Guiimartinho/esp32-s3-power-profiler/simulation/results/output_stage/README.md

# Simulation Results: Output Stage

Everything on this page is a simulation result. Nothing here is measured on
hardware. The page is written by `circuit-sim report` from the result files
beside it; do not edit it by hand.

## `output_stage/guard`

**The guard buffer: stability with the guard ring, static error, range change,
output off.**

The buffer copies the node after the shunts onto the guard ring through R119.
The loop gain of the buffer is taken by double injection at the output of the
amplifier, with the measured node behind the 1 kohm of range 0 and C71, which is
its highest impedance: without a ring, with the ring assumed for the board, with
ten times that ring, with C73 at half its value and with C73 left out. One
injection at the inverting input checks the method. A small-signal run gives the
frequency up to which the guard follows the node. Then the node is driven: a
step of 100 mV as a range change gives it, a dip to 1.1 V for 15 us as a short
circuit gives it, and a fall to 0 V at 0.8 V/ms as a released output gives it;
and it rests at 5 V and at 0.8 V, where the difference that is left between
guard and node is read.

Answers: sections 4.3, 4.8 and 10.3 (node after the shunts, buffer, guard ring),
D-32 and D-72.

| Figure | Simulated | Vendor models | Specification | Limits | Verdict | Source |
| --- | --- | --- | --- | --- | --- | --- |
| Phase margin, no ring capacitance | 92.06 ° | 117.8 ° | | at least 45 ° | pass | limit set here: 45 degrees; the specification states none |
| Crossover, no ring capacitance | 1.157 MHz | 1.507 MHz | | | | |
| Phase margin, assumed ring: 100 pF, 10 pF, 2 pF | 92.72 ° | 118.6 ° | | at least 45 ° | pass | limit set here: 45 degrees; the specification states none |
| Crossover, assumed ring: 100 pF, 10 pF, 2 pF | 1.147 MHz | 1.489 MHz | | | | |
| Phase margin, ten times the assumed ring | 96.84 ° | 123.9 ° | | at least 45 ° | pass | limit set here: 45 degrees; the specification states none |
| Crossover, ten times the assumed ring | 1.147 MHz | 1.549 MHz | | | | |
| Phase margin, assumed ring, C73 at half its value | 91.36 ° | 117.5 ° | | at least 45 ° | pass | limit set here: 45 degrees; the specification states none |
| Crossover, assumed ring, C73 at half its value | 1.144 MHz | 1.479 MHz | | | | |
| Phase margin, assumed ring, C73 not fitted | 55.61 ° | 72.97 ° | | | | |
| Crossover, assumed ring, C73 not fitted | 3.96 MHz | 4.986 MHz | | | | |
| Assumed ring: phase margin by one injection at the inverting input, less the one by double injection | -0.1481 ° | -0.02715 ° | | -3 ° to 3 ° | pass | check of the method; limit set here |
| Frequency up to which the guard follows the node within 3 dB | 34.73 kHz | 34.73 kHz | 33.83 kHz (+2.67 %) | 30.45 kHz to 37.21 kHz | pass | R119 with C73 and the ring, calculated here; limit 10 % around it |
| Peaking of the guard over the node | 0 dB | 0 dB | | at most 1 dB | pass | limit set here |
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
