Guiimartinho/esp32-s3-power-profiler/simulation/results/output_stage/guard.events.png

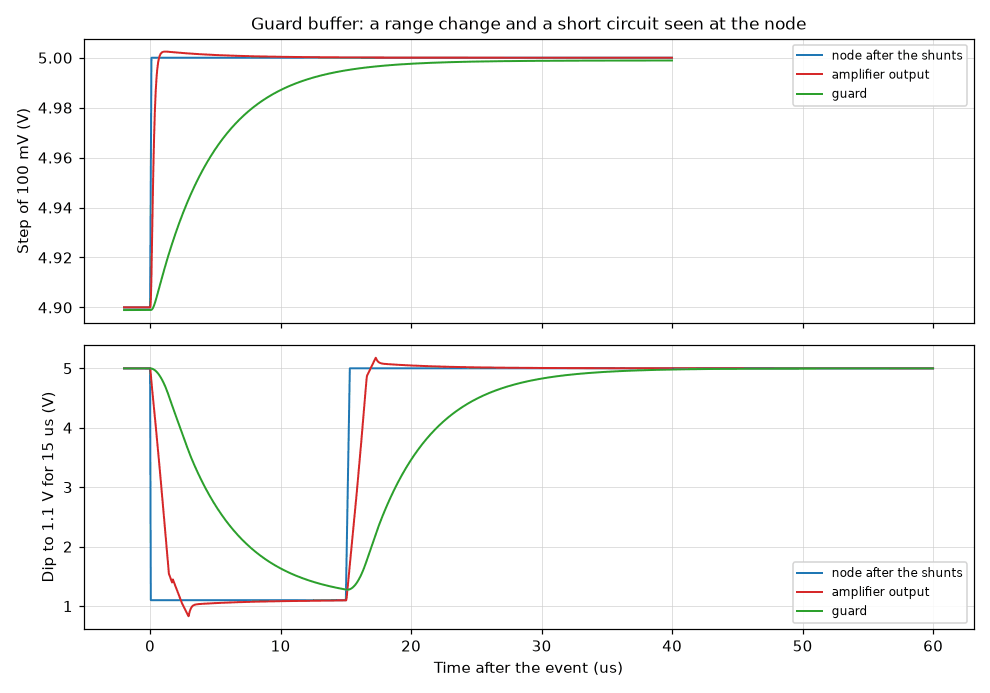
simulation/results/output_stage/guard.events.png
