Guiimartinho/esp32-s3-power-profiler/simulation/results/output_stage/guard.loop.png

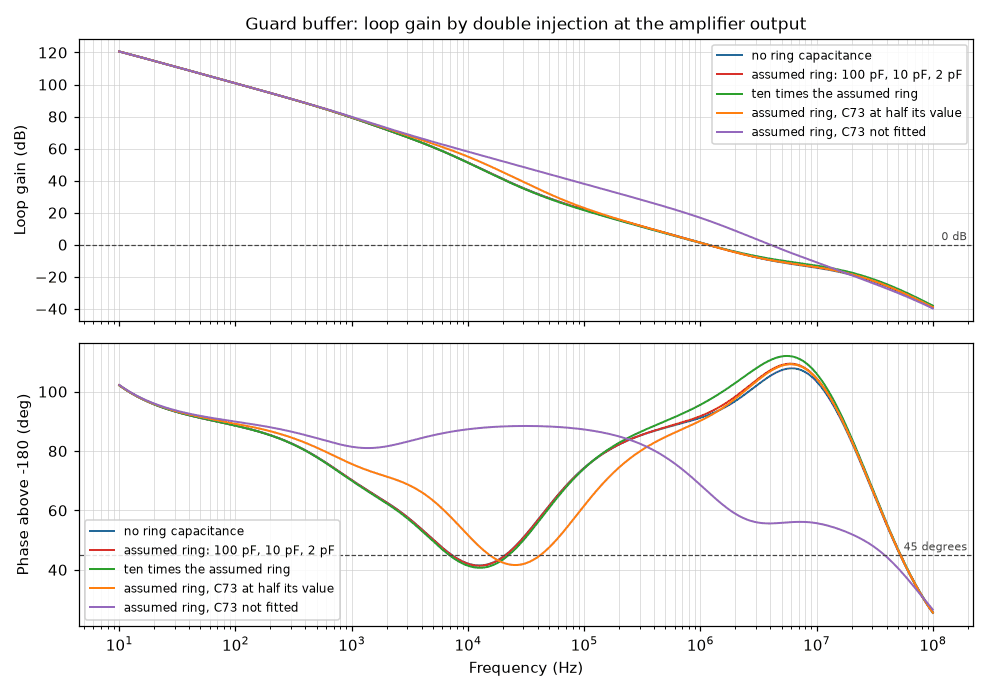
simulation/results/output_stage/guard.loop.png
