Guiimartinho/esp32-s3-power-profiler/simulation/results/output_stage/on-resistance.resistance.png

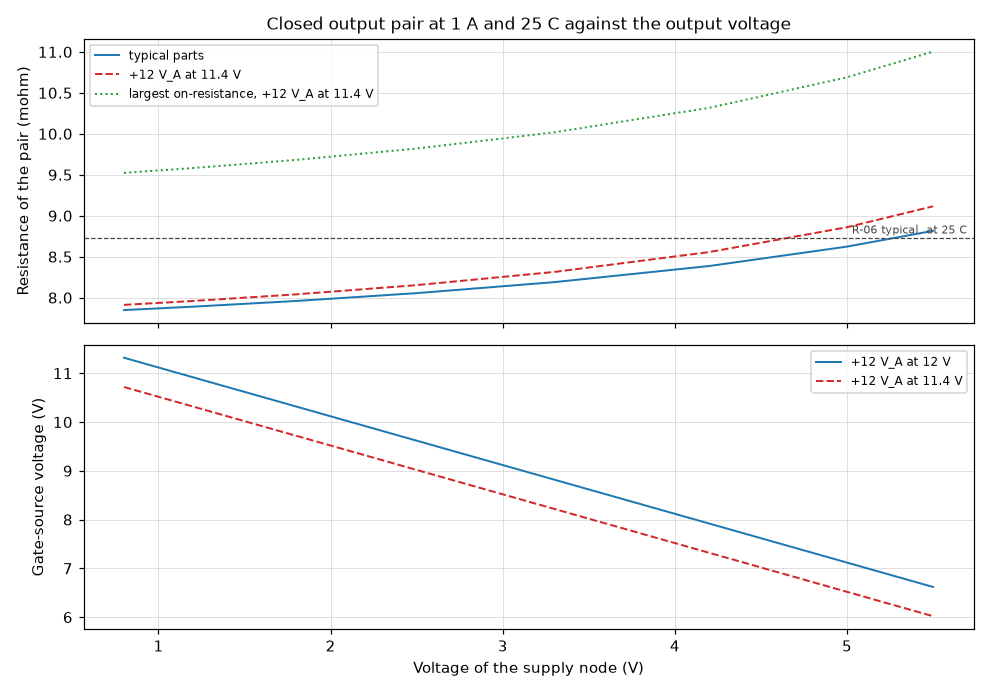
simulation/results/output_stage/on-resistance.resistance.png
