Guiimartinho/esp32-s3-power-profiler/simulation/results/output_stage/short-circuit.waveforms.png

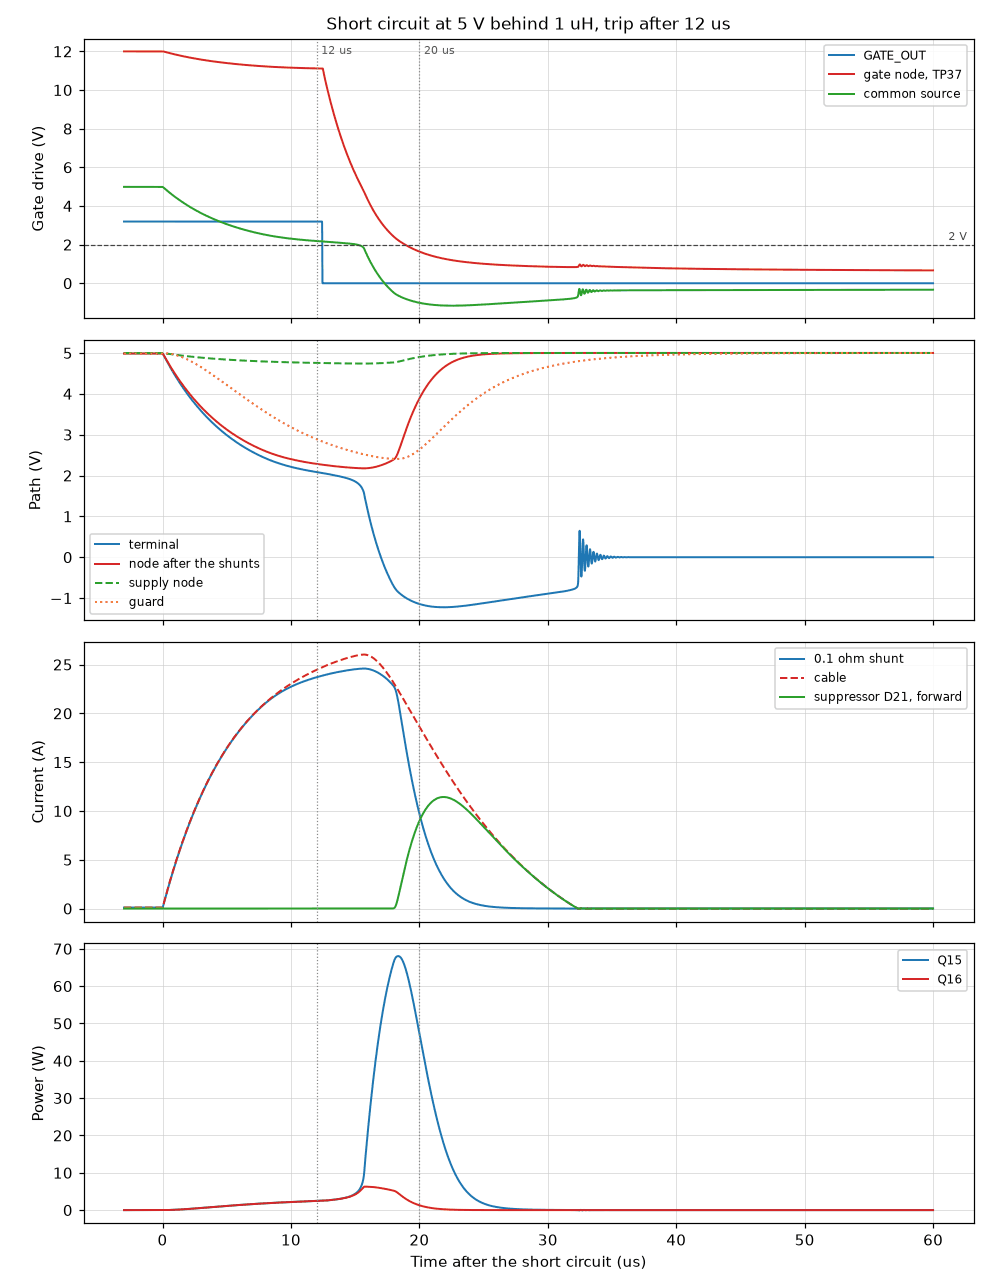
simulation/results/output_stage/short-circuit.waveforms.png
