Guiimartinho/esp32-s3-power-profiler/simulation/results/output_stage/terminal.charged.png

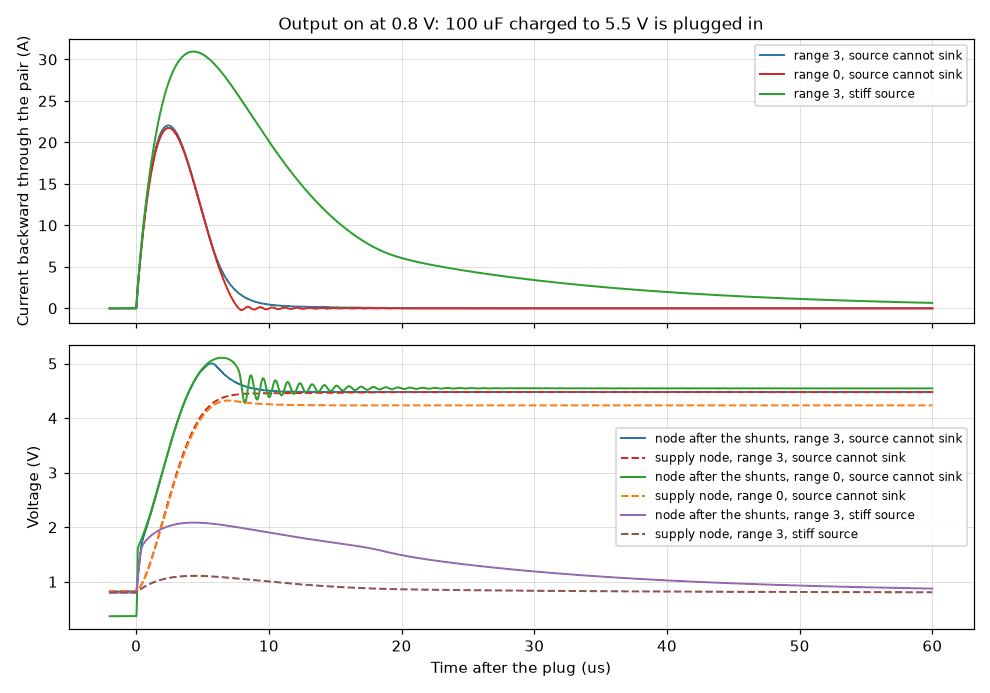
simulation/results/output_stage/terminal.charged.png
