Guiimartinho/esp32-s3-power-profiler/simulation/results/output_stage/terminal.reversed.png

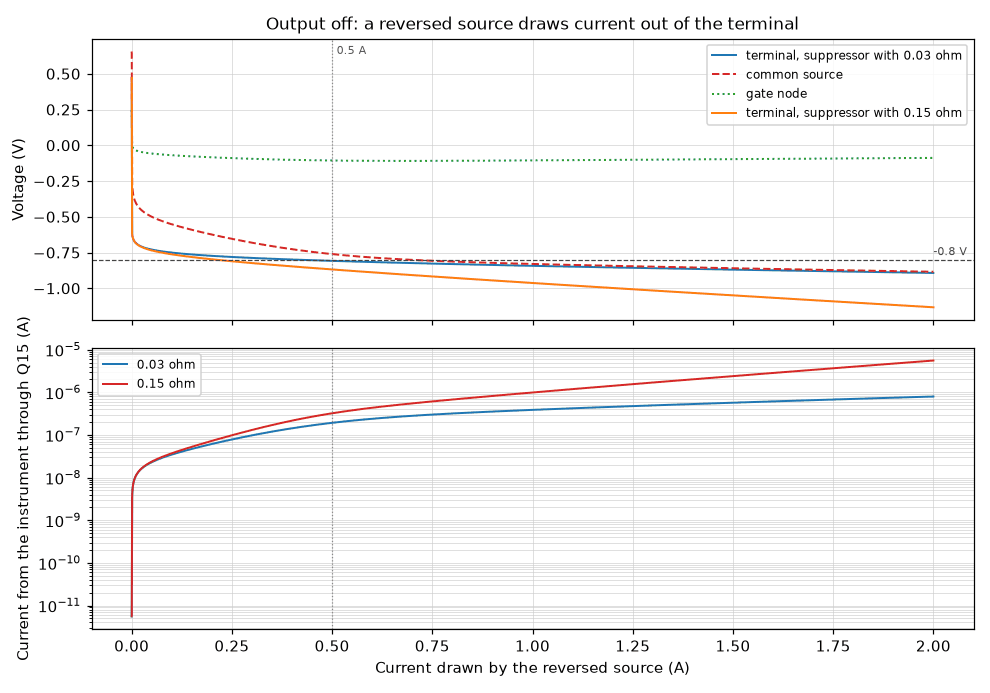
simulation/results/output_stage/terminal.reversed.png
