Guiimartinho/esp32-s3-power-profiler/simulation/results/output_stage/turn-off.plain.png

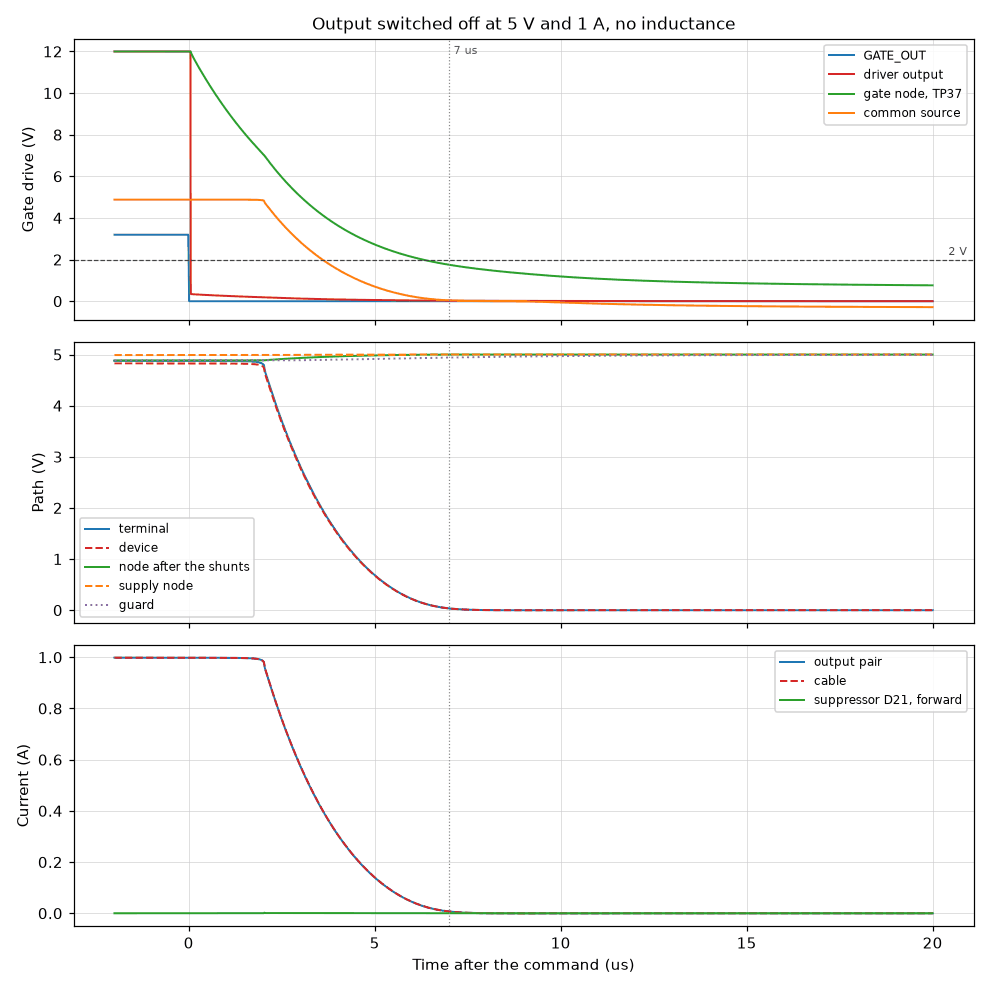
simulation/results/output_stage/turn-off.plain.png
