Guiimartinho/esp32-s3-power-profiler/simulation/results/output_stage/turn-on.faults.png

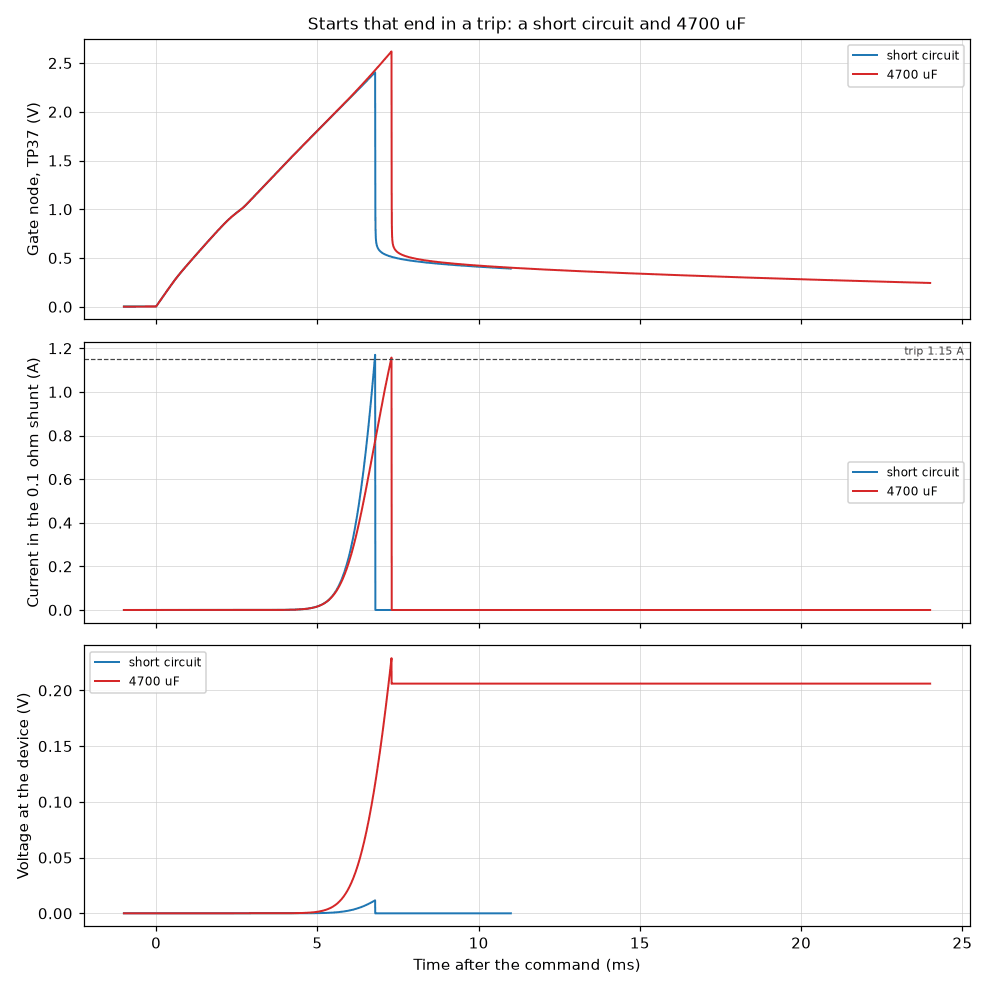
simulation/results/output_stage/turn-on.faults.png
