Guiimartinho/esp32-s3-power-profiler/simulation/results/output_stage/turn-on.gate-current.png

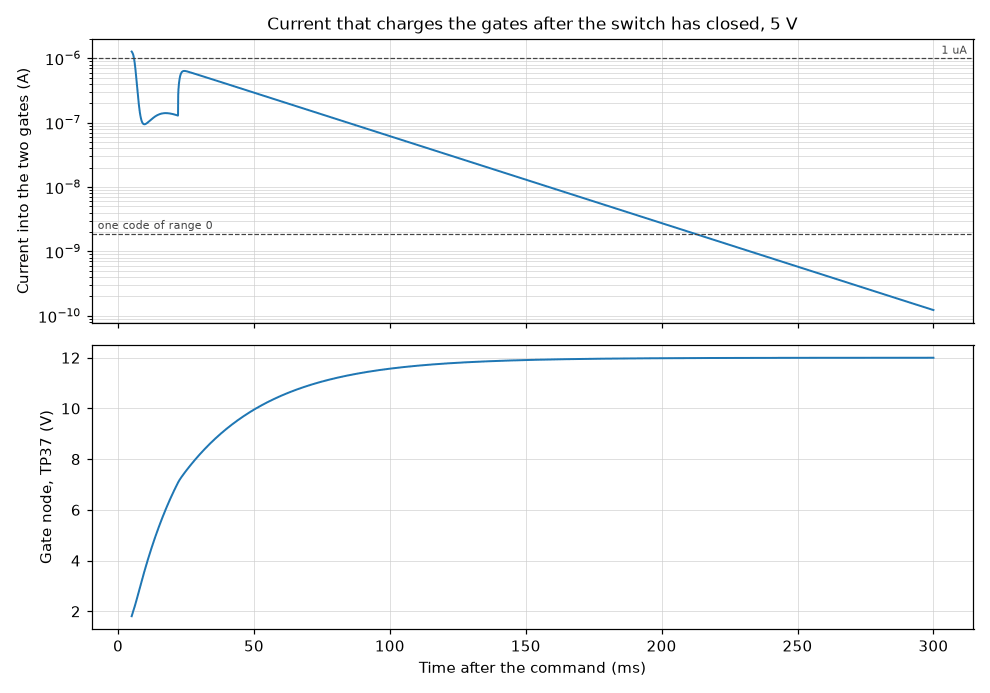
simulation/results/output_stage/turn-on.gate-current.png
