Guiimartinho/esp32-s3-power-profiler/simulation/results/output_stage/turn-on.inrush.png

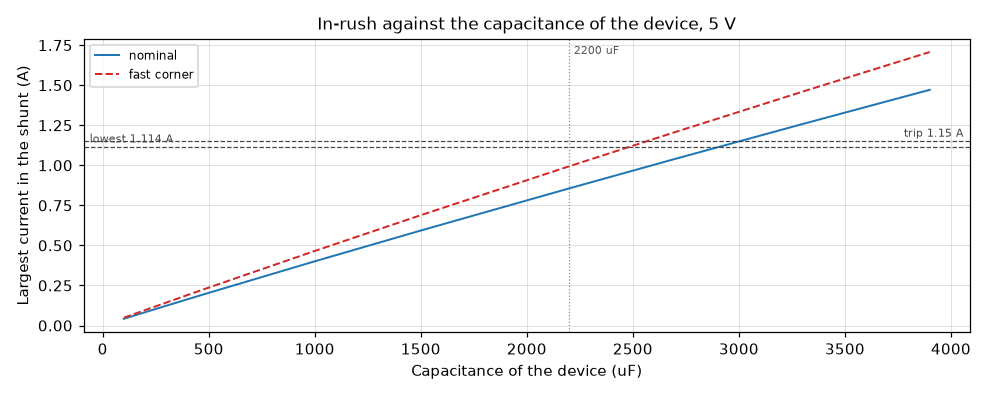
simulation/results/output_stage/turn-on.inrush.png
