Guiimartinho/esp32-s3-power-profiler/simulation/results/output_stage/turn-on.waveforms.png

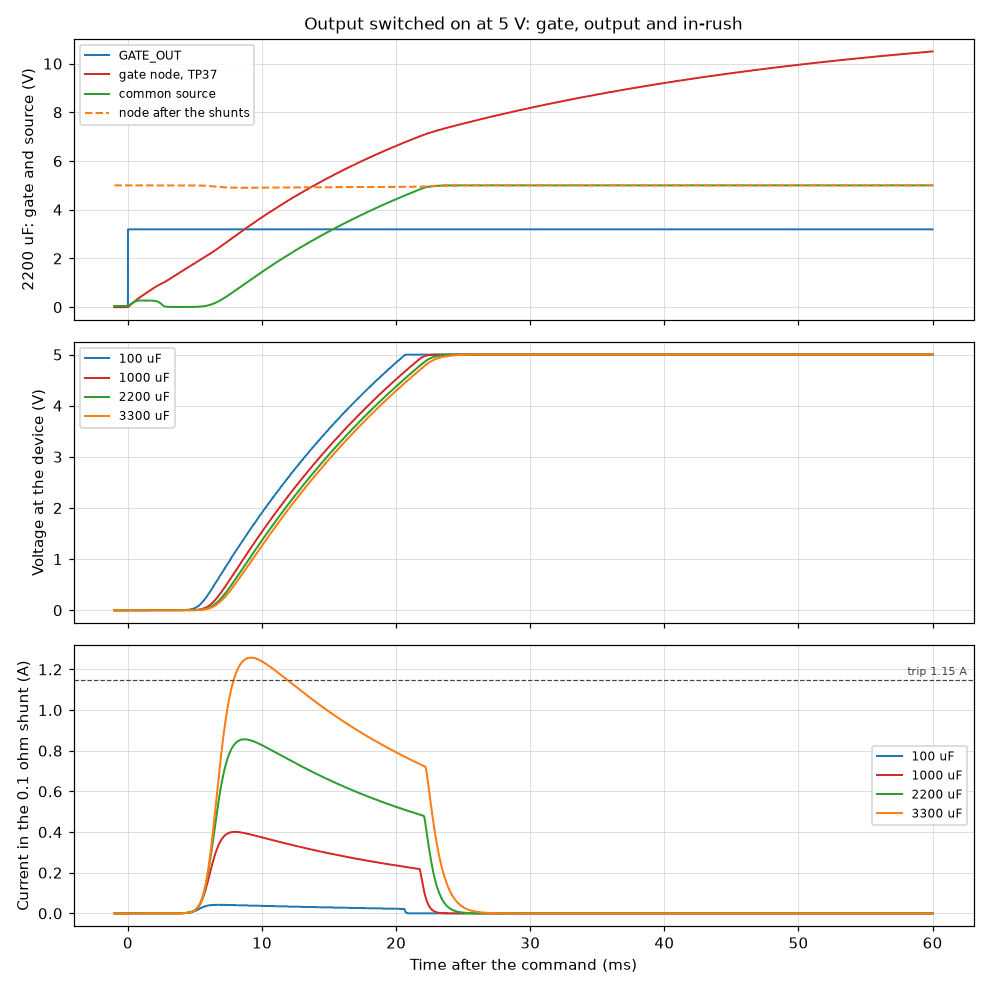
simulation/results/output_stage/turn-on.waveforms.png
