Guiimartinho/esp32-s3-power-profiler/simulation/results/path_switching/close.all.png

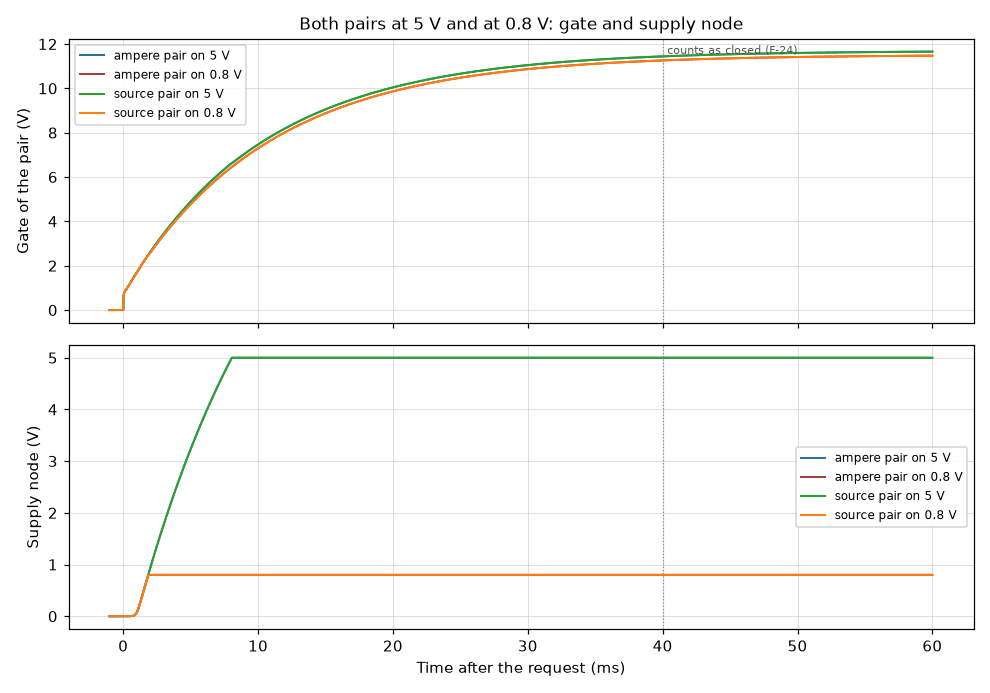
simulation/results/path_switching/close.all.png
