Guiimartinho/esp32-s3-power-profiler/simulation/results/path_switching/close.ampere-5v.png

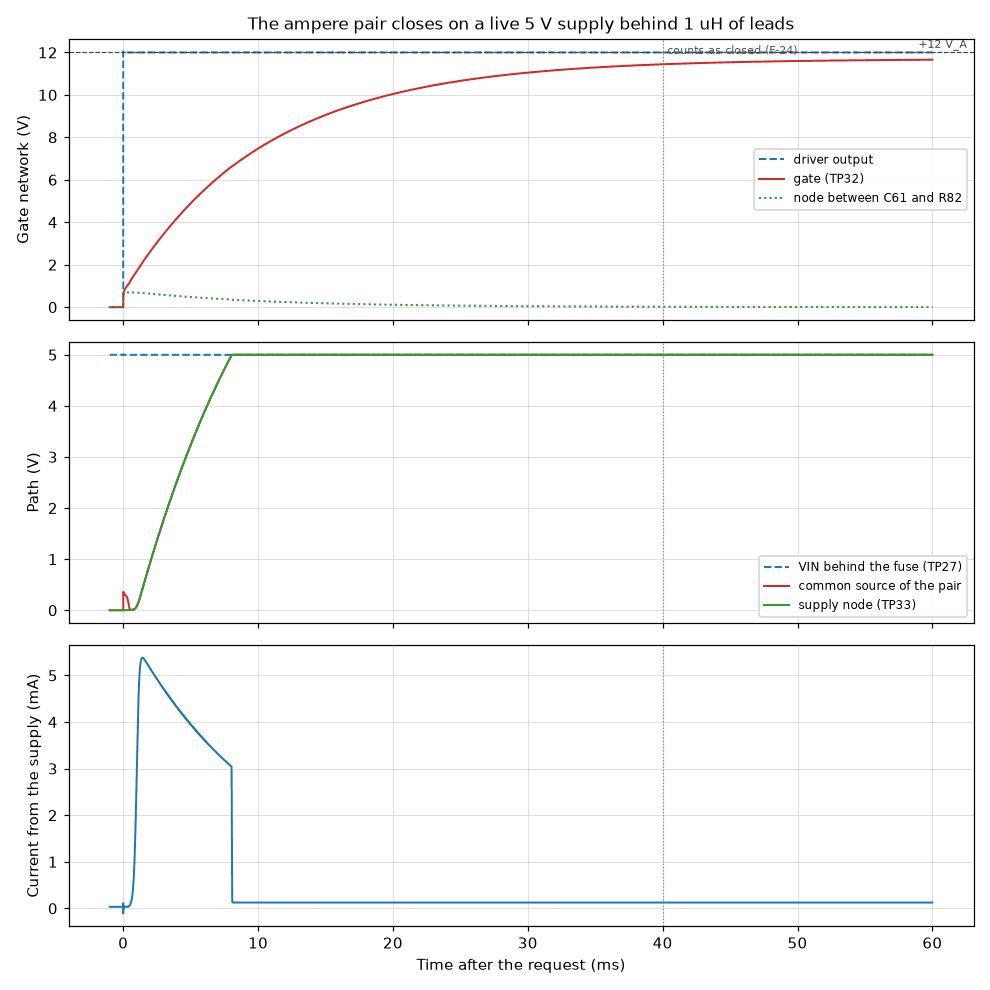
simulation/results/path_switching/close.ampere-5v.png
