Guiimartinho/esp32-s3-power-profiler/simulation/results/path_switching/detector.levels.png

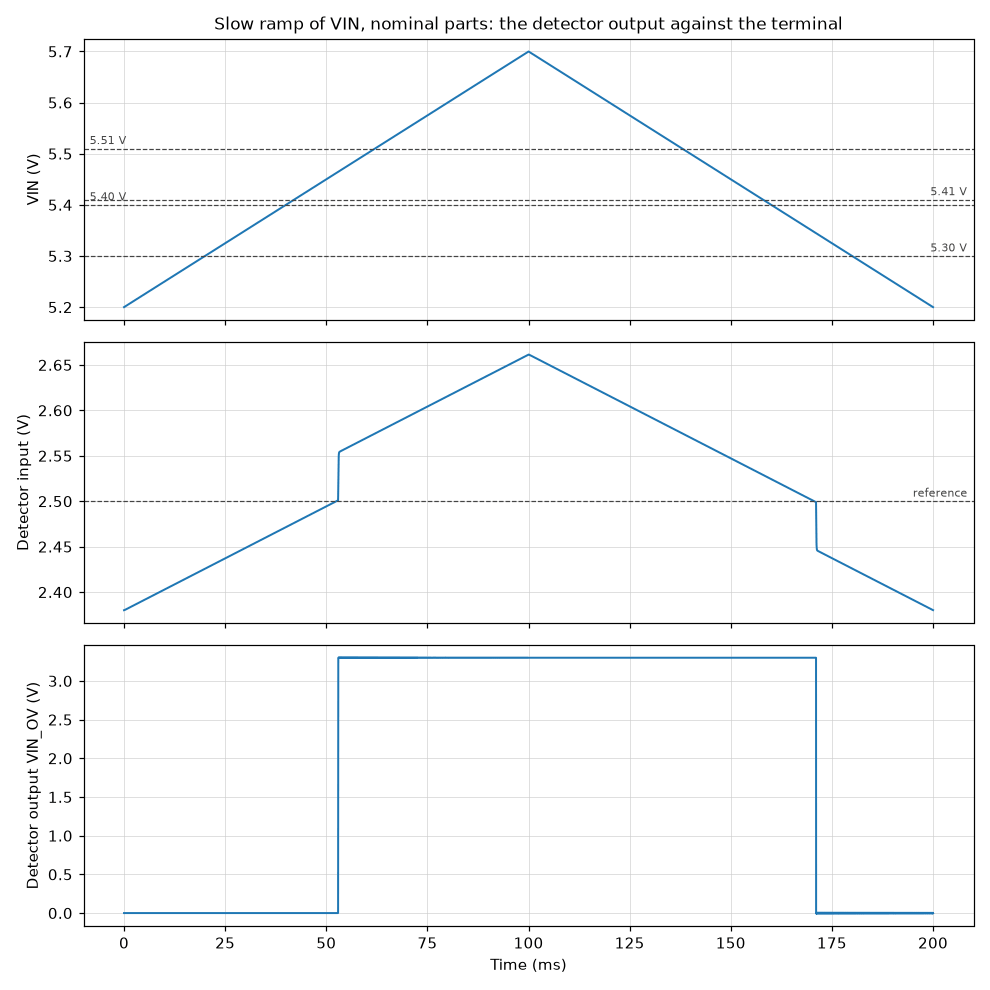
simulation/results/path_switching/detector.levels.png
