Guiimartinho/esp32-s3-power-profiler/simulation/results/path_switching/detector.reaction.png

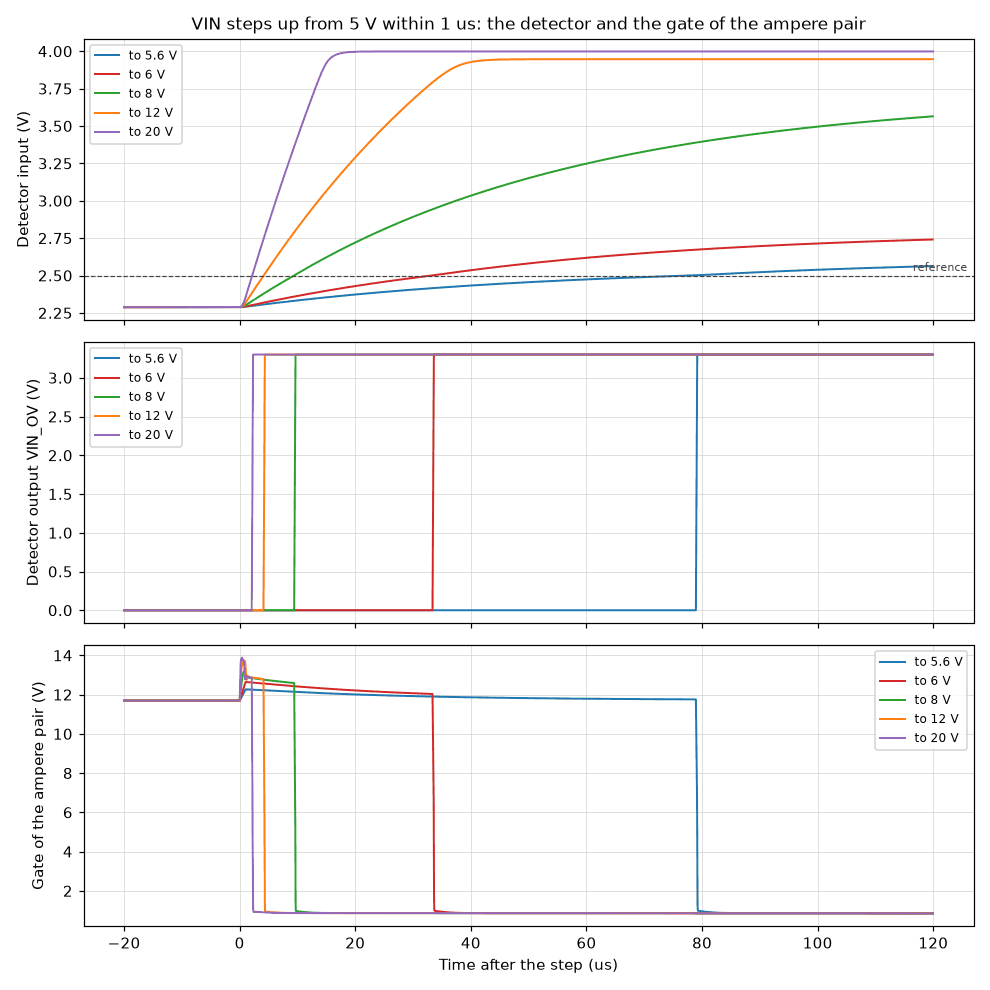
simulation/results/path_switching/detector.reaction.png
