Guiimartinho/esp32-s3-power-profiler/simulation/results/path_switching/drop.drop.png

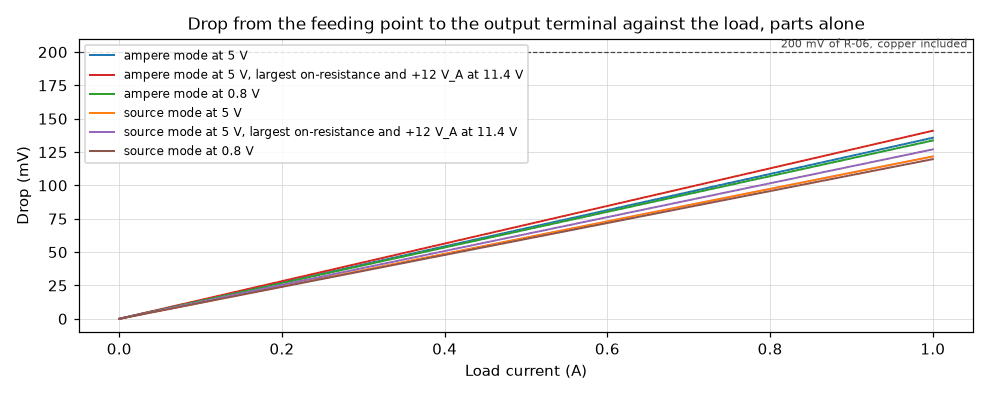
simulation/results/path_switching/drop.drop.png
