Guiimartinho/esp32-s3-power-profiler/simulation/results/path_switching/hand-over.to-ampere.png

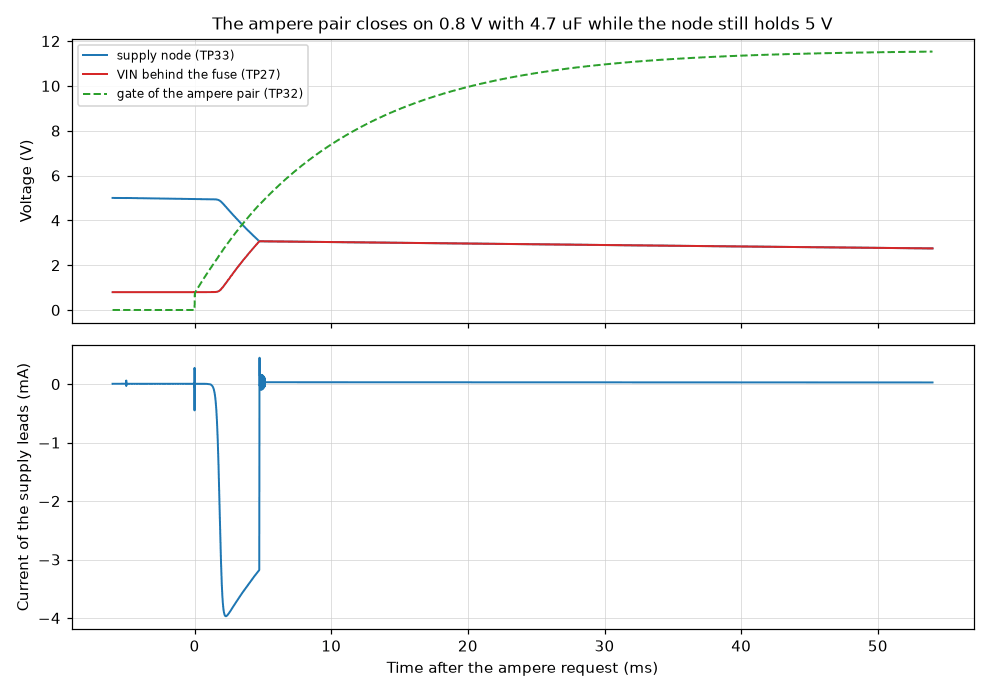
simulation/results/path_switching/hand-over.to-ampere.png
