Guiimartinho/esp32-s3-power-profiler/simulation/results/path_switching/idle.decay.png

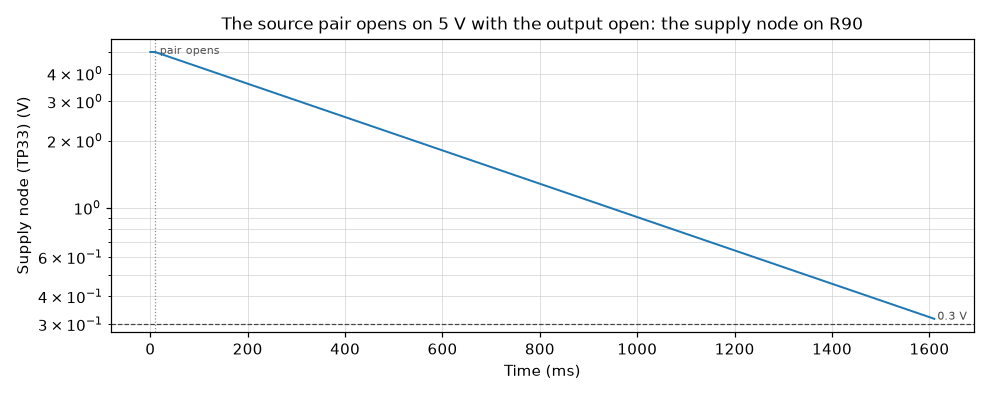
simulation/results/path_switching/idle.decay.png
