Guiimartinho/esp32-s3-power-profiler/simulation/results/path_switching/interlock.added.png

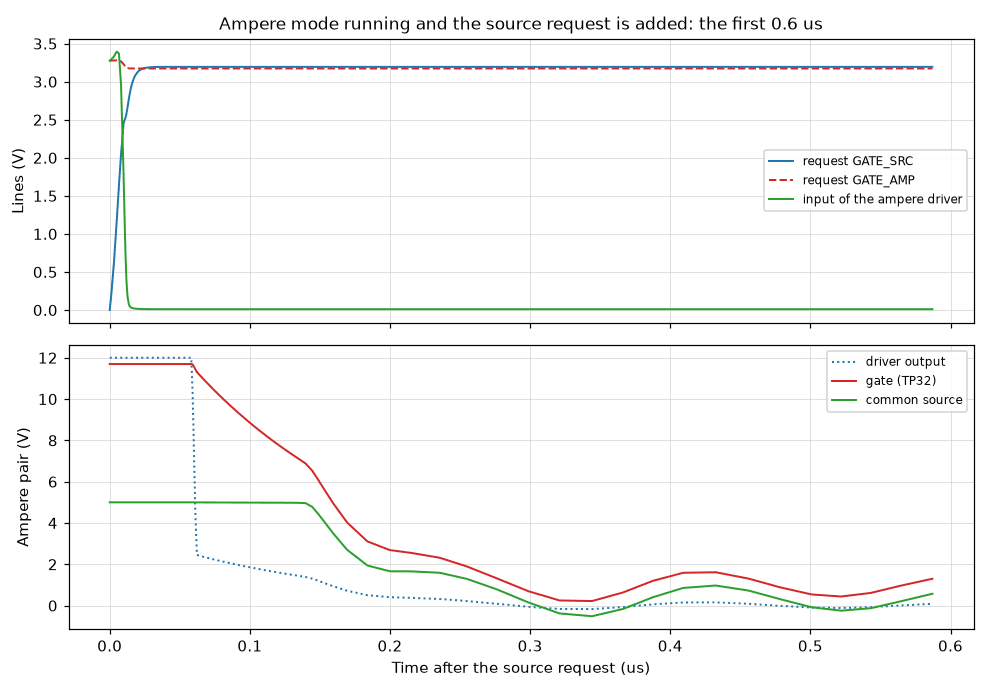
simulation/results/path_switching/interlock.added.png
