Guiimartinho/esp32-s3-power-profiler/simulation/results/path_switching/interlock.both.png

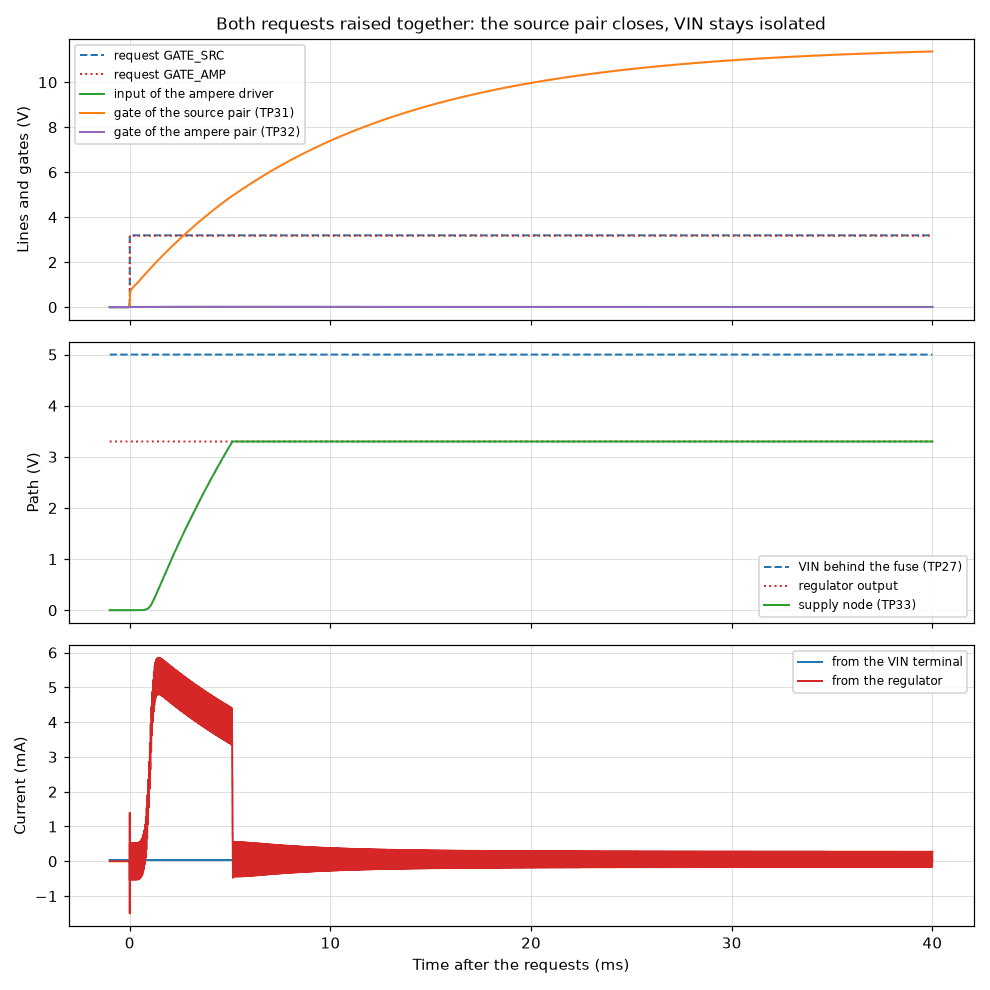
simulation/results/path_switching/interlock.both.png
