Guiimartinho/esp32-s3-power-profiler/simulation/results/path_switching/interlock.to-source.png

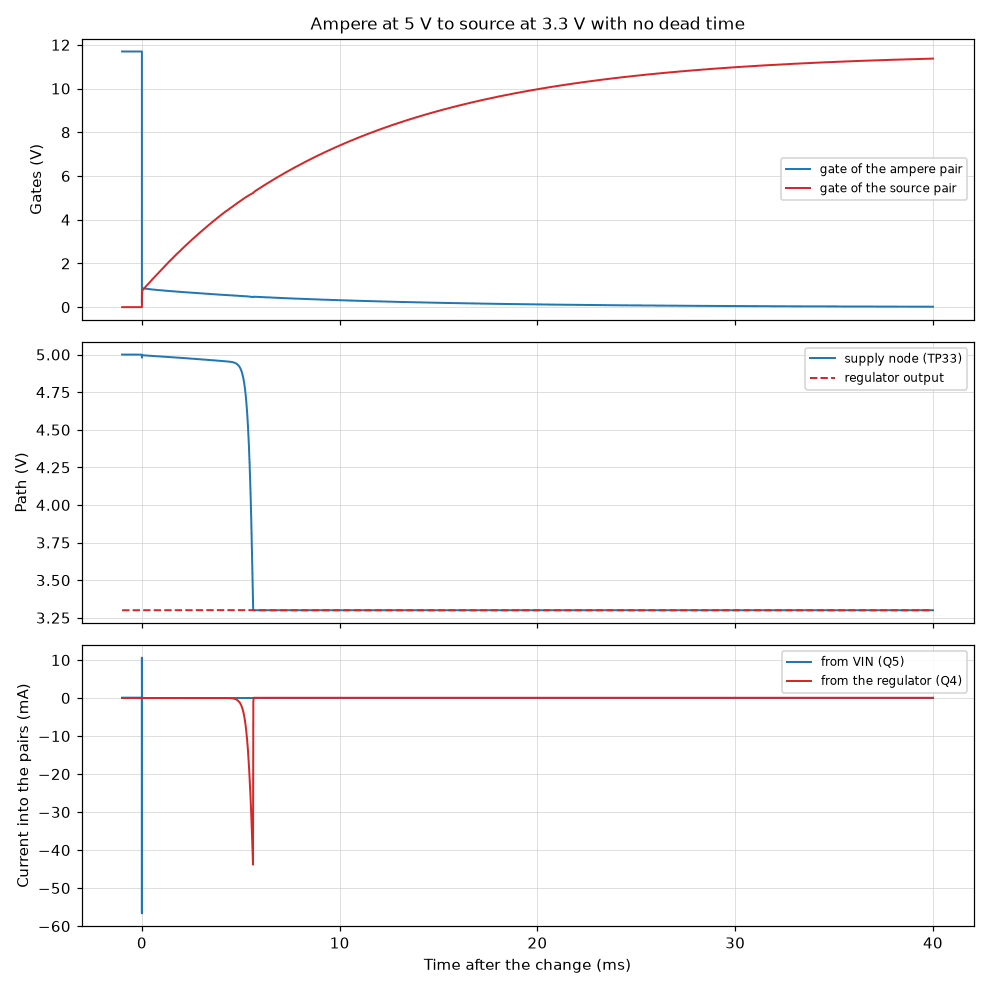
simulation/results/path_switching/interlock.to-source.png
