Guiimartinho/esp32-s3-power-profiler/simulation/results/path_switching/open.ampere-1a.png

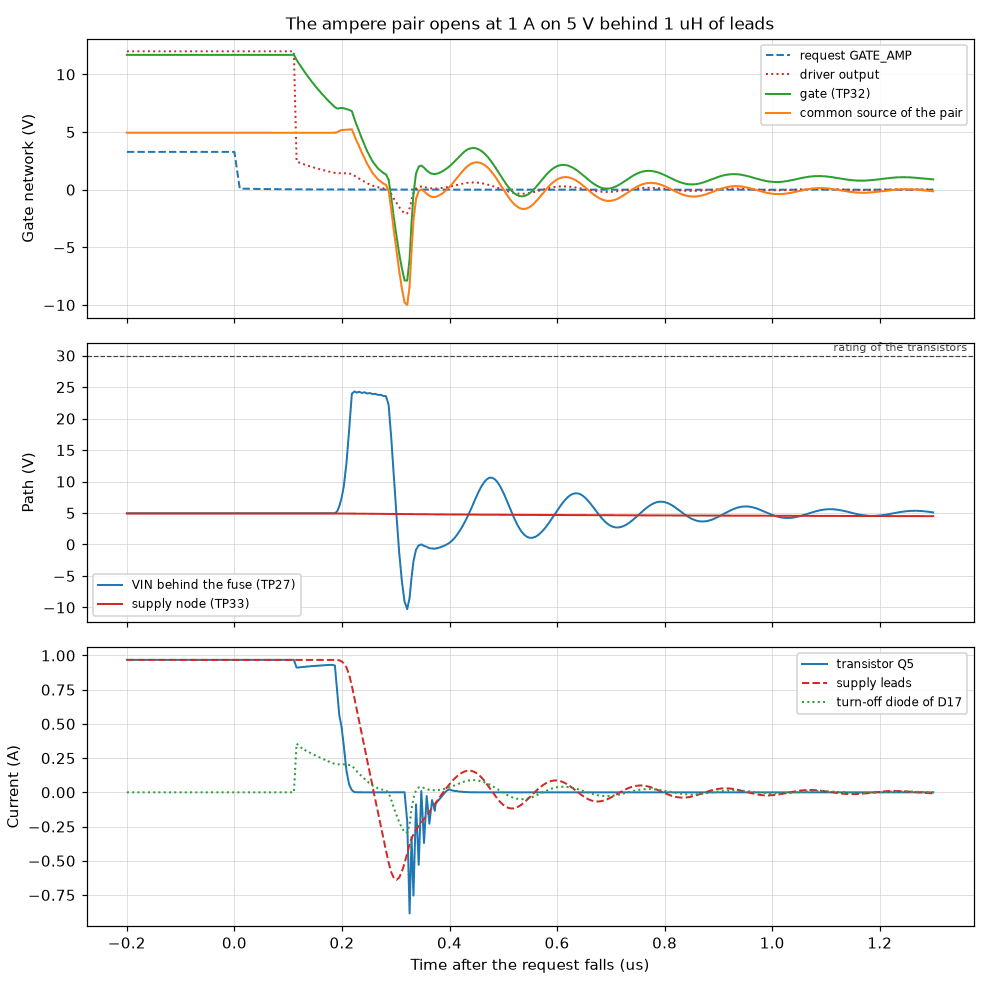
simulation/results/path_switching/open.ampere-1a.png
