Guiimartinho/esp32-s3-power-profiler/simulation/results/path_switching/open.rest.png

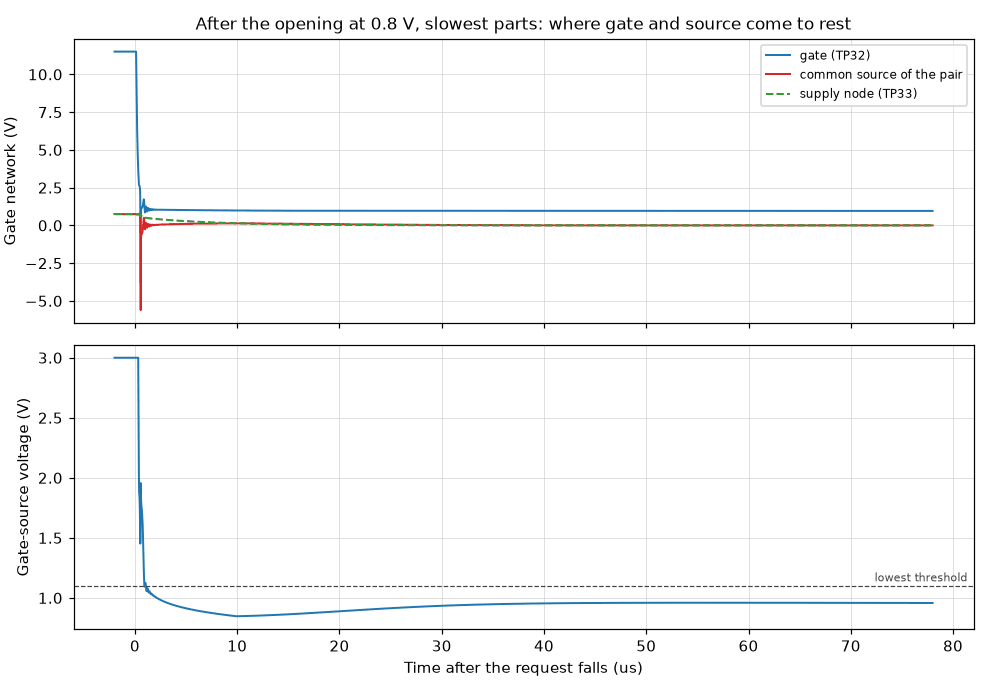
simulation/results/path_switching/open.rest.png
