Guiimartinho/esp32-s3-power-profiler/simulation/results/path_switching/overvoltage.release.png

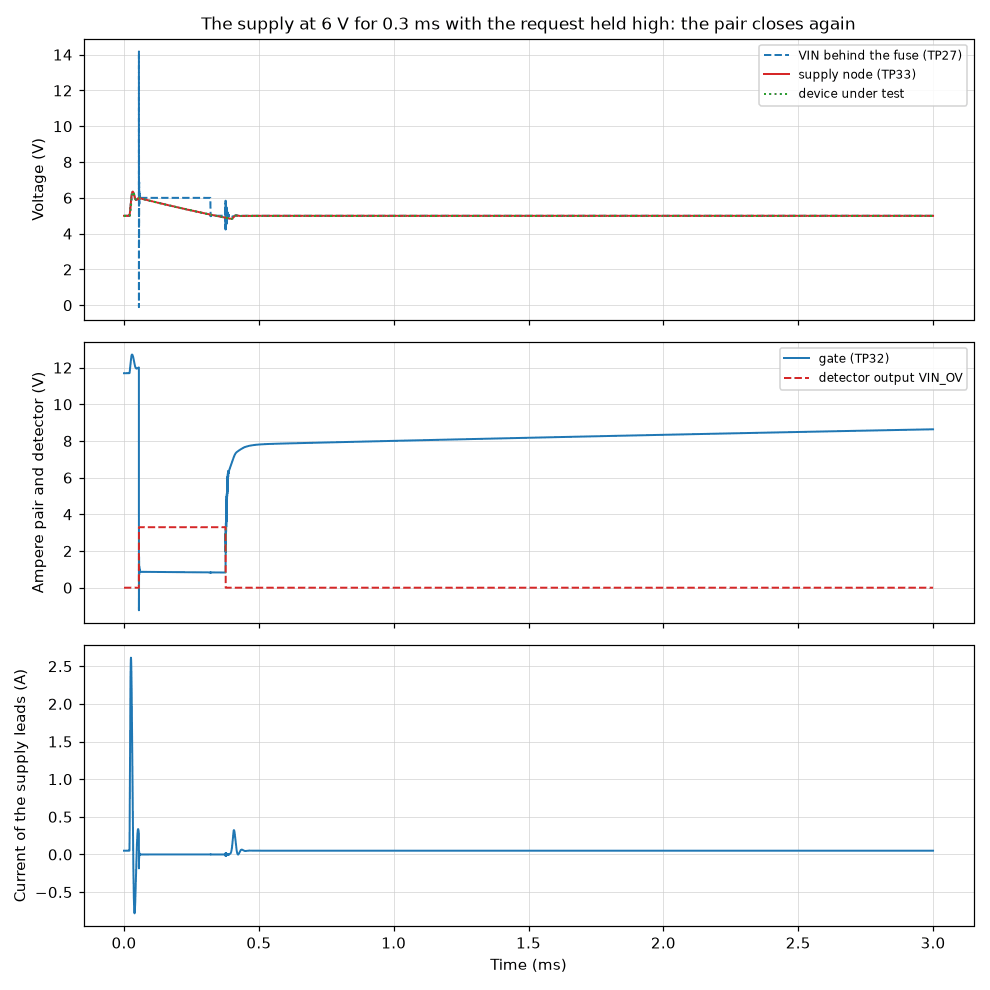
simulation/results/path_switching/overvoltage.release.png
