Guiimartinho/esp32-s3-power-profiler/simulation/results/path_switching/overvoltage.to-20v.png

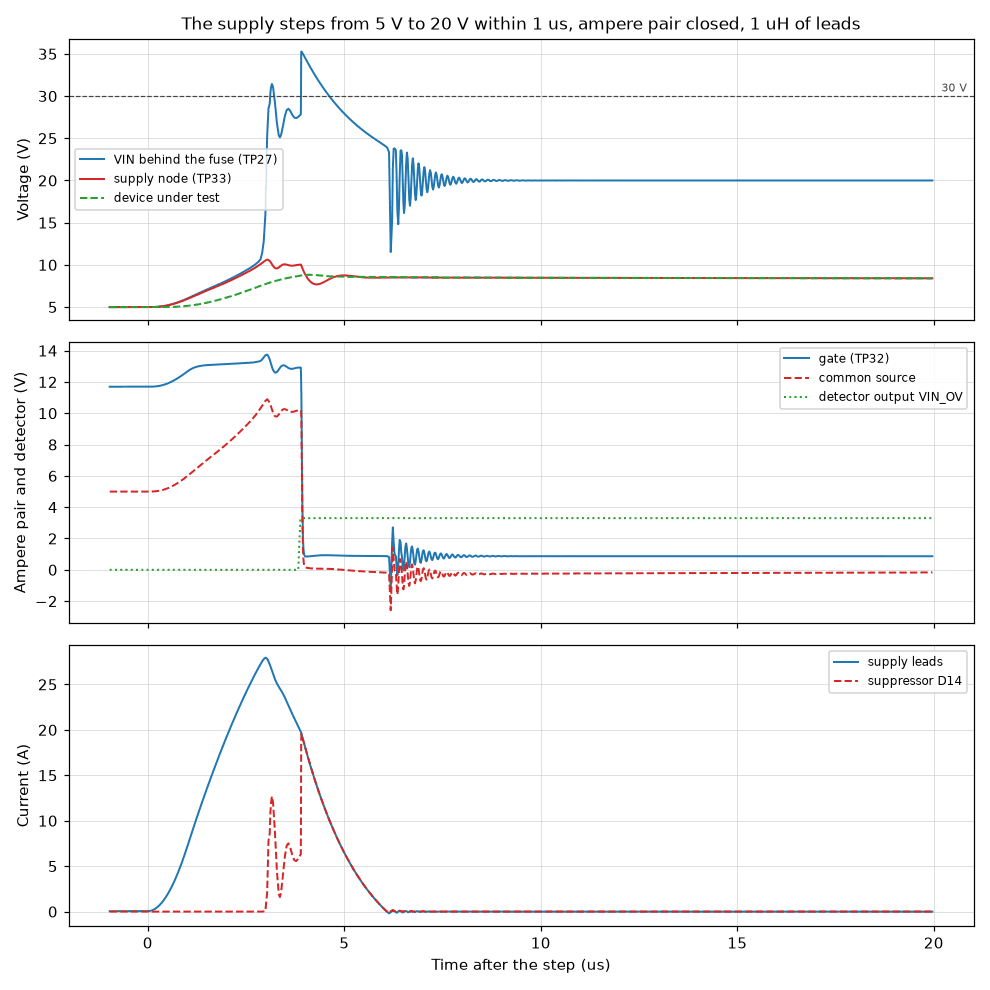
simulation/results/path_switching/overvoltage.to-20v.png
