Guiimartinho/esp32-s3-power-profiler/simulation/results/path_switching/plug.reverse.png

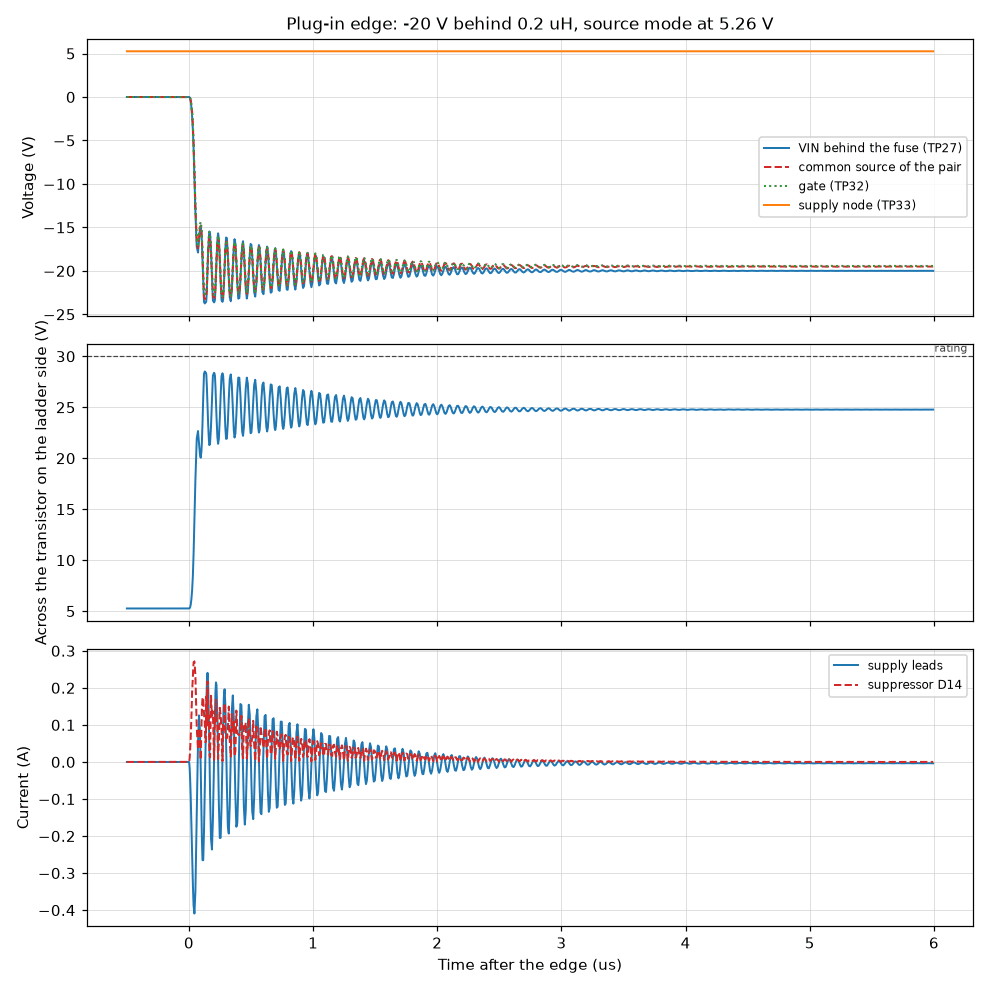
simulation/results/path_switching/plug.reverse.png
