Guiimartinho/esp32-s3-power-profiler/simulation/results/path_switching/reversal.limited.png

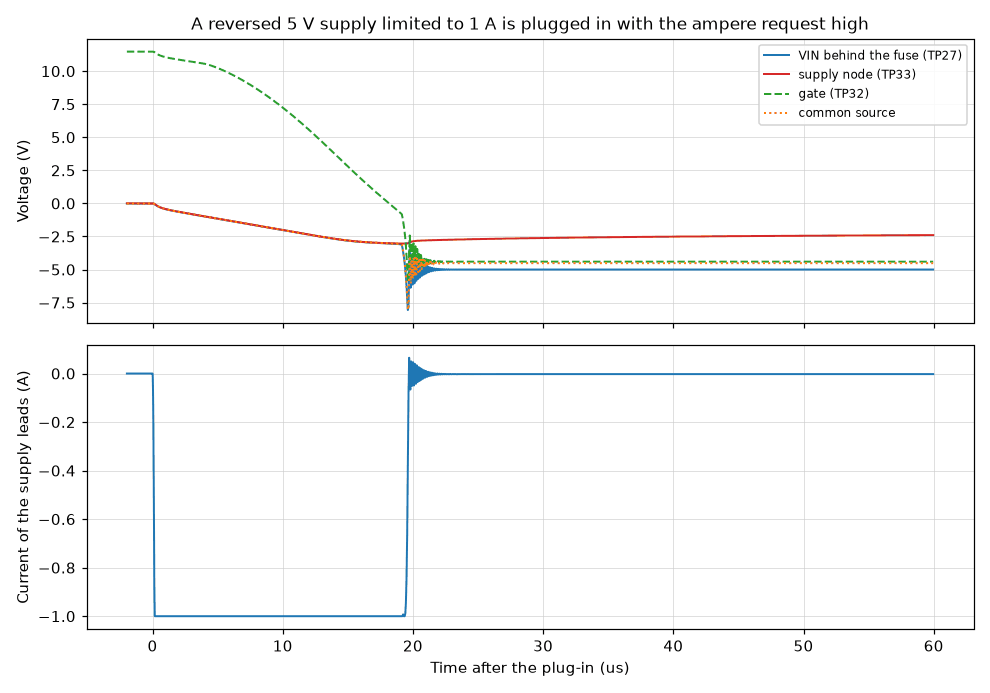
simulation/results/path_switching/reversal.limited.png
