Guiimartinho/esp32-s3-power-profiler/simulation/results/path_switching/reversal.to-minus-20v.png

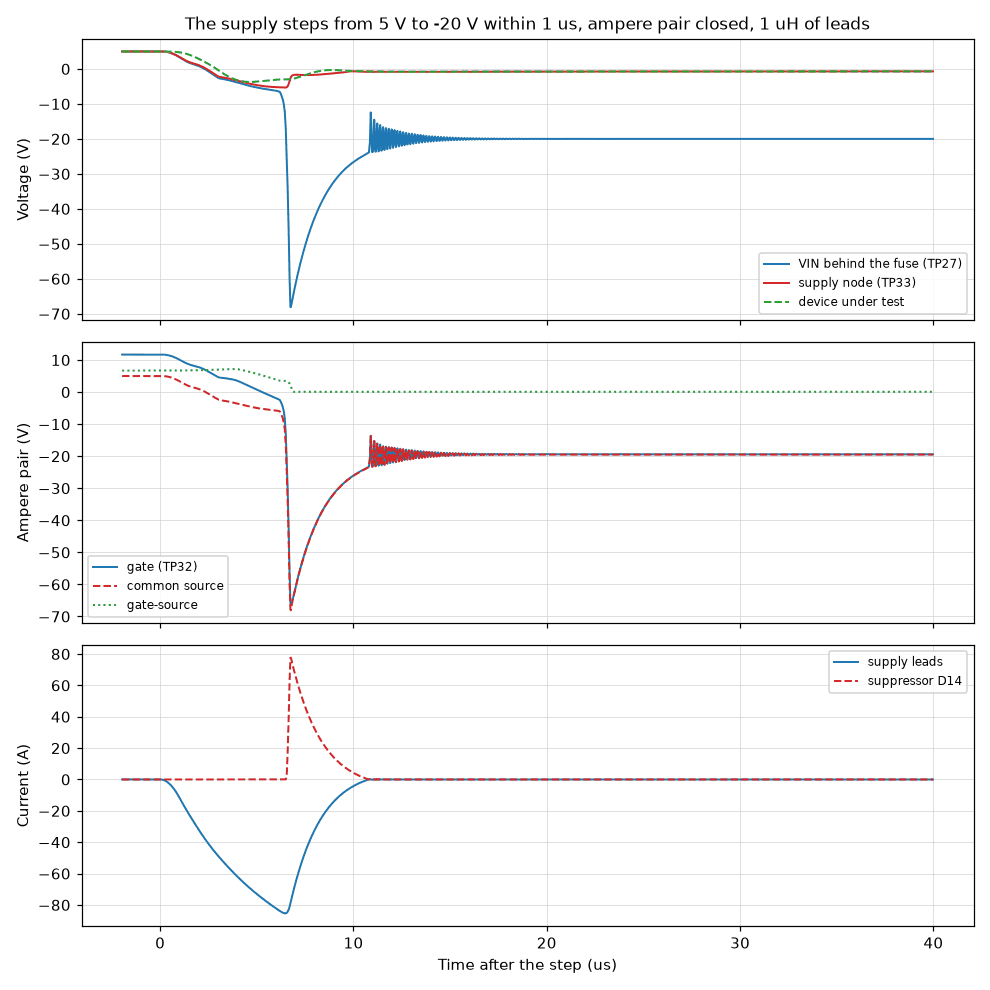
simulation/results/path_switching/reversal.to-minus-20v.png
