Guiimartinho/esp32-s3-power-profiler/simulation/results/path_switching/ring.shunt.png

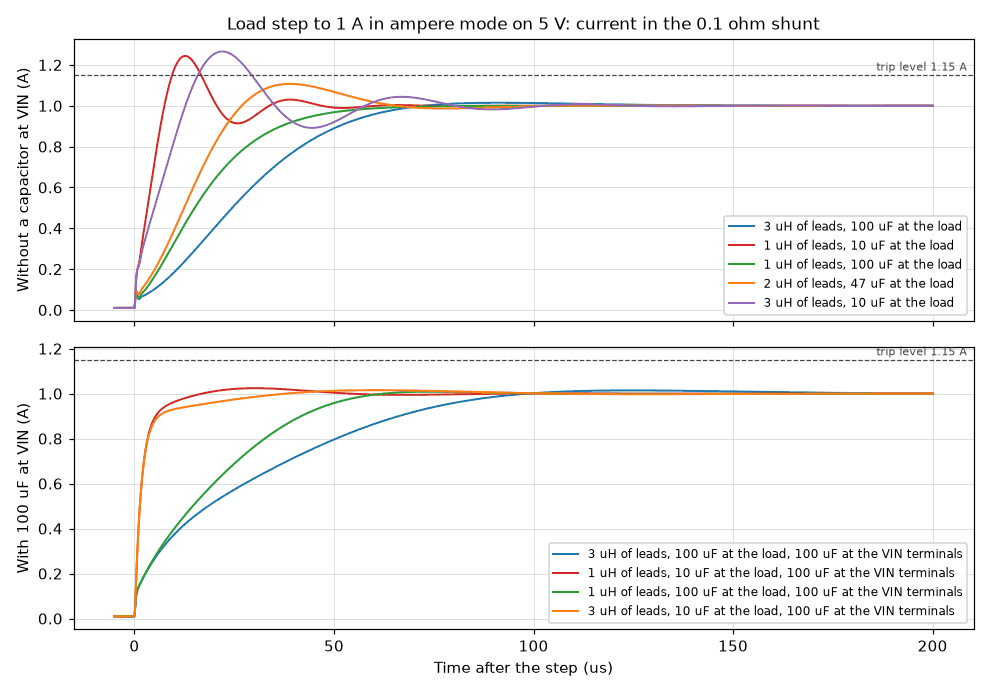
simulation/results/path_switching/ring.shunt.png
