Guiimartinho/esp32-s3-power-profiler/simulation/results/path_switching/short.all.png

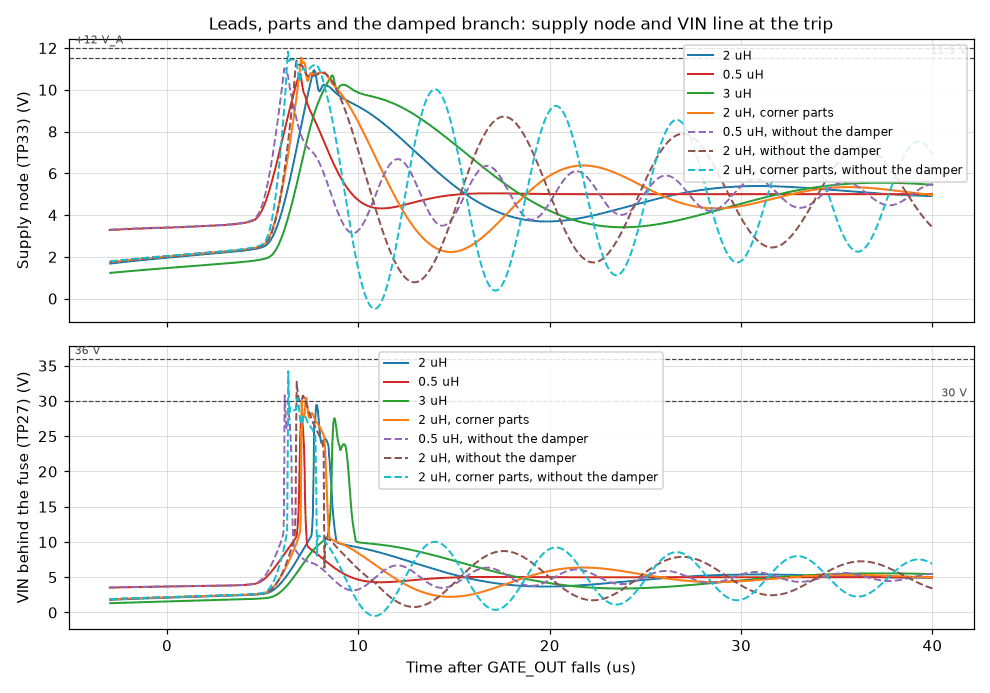
simulation/results/path_switching/short.all.png
