Guiimartinho/esp32-s3-power-profiler/simulation/results/path_switching/short.kick.png

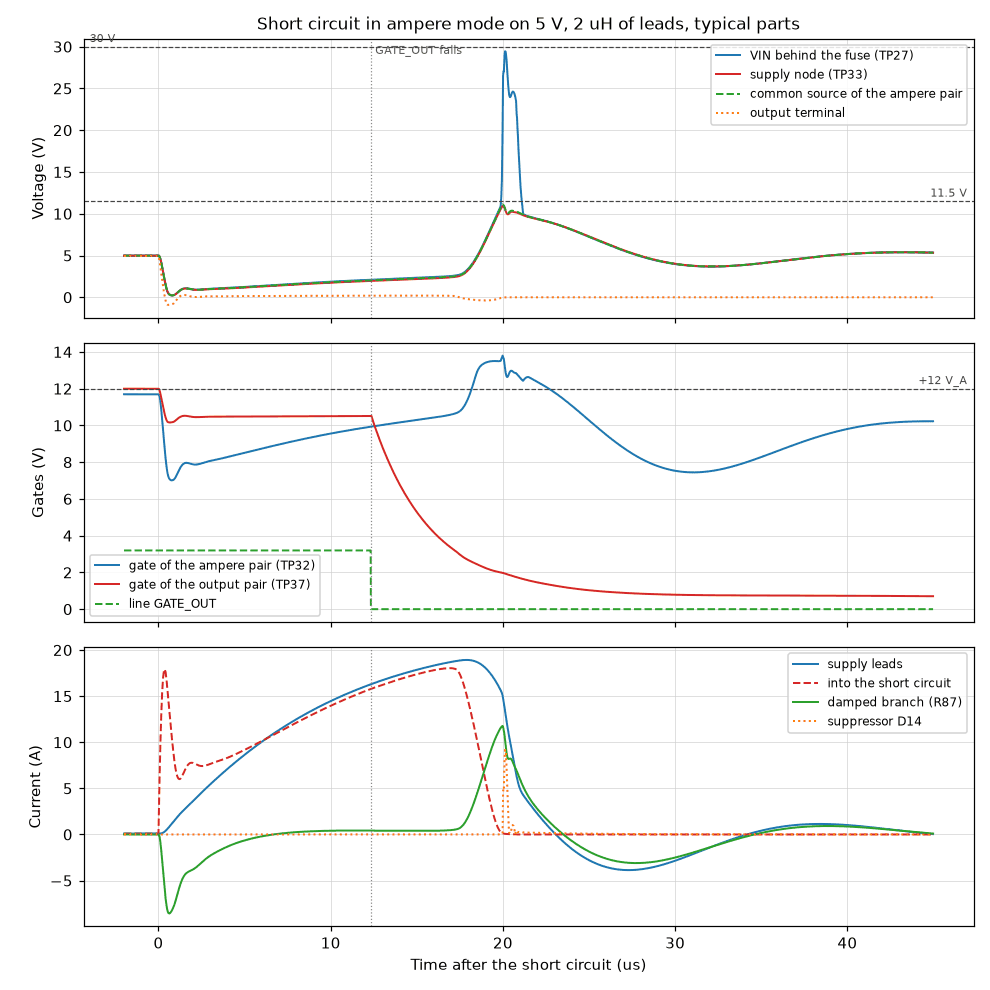
simulation/results/path_switching/short.kick.png
