Guiimartinho/esp32-s3-power-profiler/simulation/results/path_switching/trip.release.png

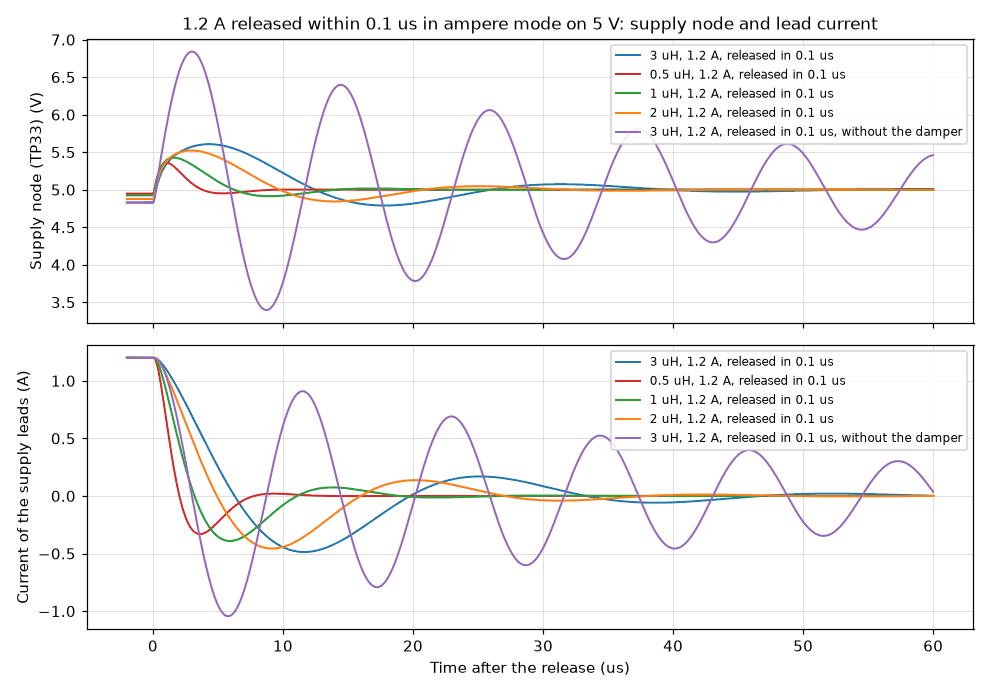
simulation/results/path_switching/trip.release.png
