Guiimartinho/esp32-s3-power-profiler/simulation/results/path_switching/withstand.terminal.png

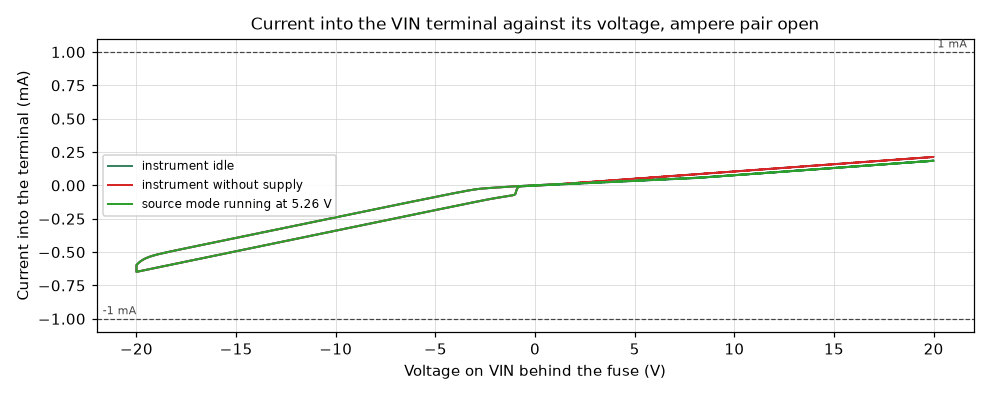
simulation/results/path_switching/withstand.terminal.png
