Guiimartinho/esp32-s3-power-profiler/simulation/results/power_input/contact-bounce.start.png

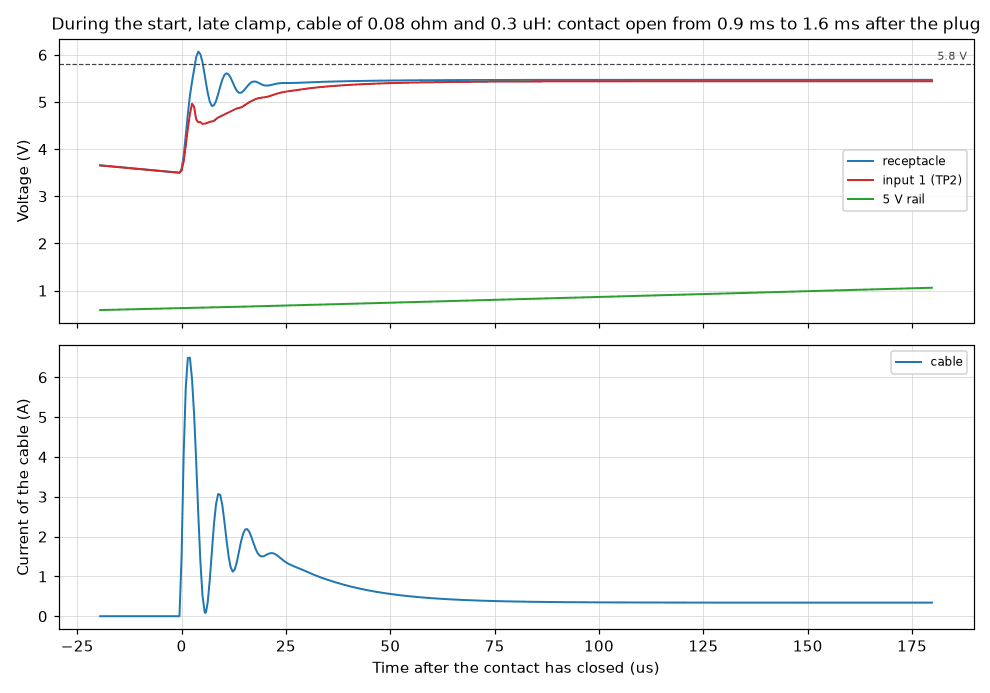
simulation/results/power_input/contact-bounce.start.png
