Guiimartinho/esp32-s3-power-profiler/simulation/results/power_input/current-limit.short.png

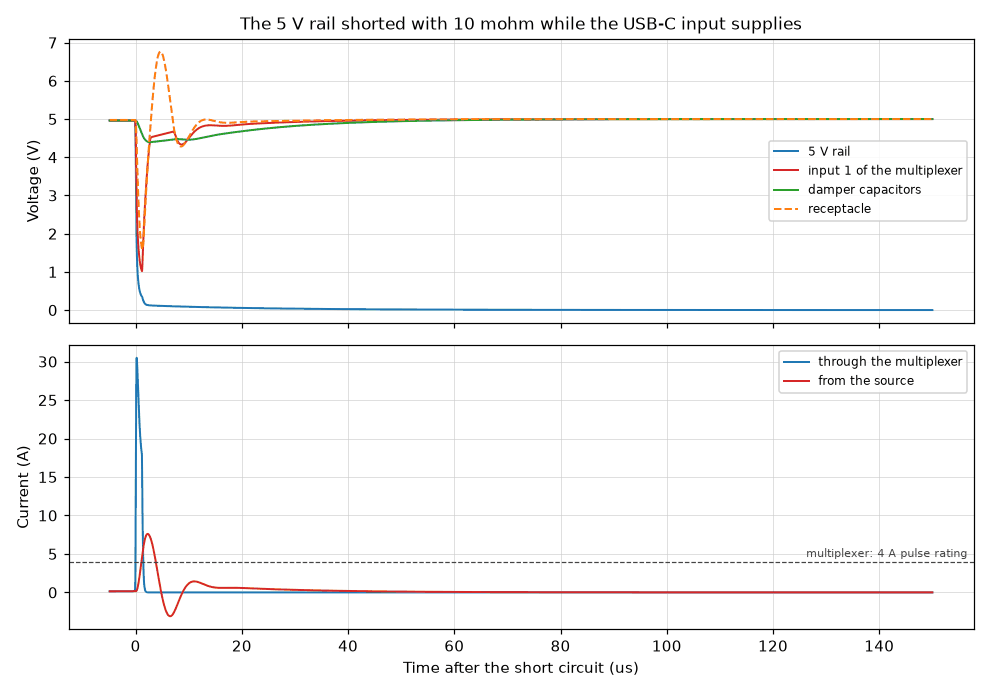
simulation/results/power_input/current-limit.short.png
