Guiimartinho/esp32-s3-power-profiler/simulation/results/power_input/logic-rails.start.png

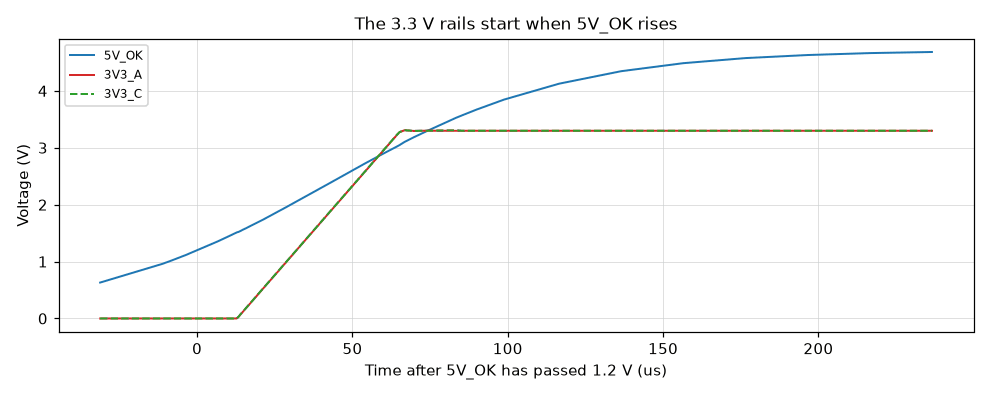
simulation/results/power_input/logic-rails.start.png
