Guiimartinho/esp32-s3-power-profiler/simulation/results/power_input/overload.shed.png

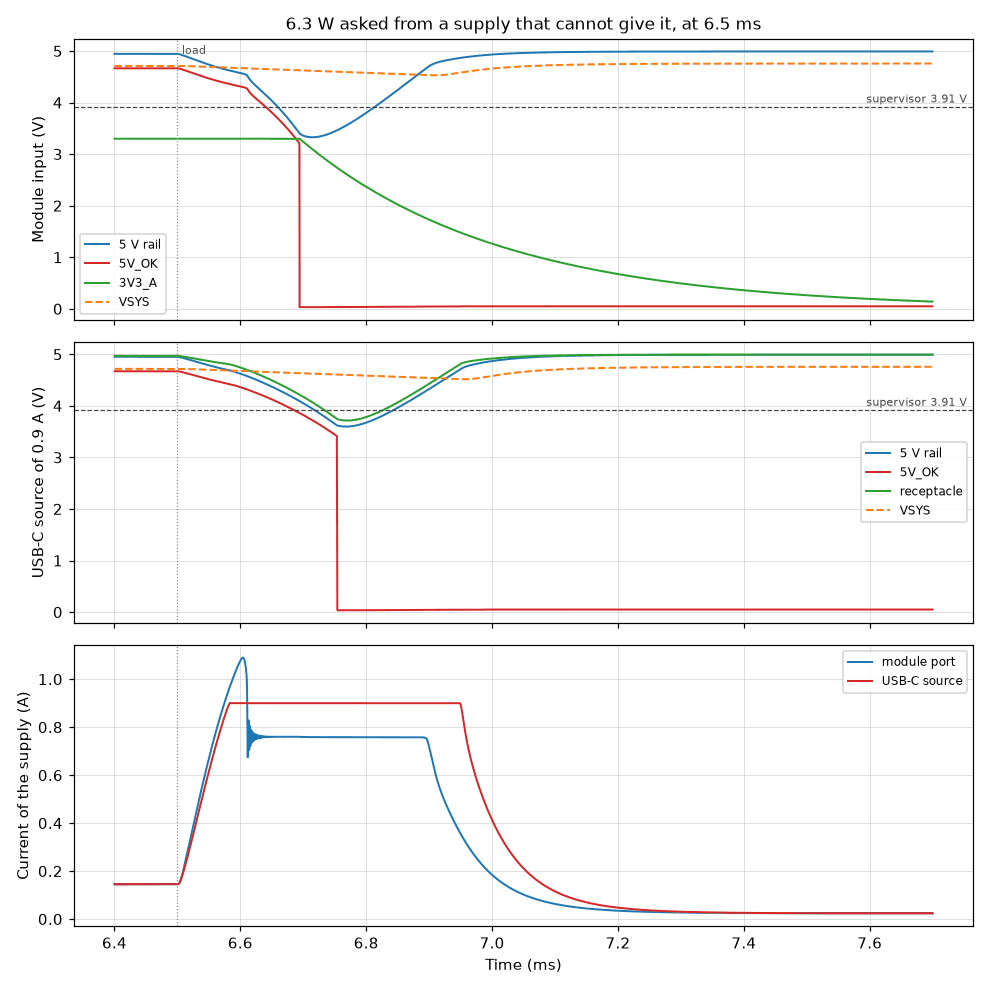
simulation/results/power_input/overload.shed.png
