Guiimartinho/esp32-s3-power-profiler/simulation/results/power_input/overvoltage.reverse.png

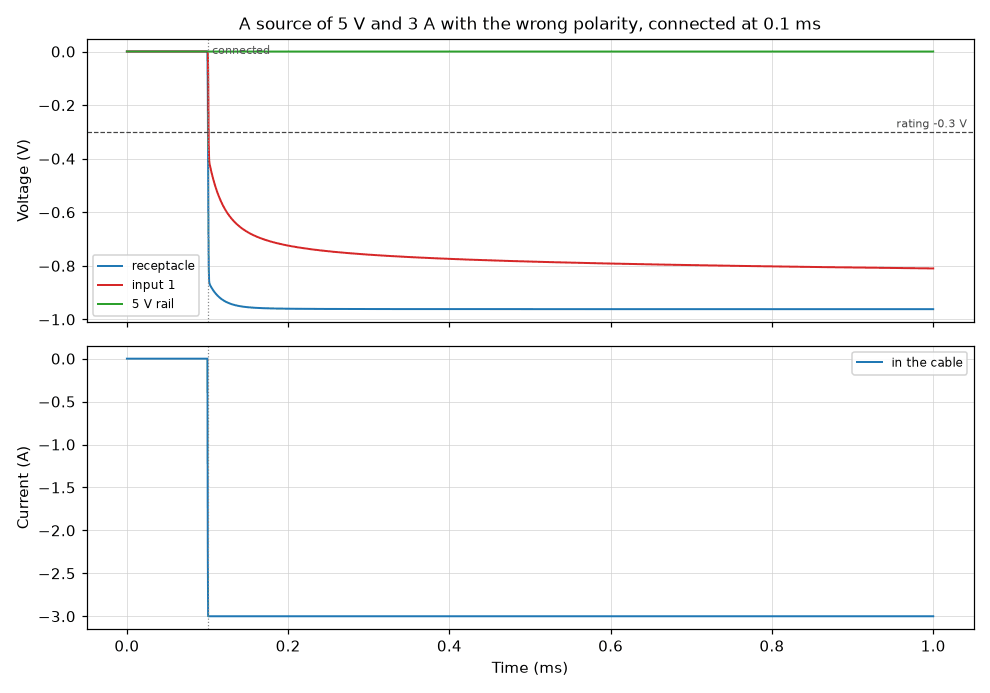
simulation/results/power_input/overvoltage.reverse.png
