Guiimartinho/esp32-s3-power-profiler/simulation/results/power_input/overvoltage.rise.png

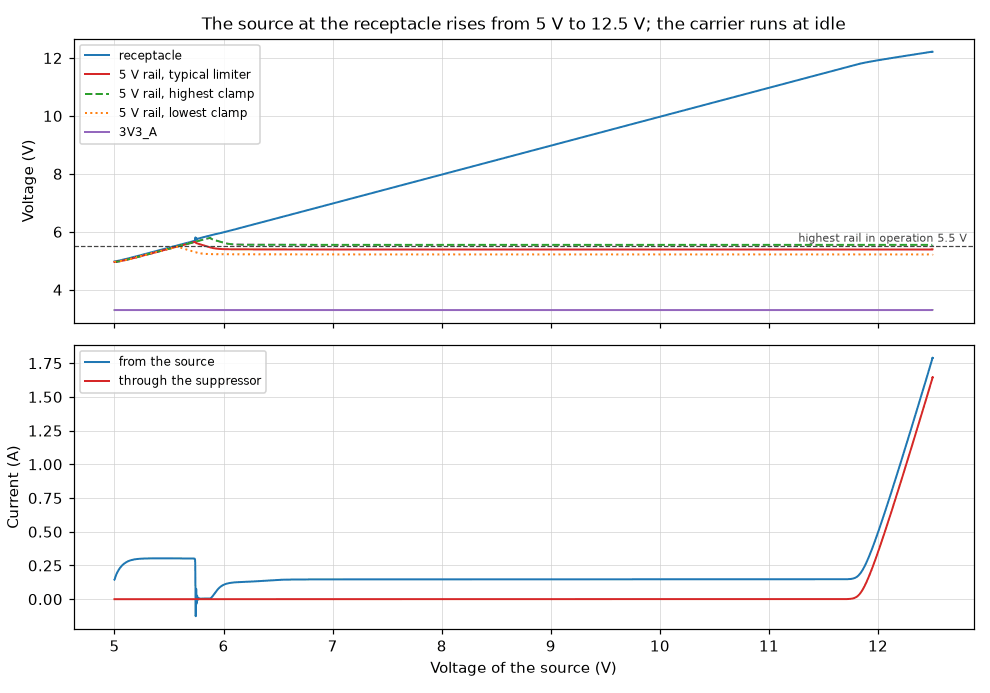
simulation/results/power_input/overvoltage.rise.png
