Guiimartinho/esp32-s3-power-profiler/simulation/results/power_input/path-drop.levels.png

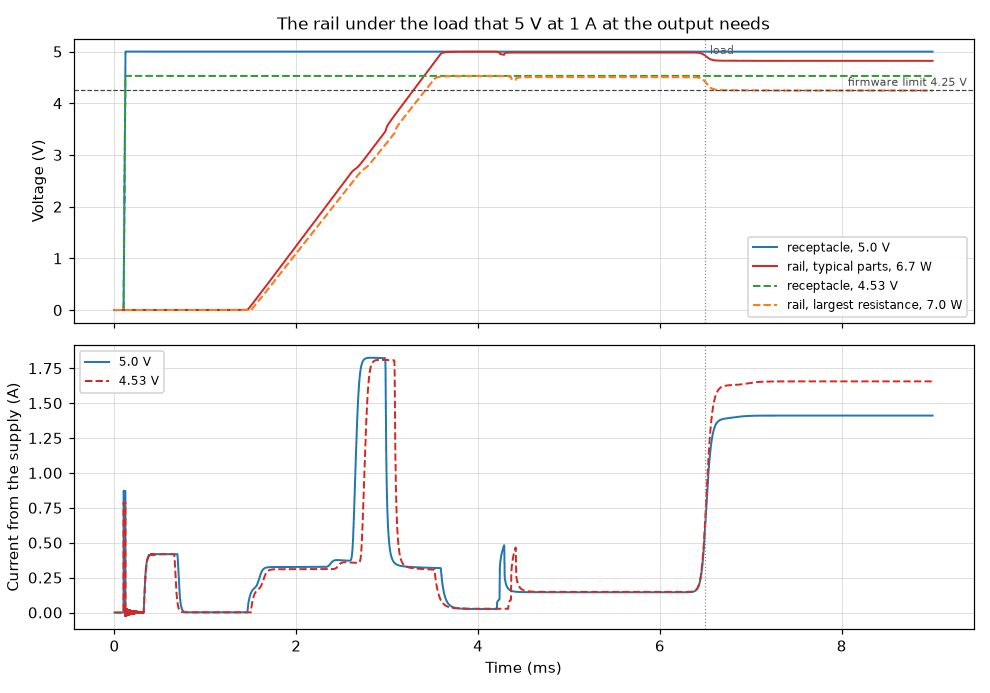
simulation/results/power_input/path-drop.levels.png
