Guiimartinho/esp32-s3-power-profiler/simulation/results/power_input/plug-module.start.png

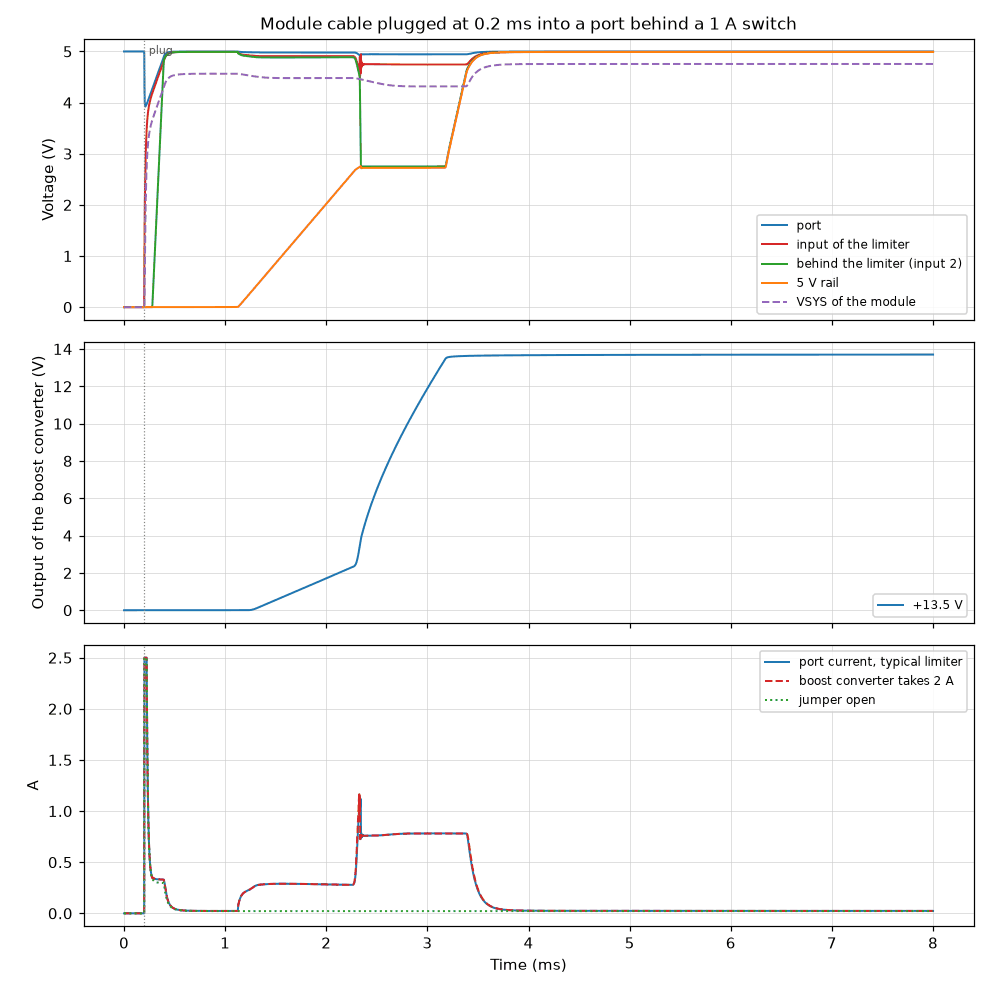
simulation/results/power_input/plug-module.start.png
