Guiimartinho/esp32-s3-power-profiler/simulation/results/power_input/plug-usbc.weak.png

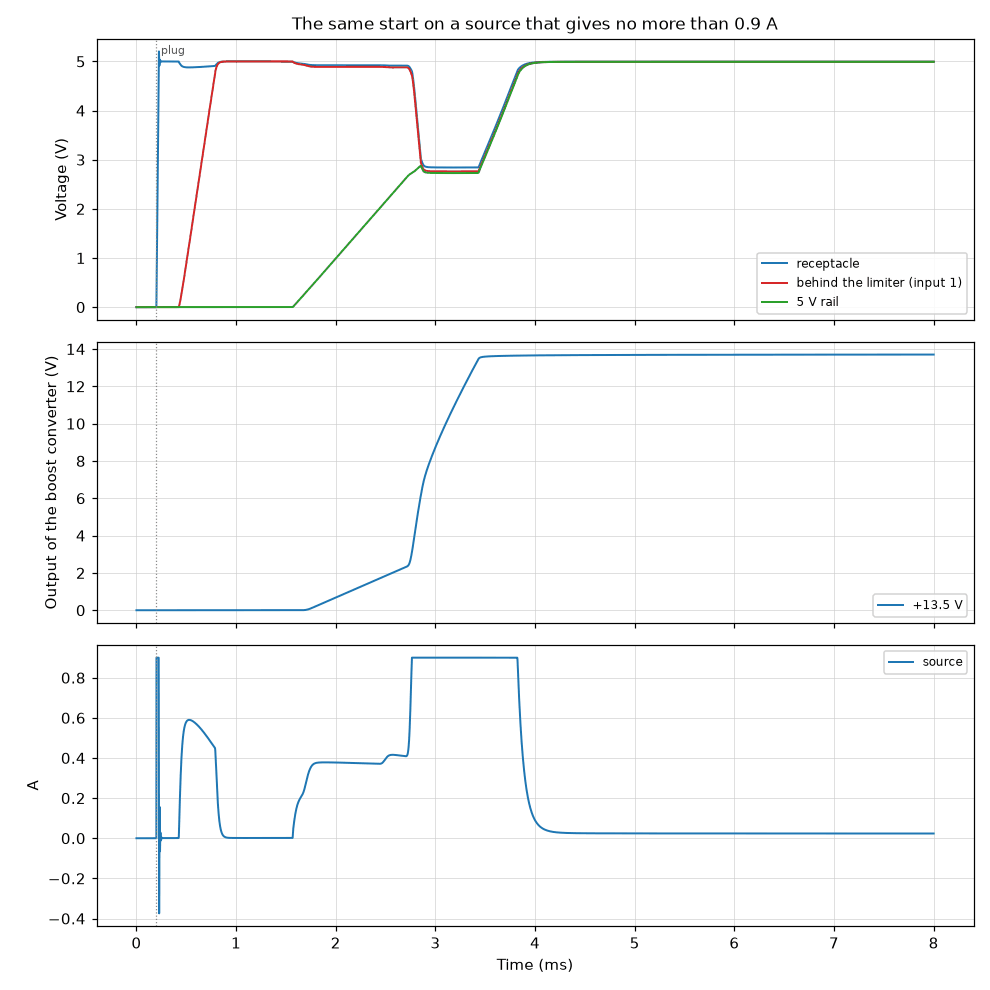
simulation/results/power_input/plug-usbc.weak.png
