Guiimartinho/esp32-s3-power-profiler/simulation/results/power_input/replug-module.close.png

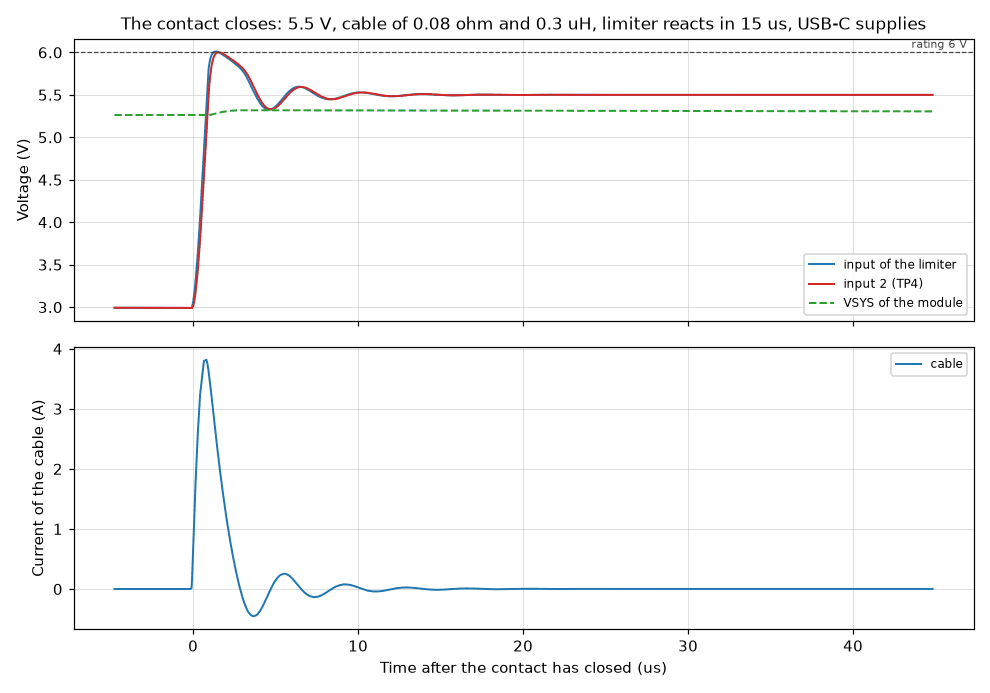
simulation/results/power_input/replug-module.close.png
