Guiimartinho/esp32-s3-power-profiler/simulation/results/power_input/switch-over.change.png

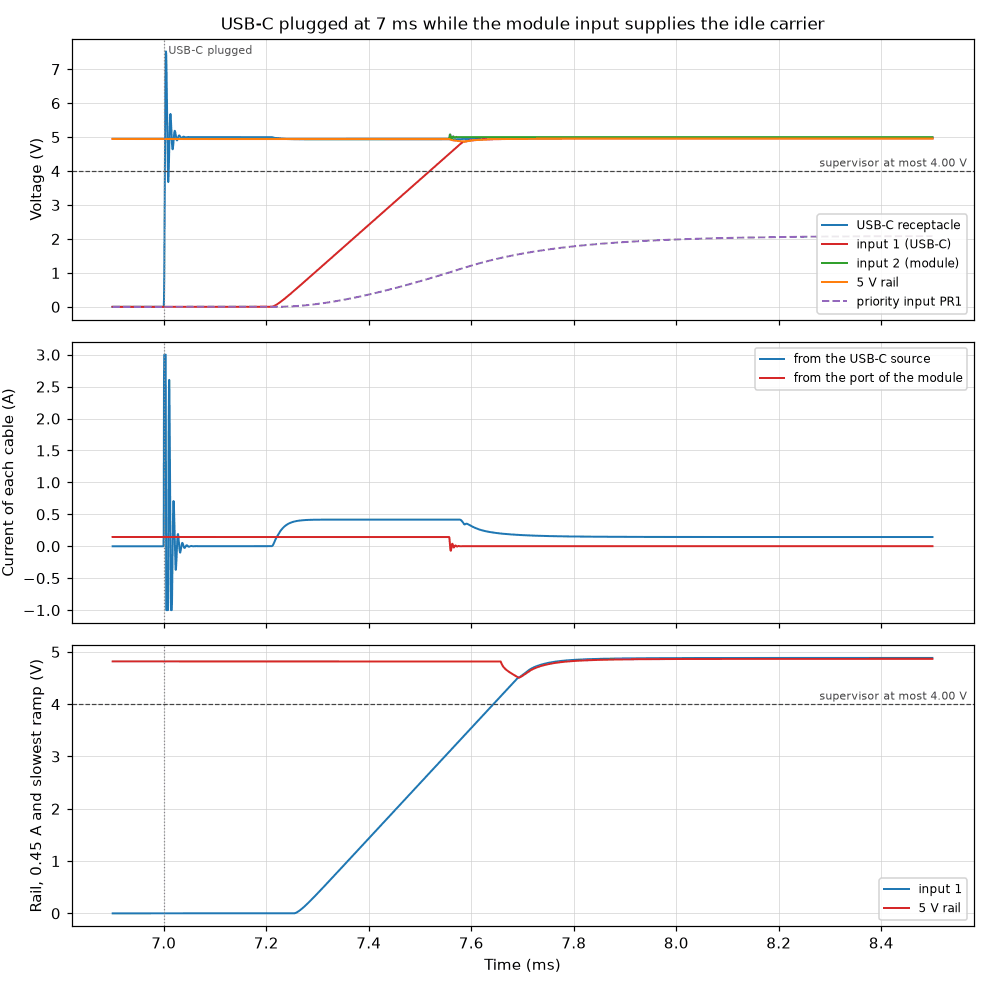
simulation/results/power_input/switch-over.change.png
