Guiimartinho/esp32-s3-power-profiler/simulation/results/power_input/thresholds.cc.png

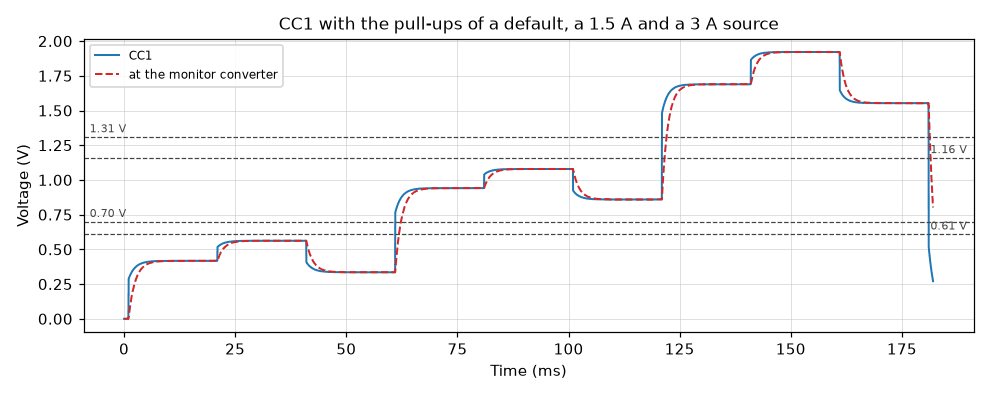
simulation/results/power_input/thresholds.cc.png
