Guiimartinho/esp32-s3-power-profiler/simulation/results/power_input/unplug.decay.png

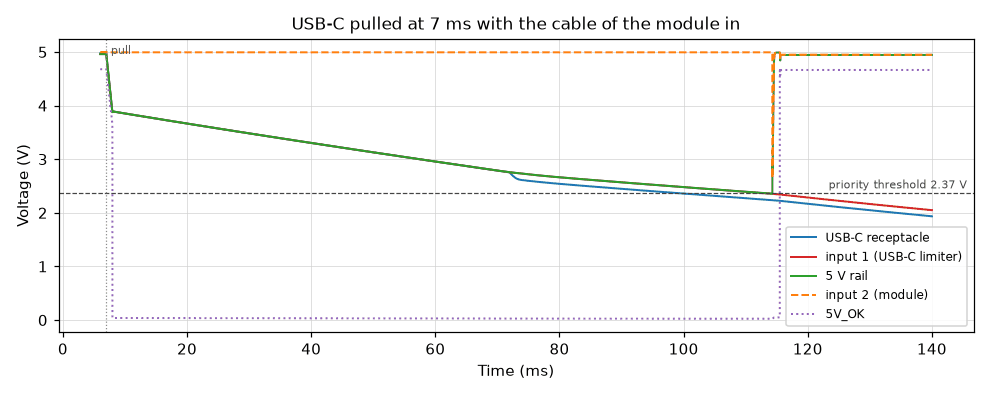
simulation/results/power_input/unplug.decay.png
