Guiimartinho/esp32-s3-power-profiler/simulation/results/range_logic/hot-plug.plug.png

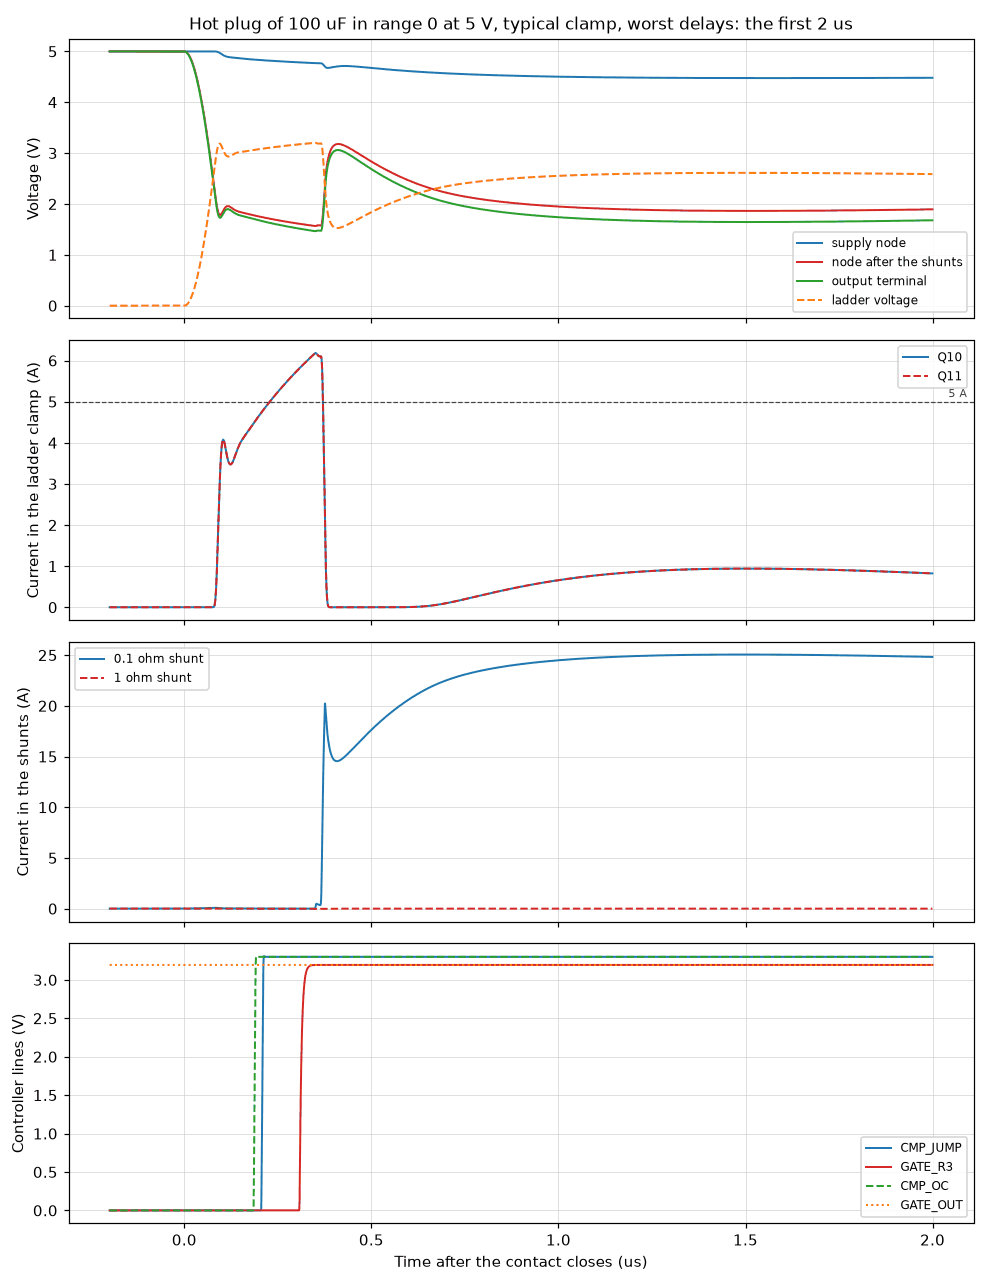
simulation/results/range_logic/hot-plug.plug.png
