Guiimartinho/esp32-s3-power-profiler/simulation/results/range_logic/hot-plug.short.png

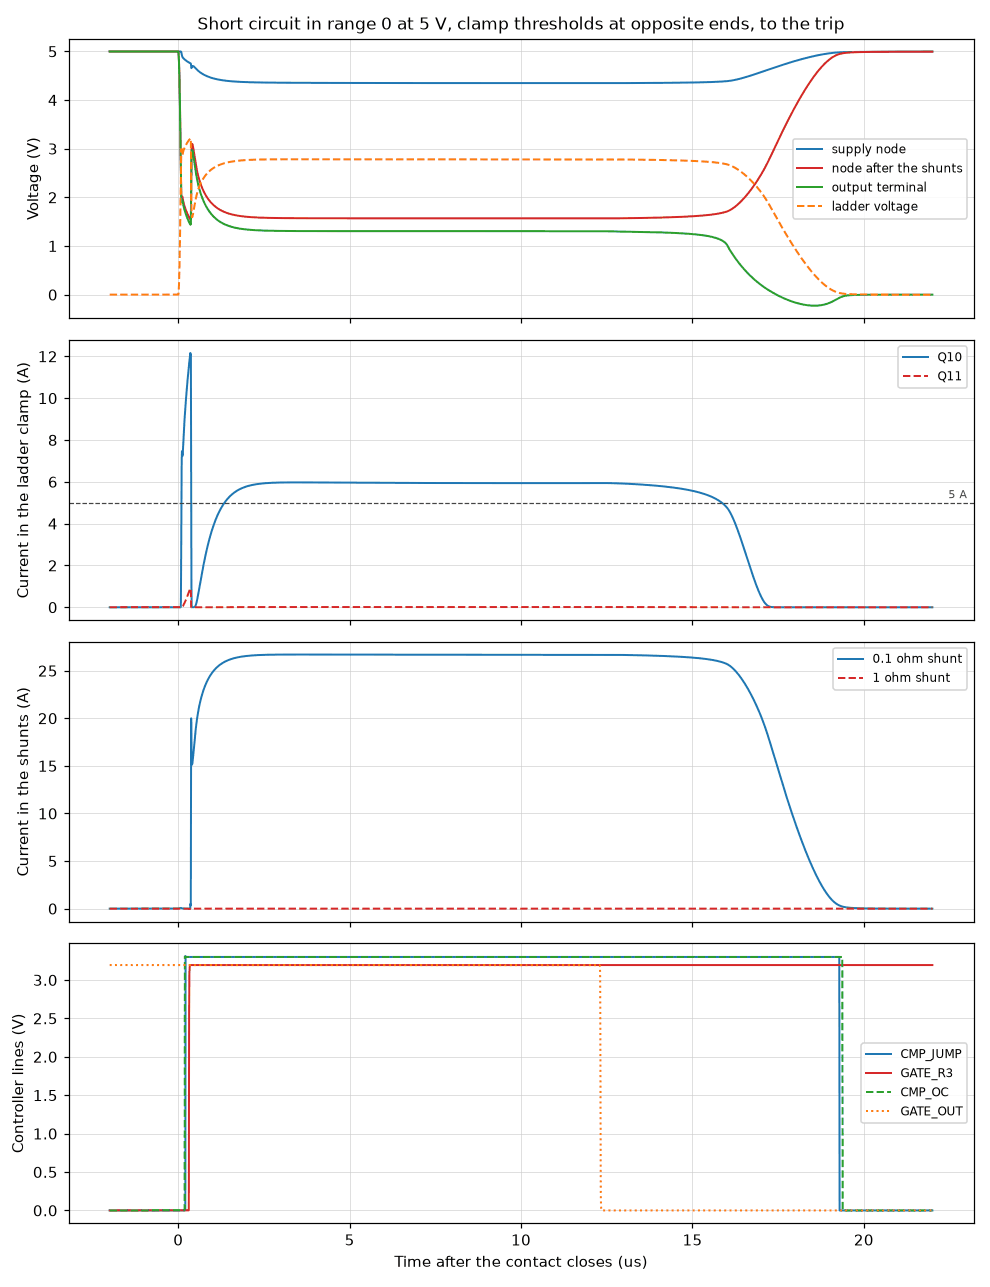
simulation/results/range_logic/hot-plug.short.png
