Guiimartinho/esp32-s3-power-profiler/simulation/results/range_logic/input-clamp.transfer.png

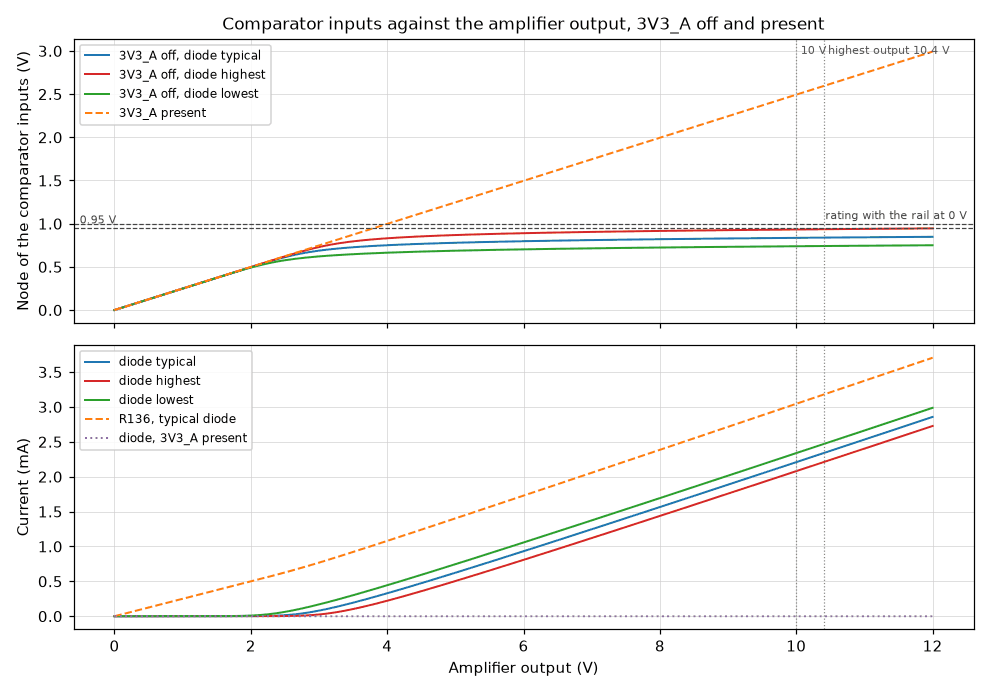
simulation/results/range_logic/input-clamp.transfer.png
