Guiimartinho/esp32-s3-power-profiler/simulation/results/range_logic/jump.delays.png

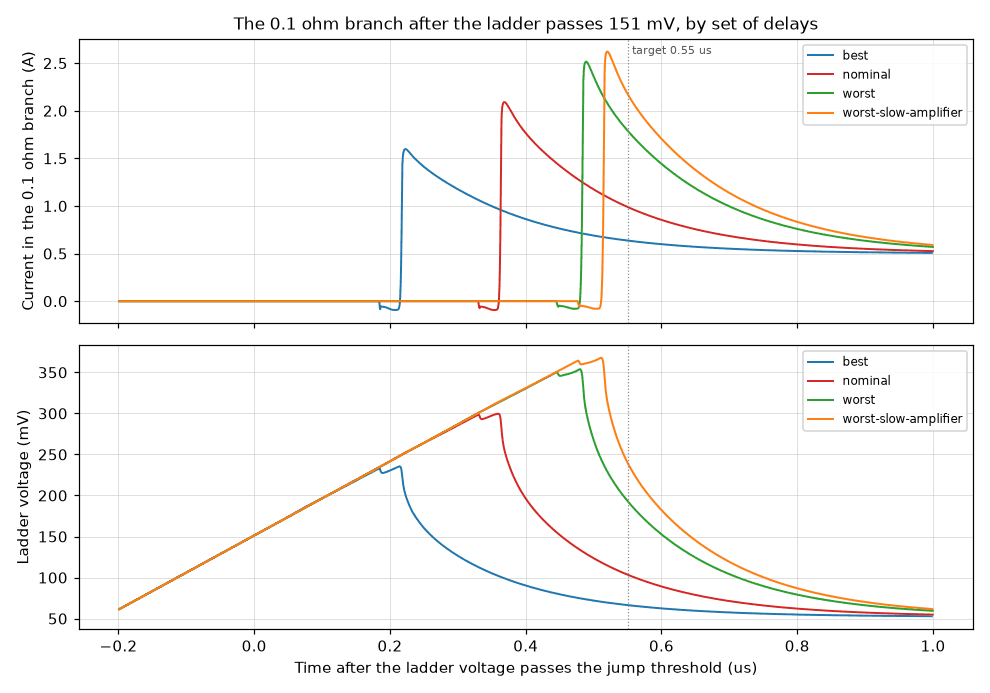
simulation/results/range_logic/jump.delays.png
