Guiimartinho/esp32-s3-power-profiler/simulation/results/range_logic/jump.waveforms.png

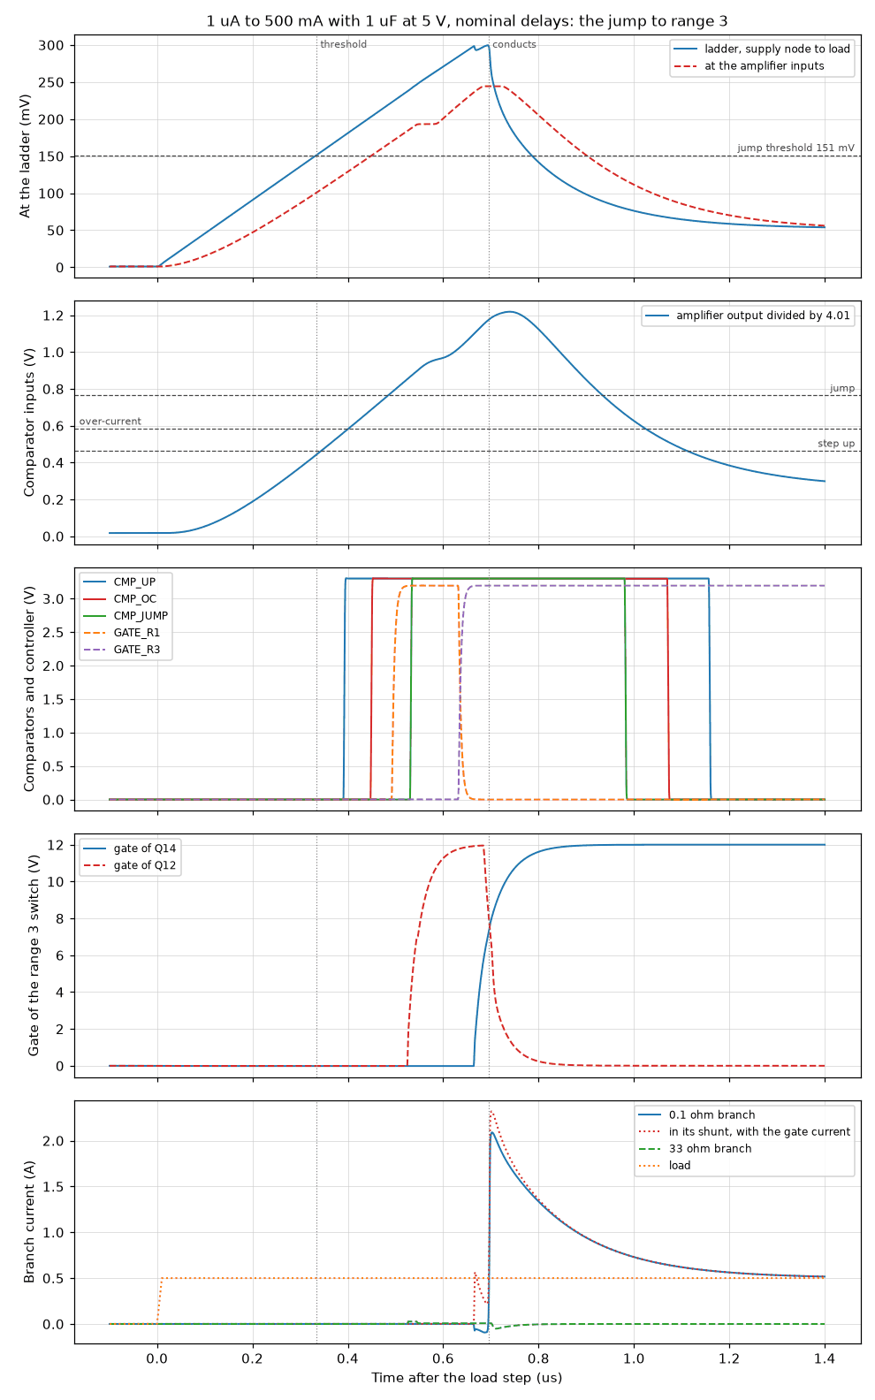
simulation/results/range_logic/jump.waveforms.png
