Guiimartinho/esp32-s3-power-profiler/simulation/results/range_logic/landing.climb.png

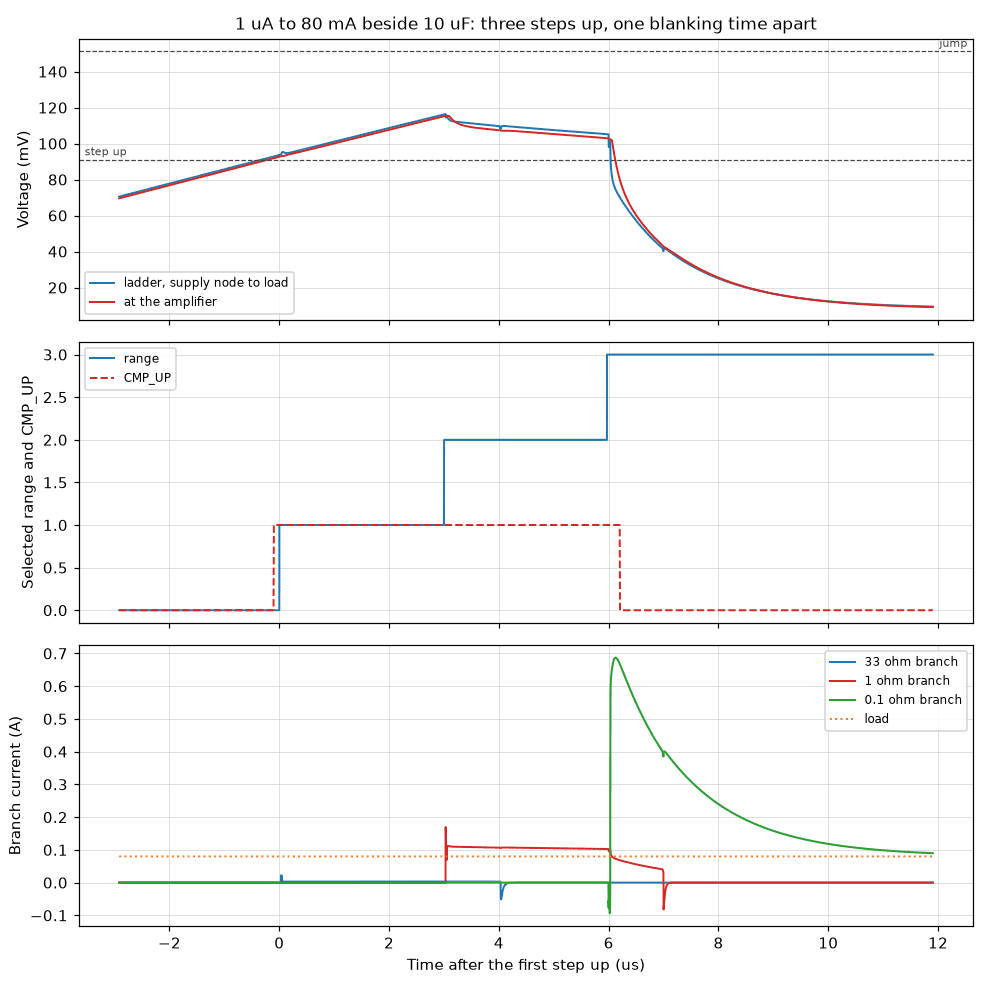
simulation/results/range_logic/landing.climb.png
