Guiimartinho/esp32-s3-power-profiler/simulation/results/range_logic/landing.ranges.png

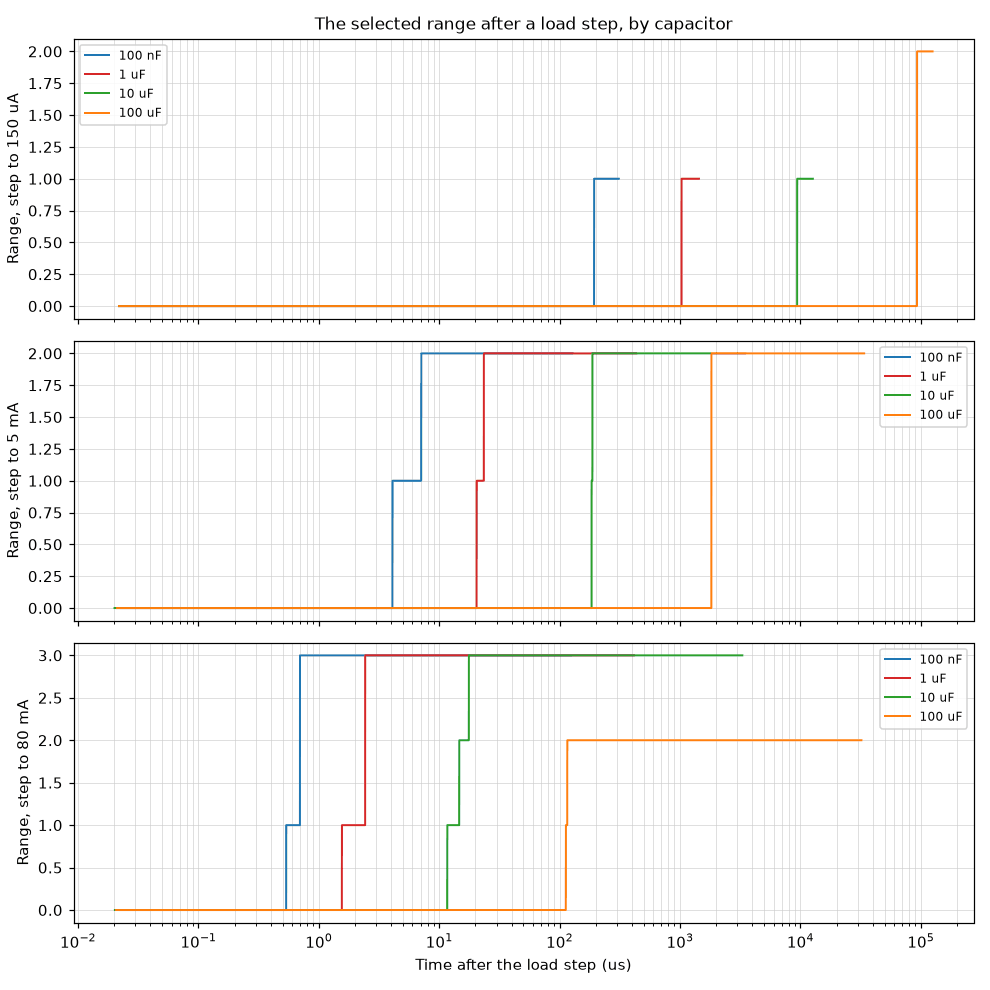
simulation/results/range_logic/landing.ranges.png
