Guiimartinho/esp32-s3-power-profiler/simulation/results/range_logic/power-on.start.png

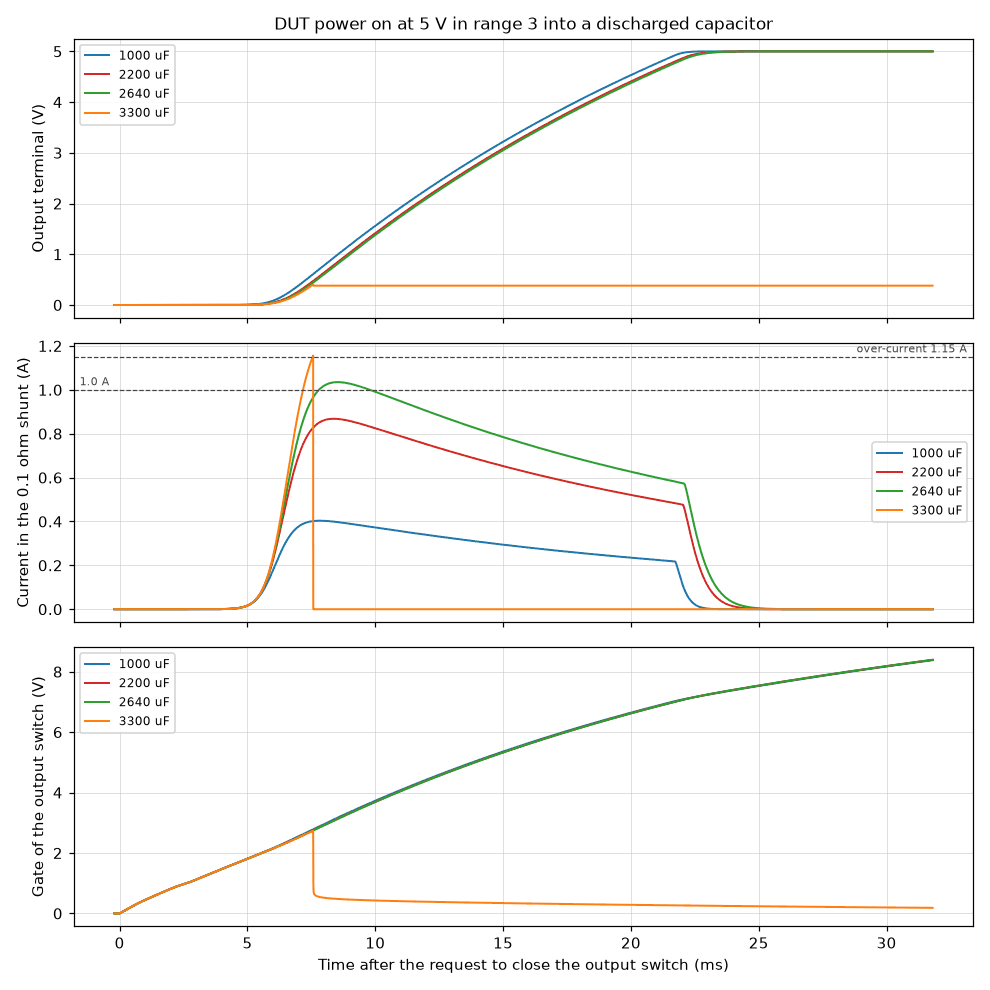
simulation/results/range_logic/power-on.start.png
