Guiimartinho/esp32-s3-power-profiler/simulation/results/range_logic/ramp.staircase-1uf.png

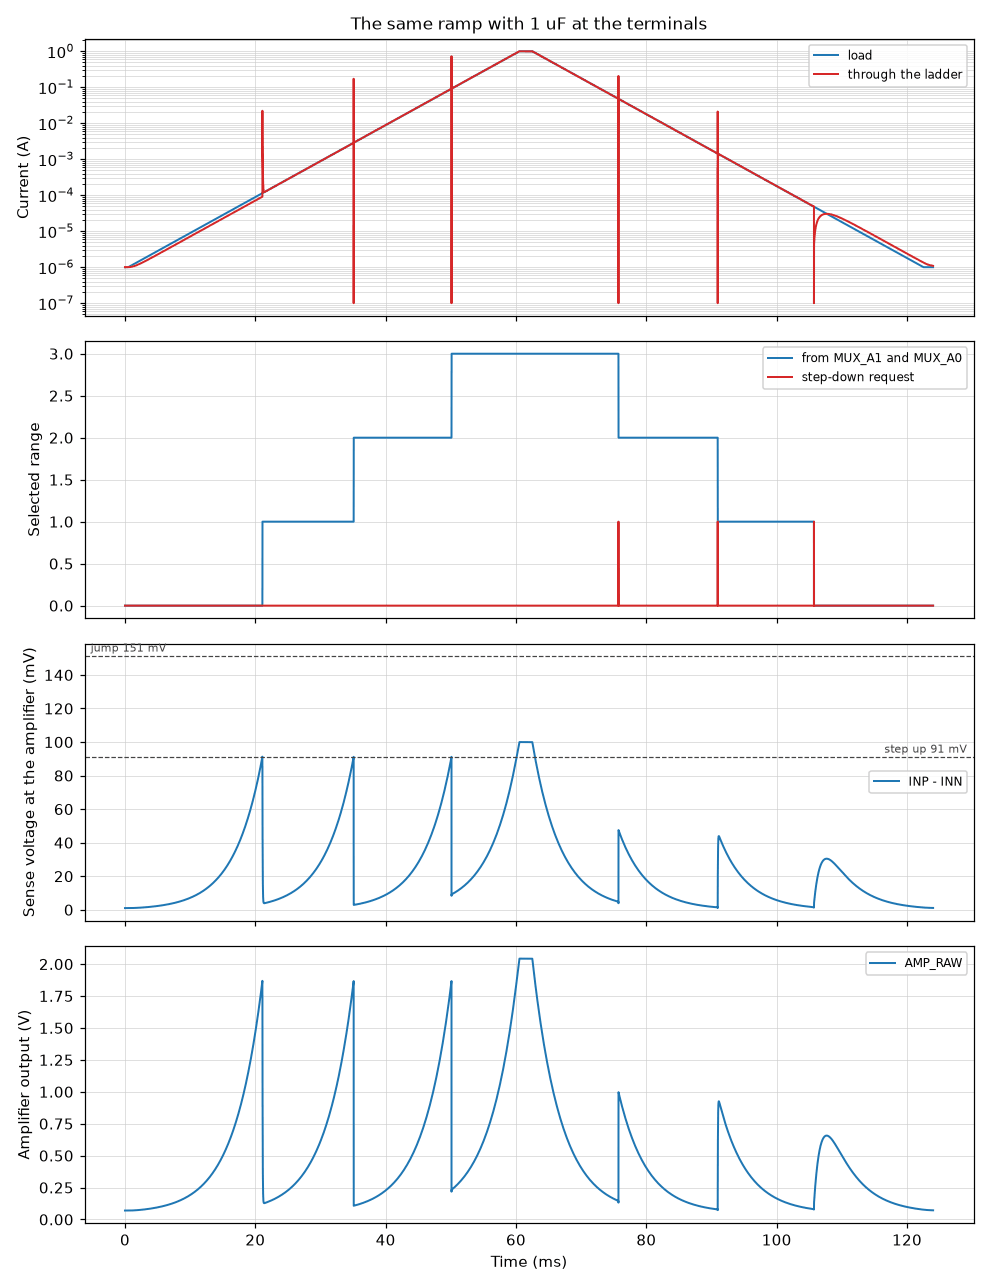
simulation/results/range_logic/ramp.staircase-1uf.png
