Guiimartinho/esp32-s3-power-profiler/simulation/results/range_logic/ramp.staircase.png

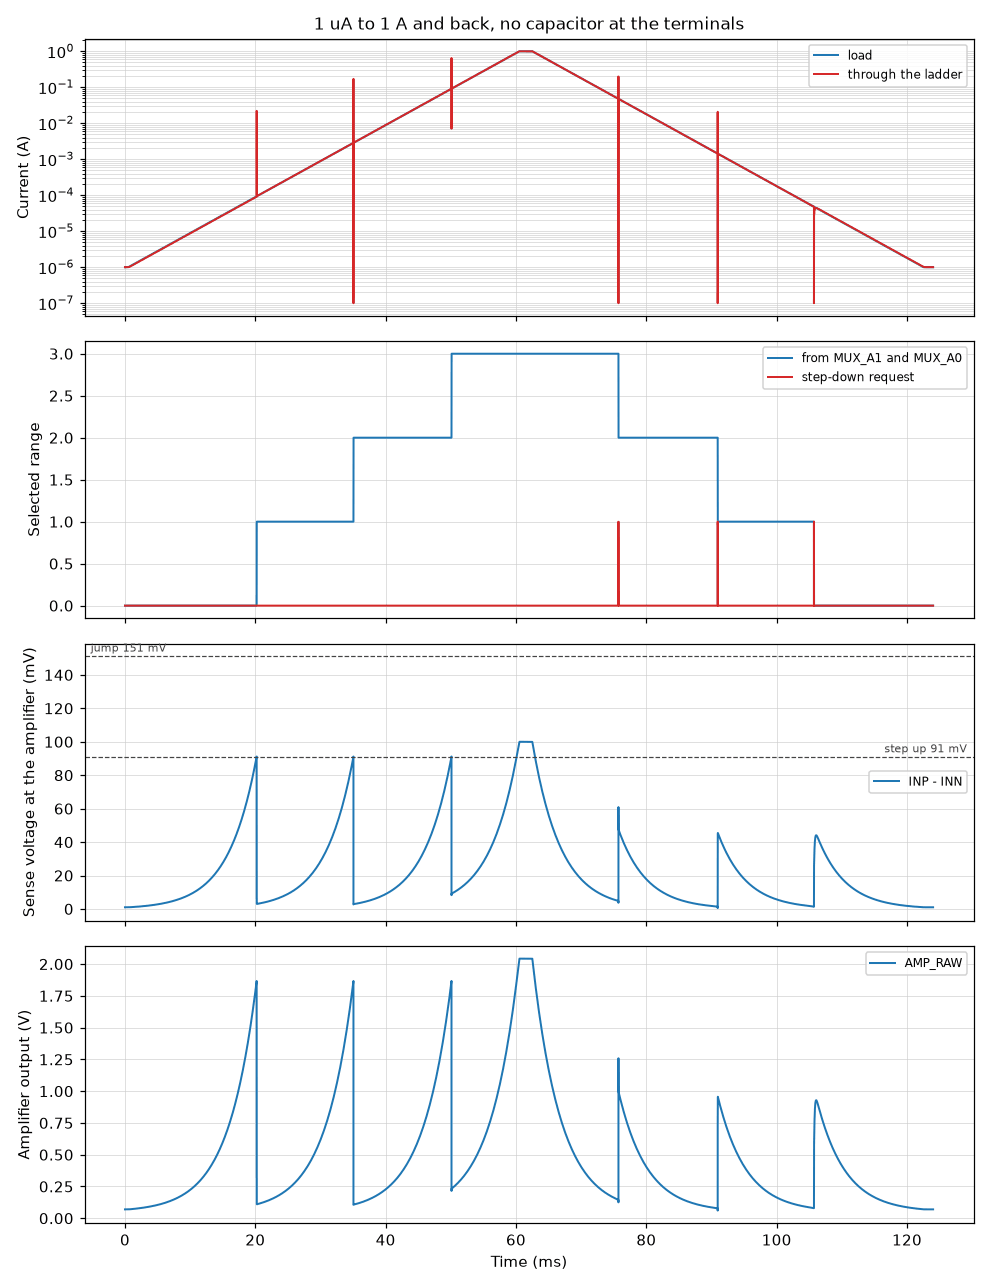
simulation/results/range_logic/ramp.staircase.png
