Guiimartinho/esp32-s3-power-profiler/simulation/results/range_logic/reverse.reverse.png

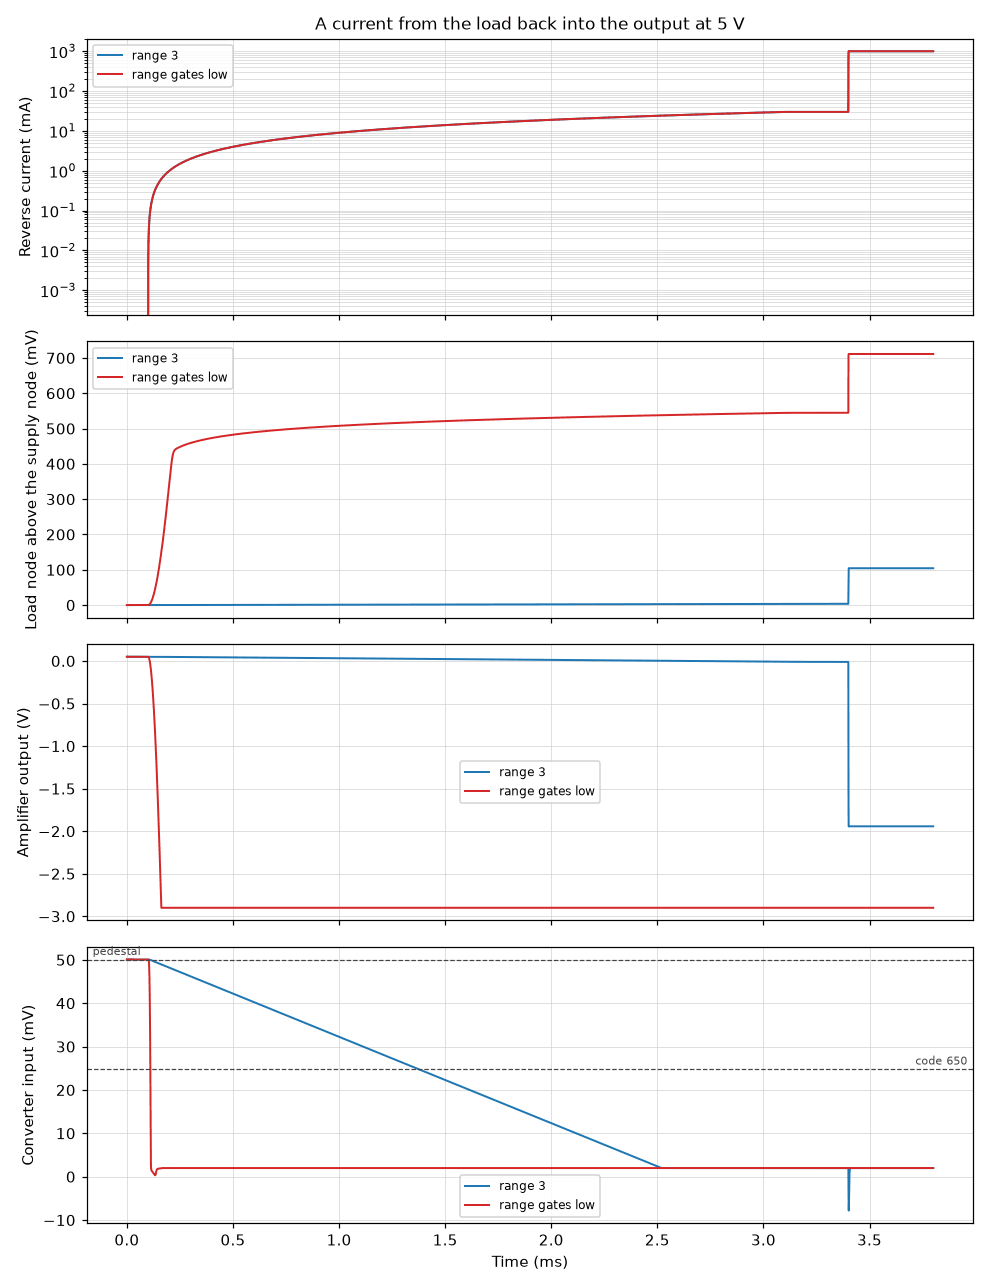
simulation/results/range_logic/reverse.reverse.png
