Guiimartinho/esp32-s3-power-profiler/simulation/results/range_logic/supply-leads.sag.png

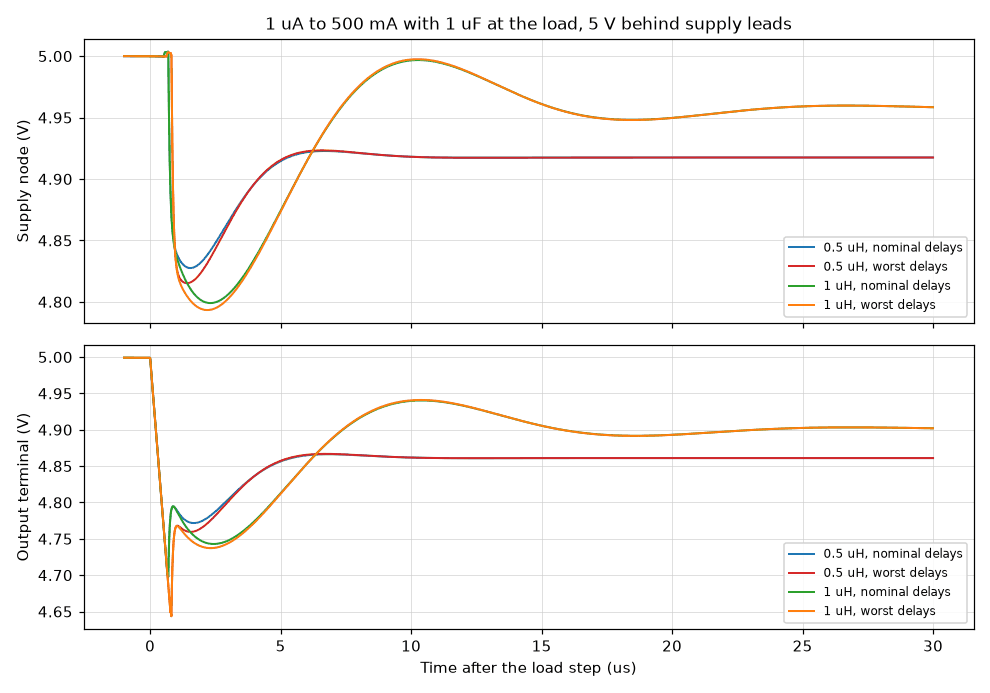
simulation/results/range_logic/supply-leads.sag.png
