Guiimartinho/esp32-s3-power-profiler/simulation/results/range_logic/thresholds.ramp.png

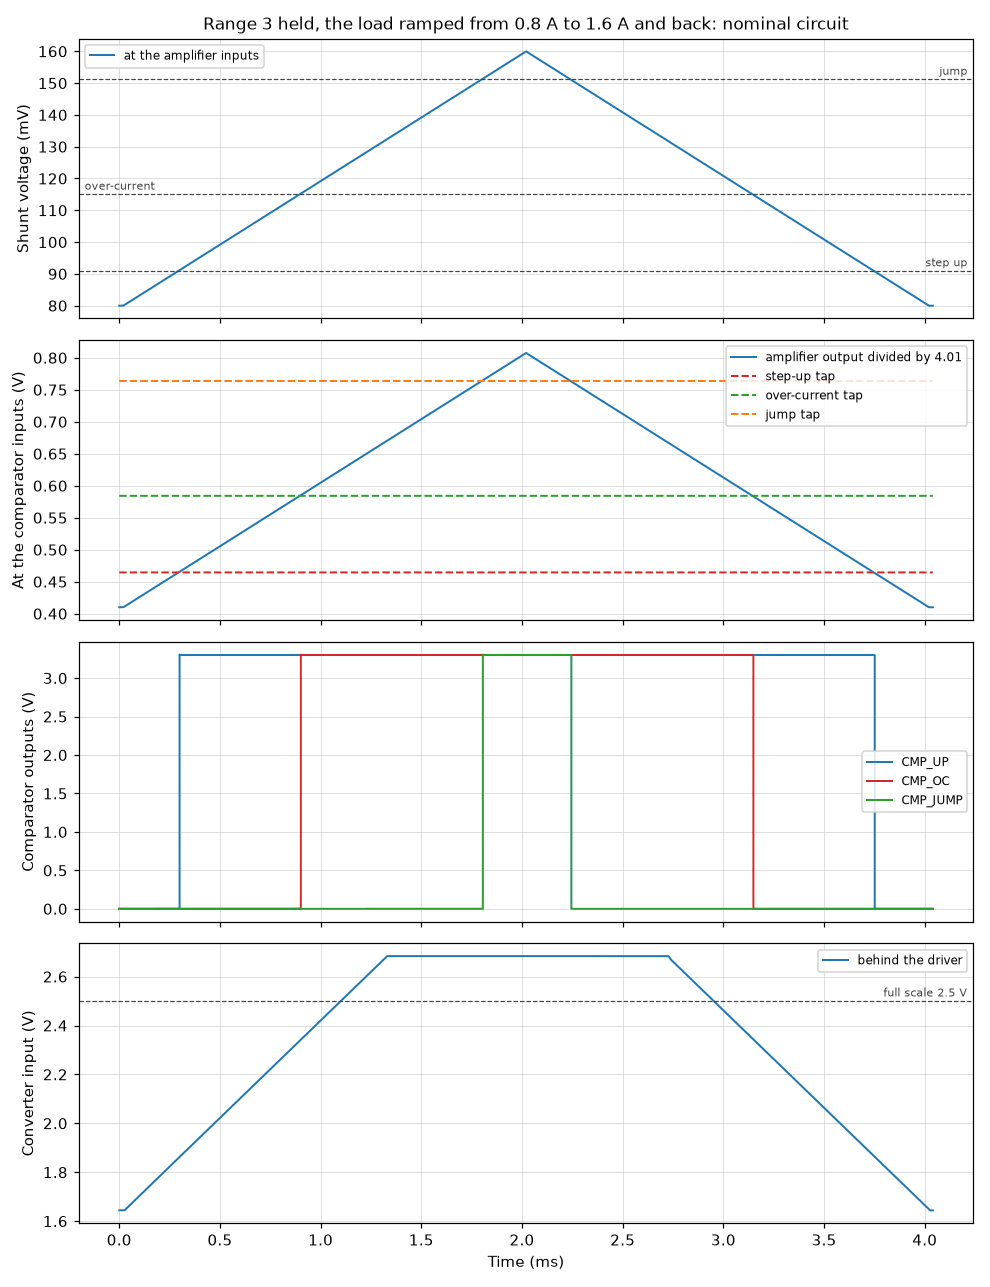
simulation/results/range_logic/thresholds.ramp.png
