Guiimartinho/esp32-s3-power-profiler/simulation/results/range_logic/trip.recharge.png

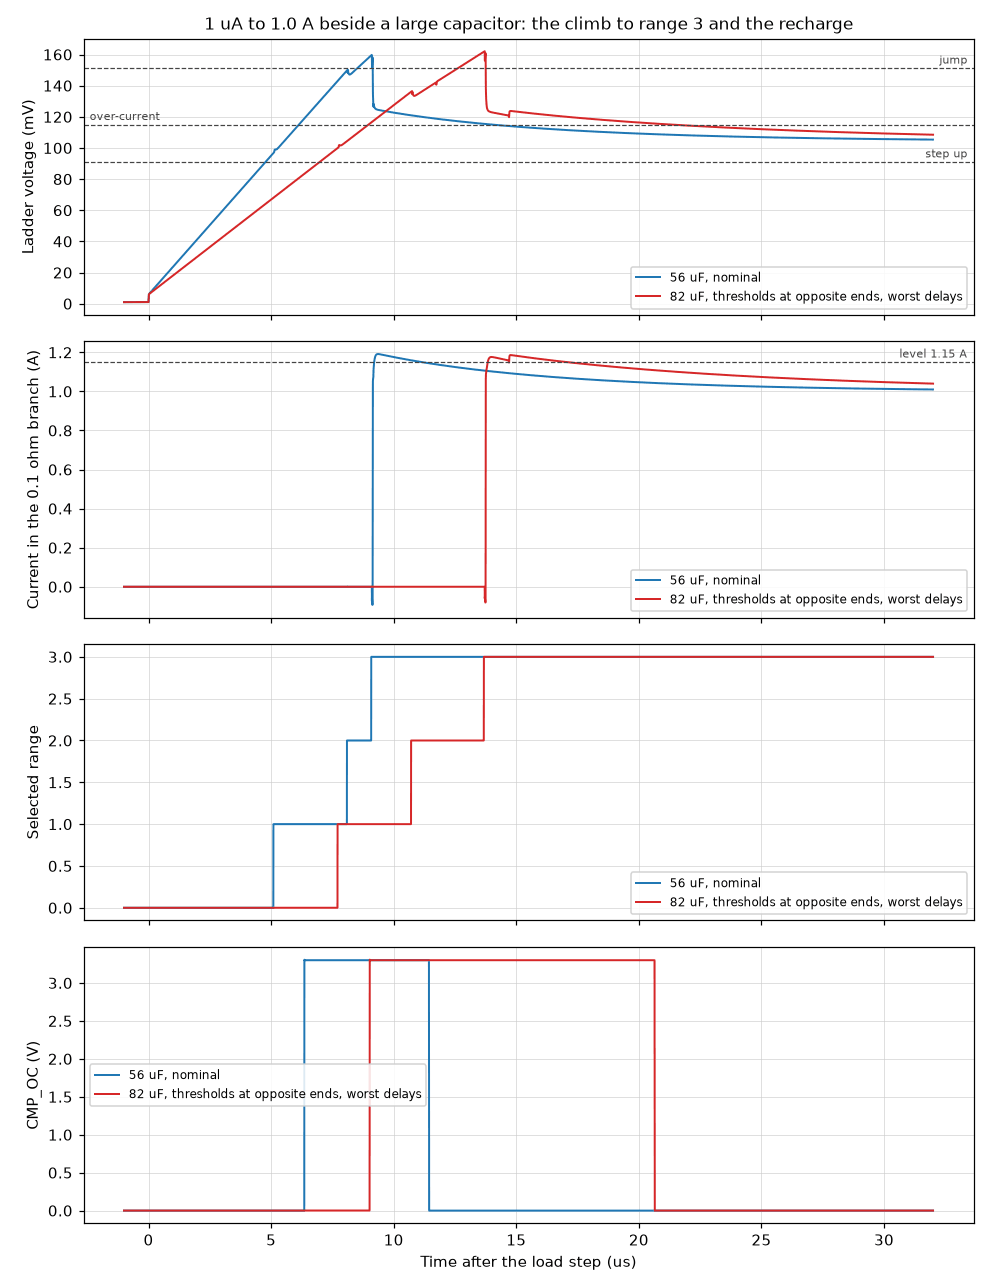
simulation/results/range_logic/trip.recharge.png
