Guiimartinho/esp32-s3-power-profiler/simulation/results/range_logic/trip.sweep.png

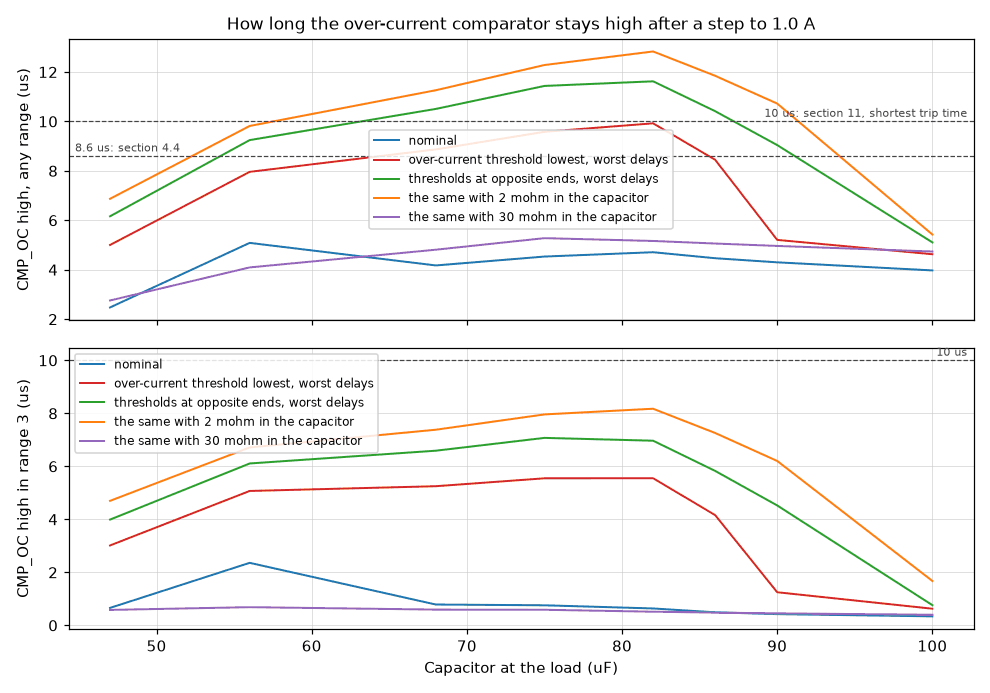
simulation/results/range_logic/trip.sweep.png
