Guiimartinho/esp32-s3-power-profiler/simulation/results/range_logic/trip.trip.png

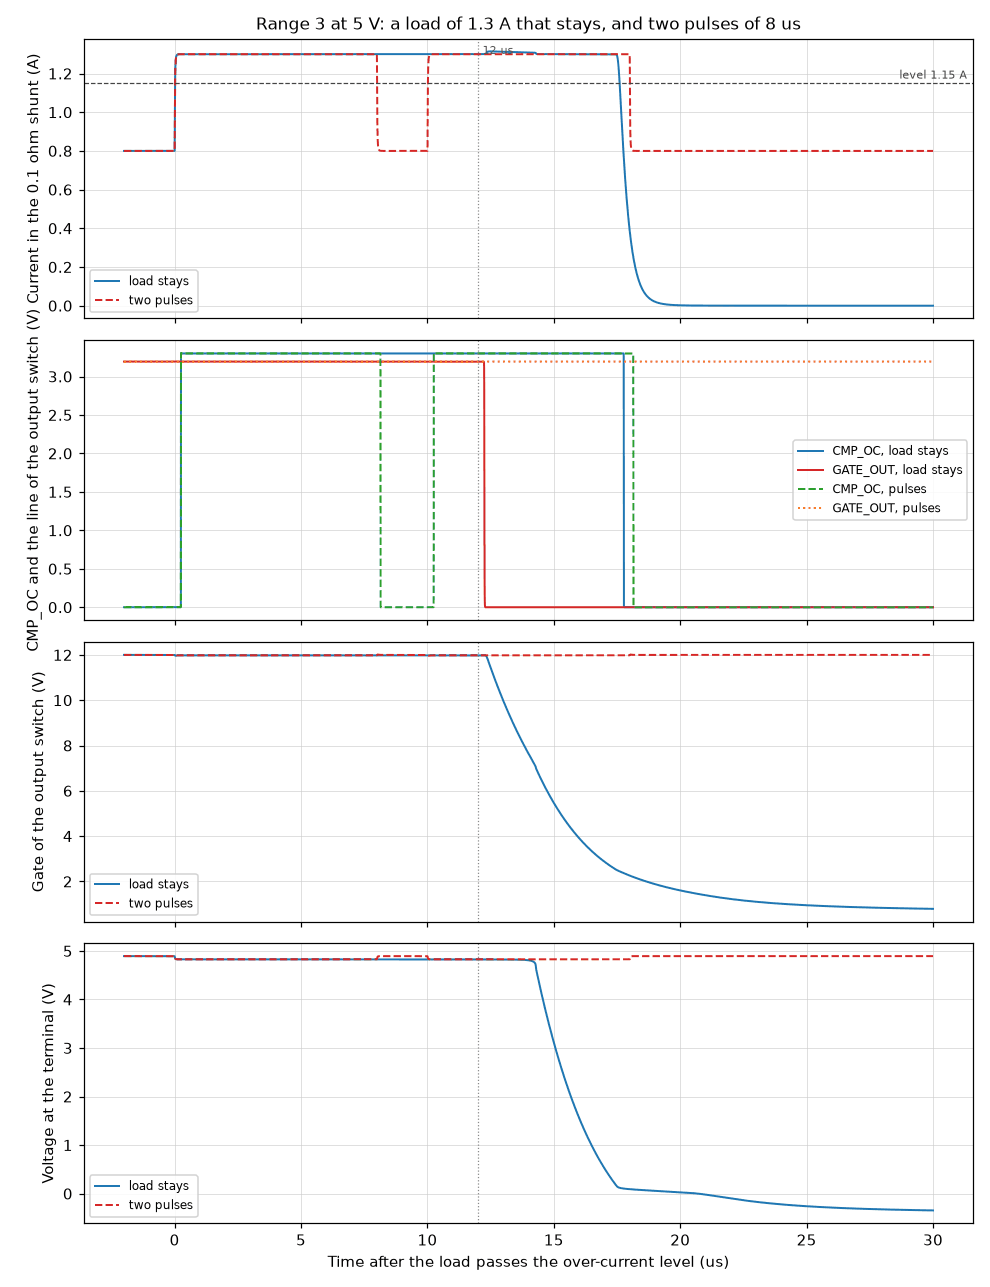
simulation/results/range_logic/trip.trip.png
