Guiimartinho/esp32-s3-power-profiler/simulation/results/signal_chain/common-mode.rejection.png

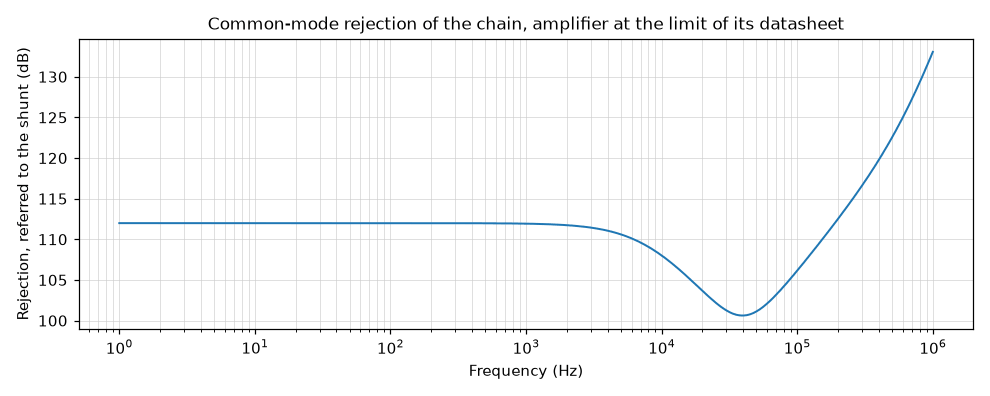
simulation/results/signal_chain/common-mode.rejection.png
