Guiimartinho/esp32-s3-power-profiler/simulation/results/signal_chain/driver-rail.loop.png

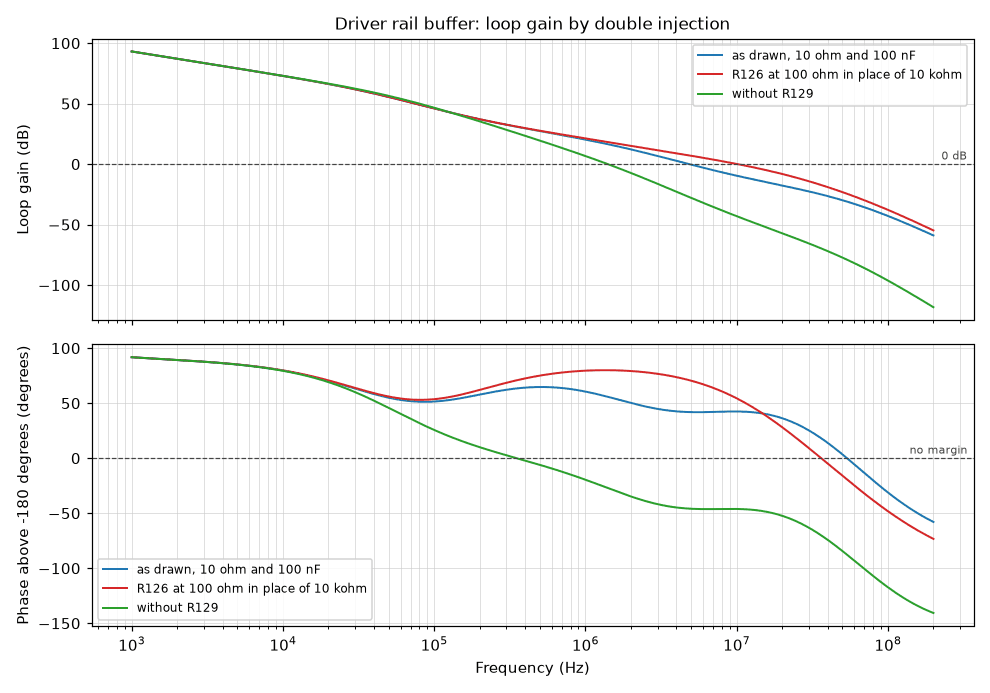
simulation/results/signal_chain/driver-rail.loop.png
