Guiimartinho/esp32-s3-power-profiler/simulation/results/signal_chain/frequency.response.png

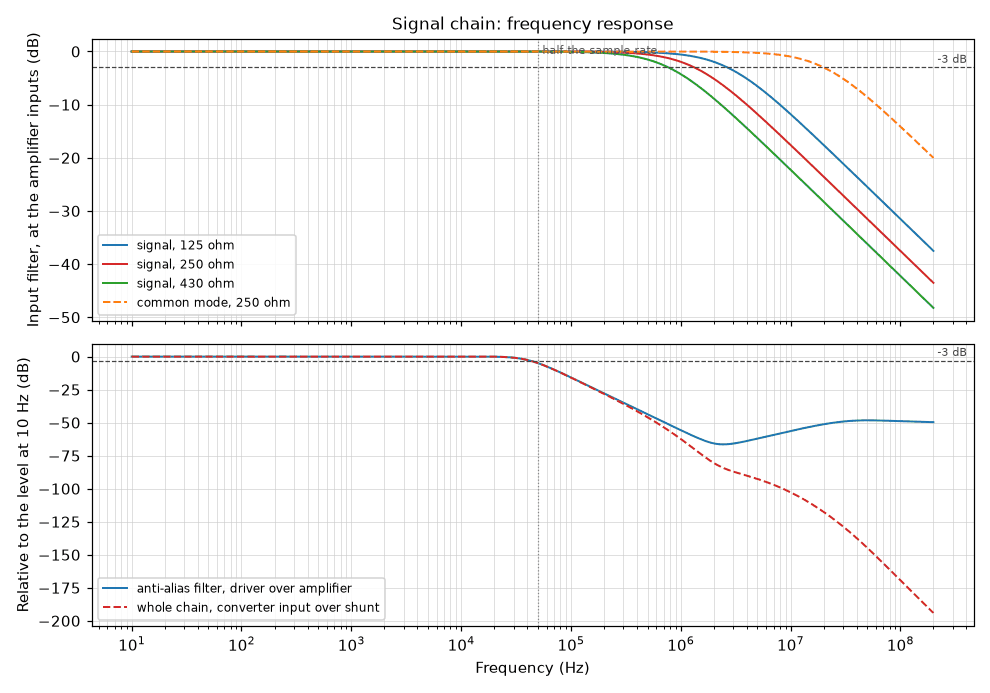
simulation/results/signal_chain/frequency.response.png
