Guiimartinho/esp32-s3-power-profiler/simulation/results/signal_chain/head-room.transfer.png

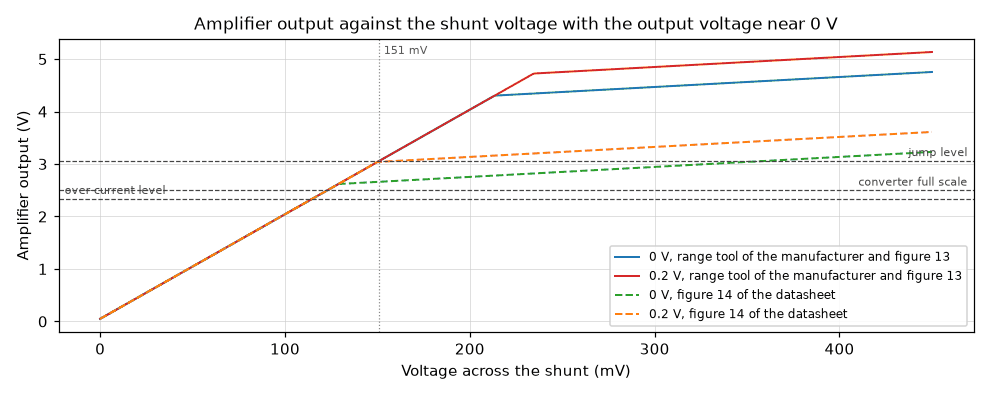
simulation/results/signal_chain/head-room.transfer.png
