Guiimartinho/esp32-s3-power-profiler/simulation/results/signal_chain/limiter.waveforms.png

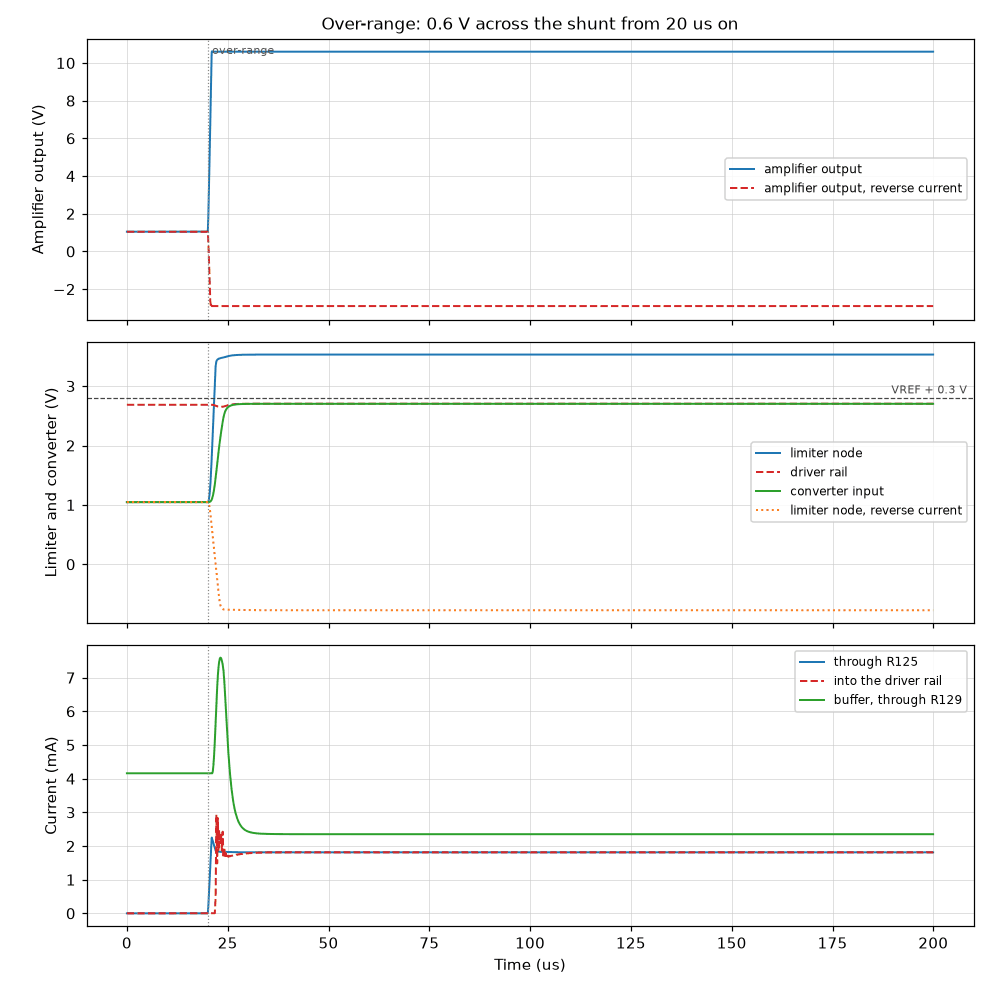
simulation/results/signal_chain/limiter.waveforms.png
