Guiimartinho/esp32-s3-power-profiler/simulation/results/signal_chain/noise.density.png

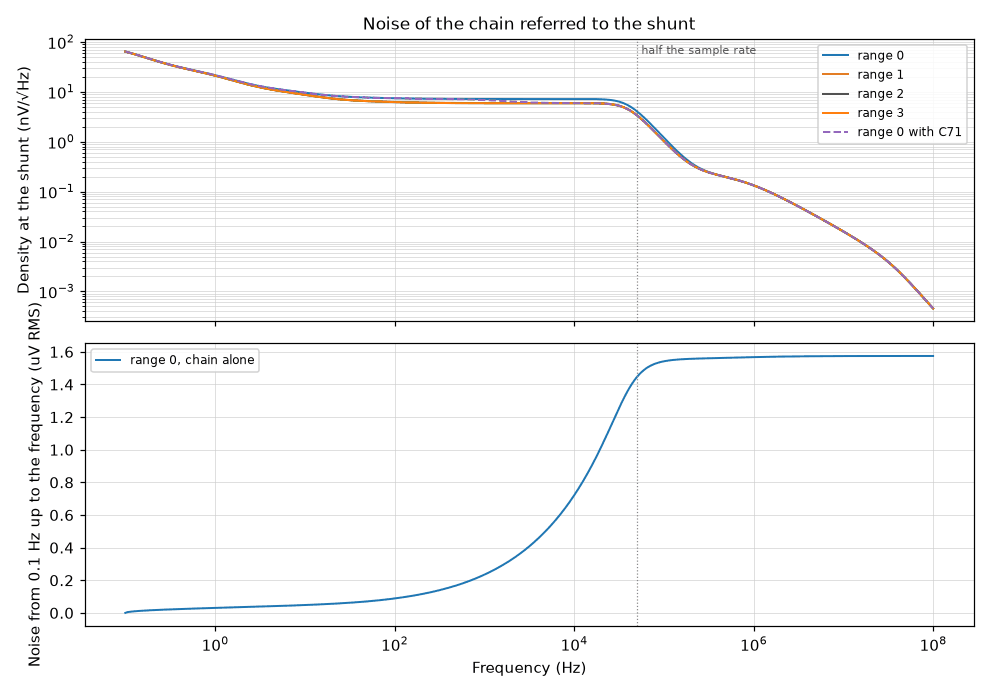
simulation/results/signal_chain/noise.density.png
