Guiimartinho/esp32-s3-power-profiler/simulation/results/signal_chain/pedestal.power-up.png

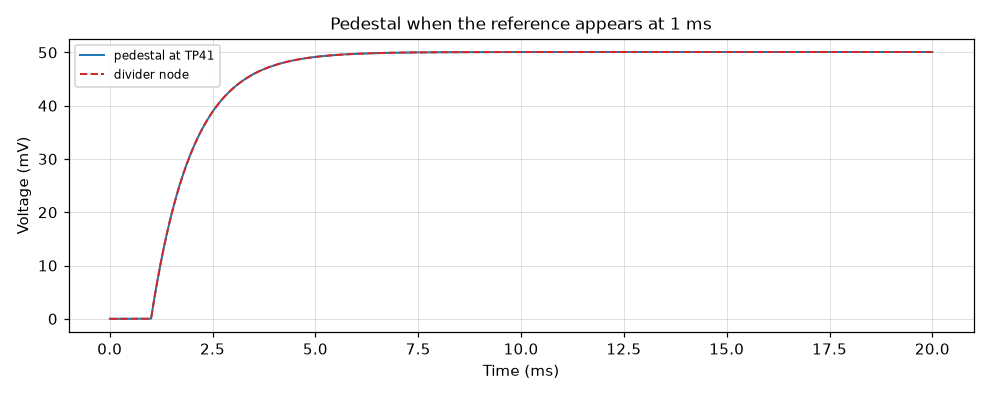
simulation/results/signal_chain/pedestal.power-up.png
