Guiimartinho/esp32-s3-power-profiler/simulation/results/signal_chain/pedestal.response.png

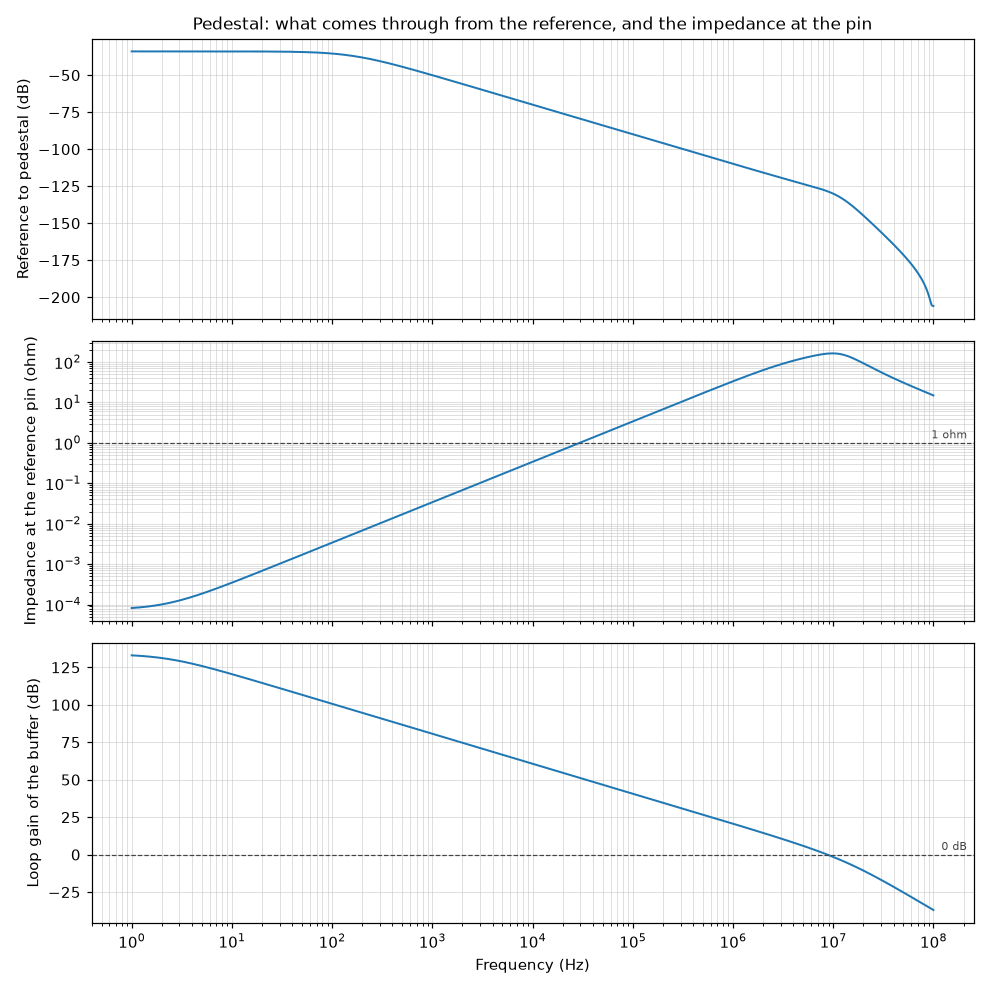
simulation/results/signal_chain/pedestal.response.png
