Guiimartinho/esp32-s3-power-profiler/simulation/results/signal_chain/reference-line.line.png

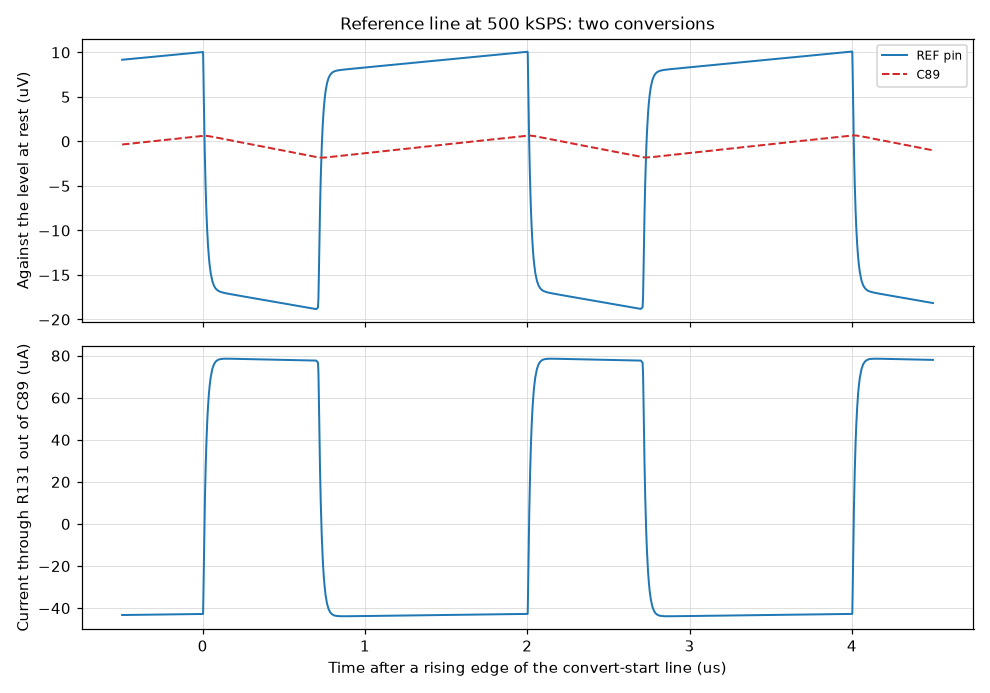
simulation/results/signal_chain/reference-line.line.png
