Guiimartinho/esp32-s3-power-profiler/simulation/results/signal_chain/sampling-kick.kick.png

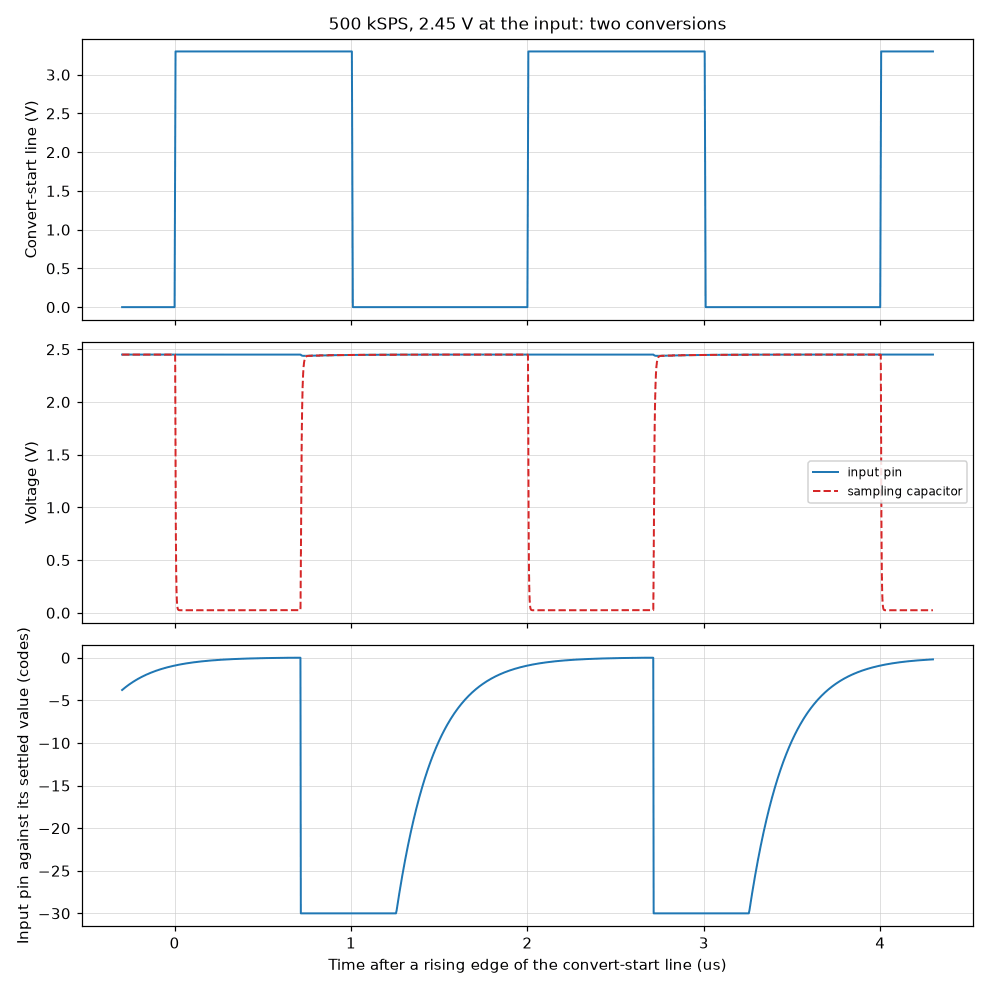
simulation/results/signal_chain/sampling-kick.kick.png
