Guiimartinho/esp32-s3-power-profiler/simulation/results/signal_chain/settling.errors.png

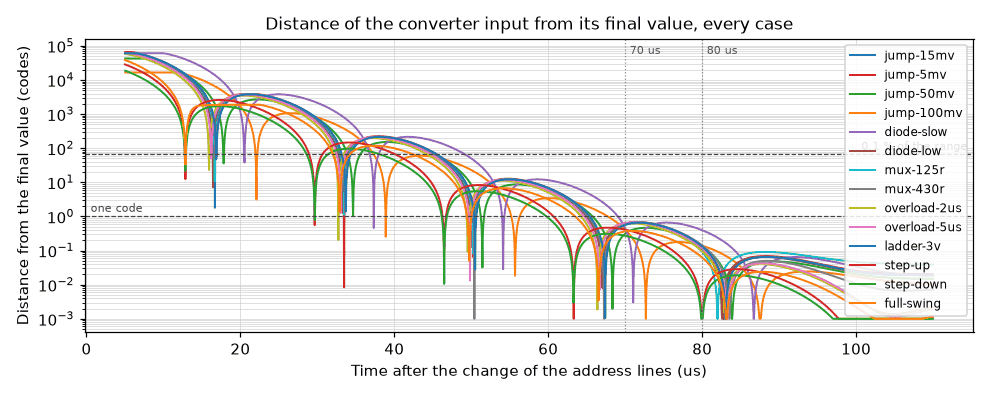
simulation/results/signal_chain/settling.errors.png
