Guiimartinho/esp32-s3-power-profiler/simulation/results/signal_chain/transfer.transfer.png

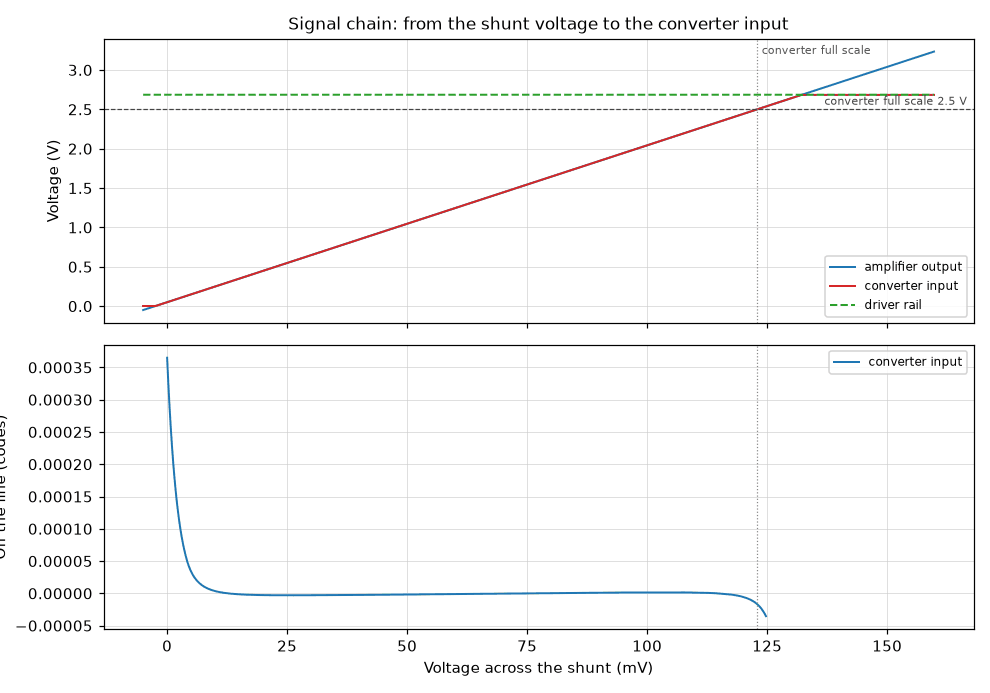
simulation/results/signal_chain/transfer.transfer.png
