Guiimartinho/esp32-s3-power-profiler/simulation/results/source_meter/enable.sweep.png

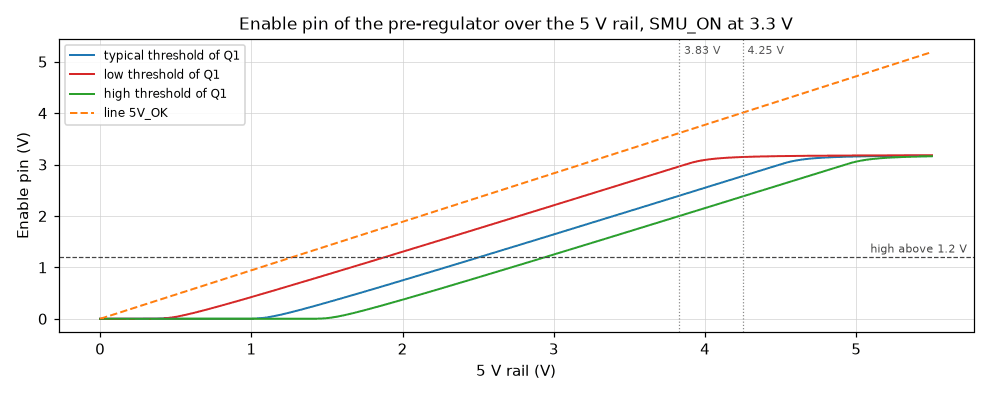
simulation/results/source_meter/enable.sweep.png
