Guiimartinho/esp32-s3-power-profiler/simulation/results/source_meter/external.plug.png

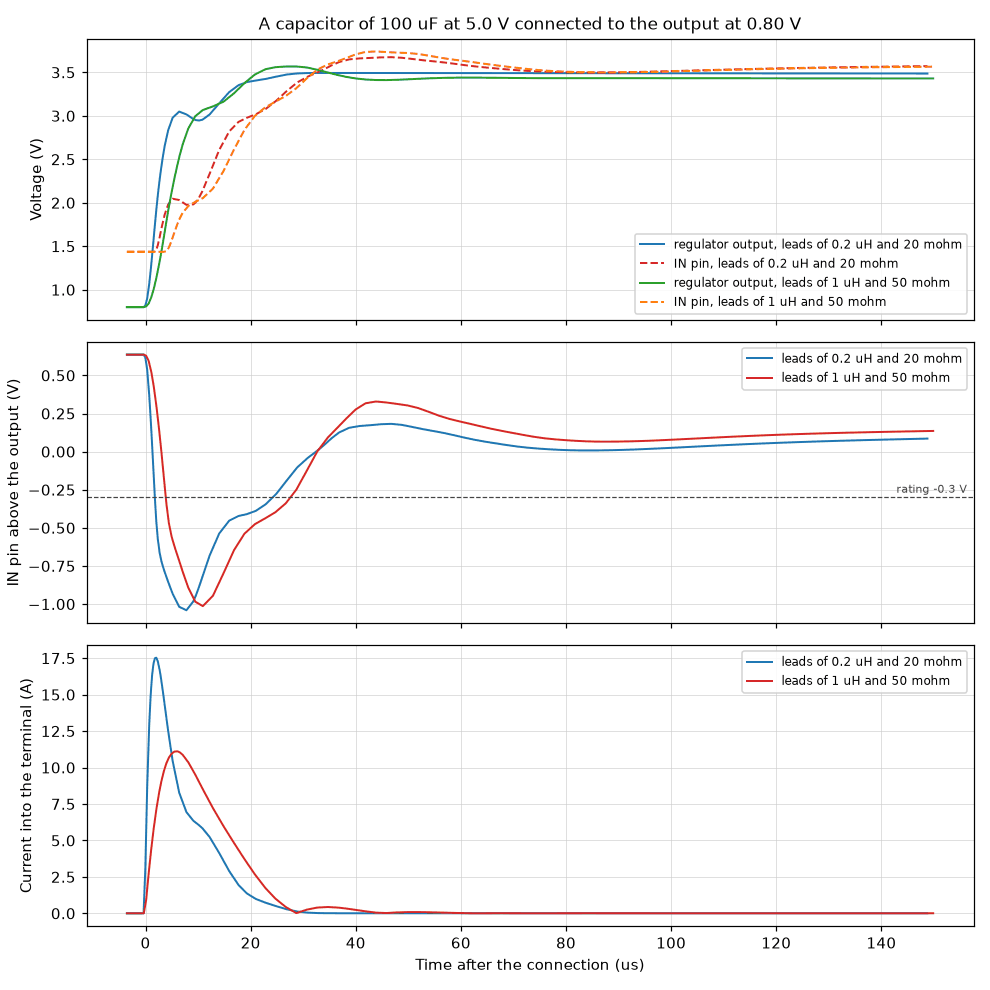
simulation/results/source_meter/external.plug.png
