Guiimartinho/esp32-s3-power-profiler/simulation/results/source_meter/external.slow.png

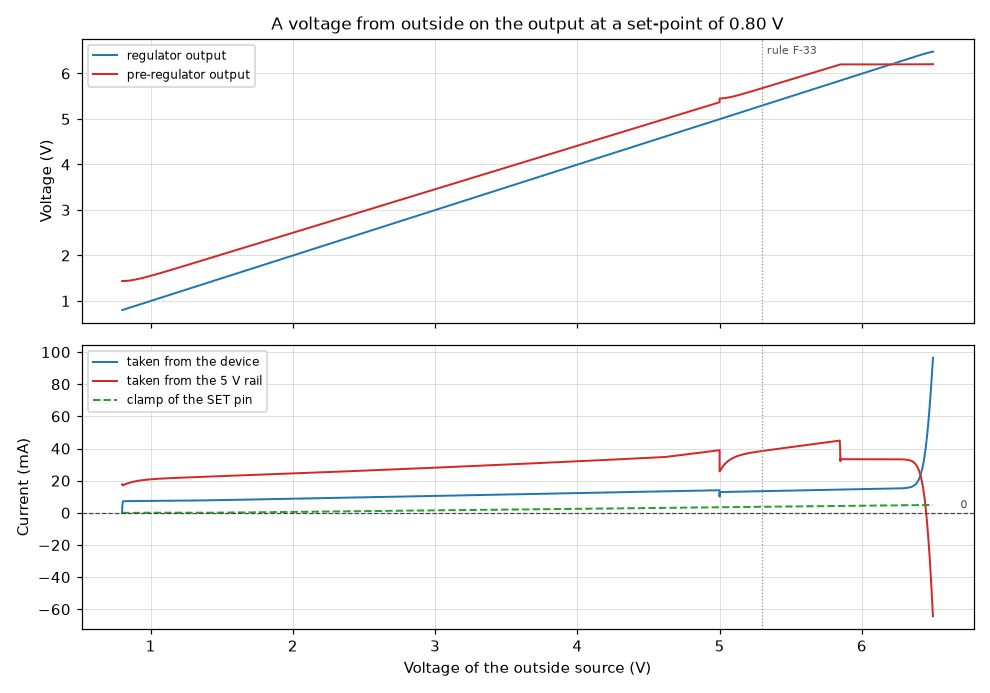
simulation/results/source_meter/external.slow.png
