Guiimartinho/esp32-s3-power-profiler/simulation/results/source_meter/filter.impedance.png

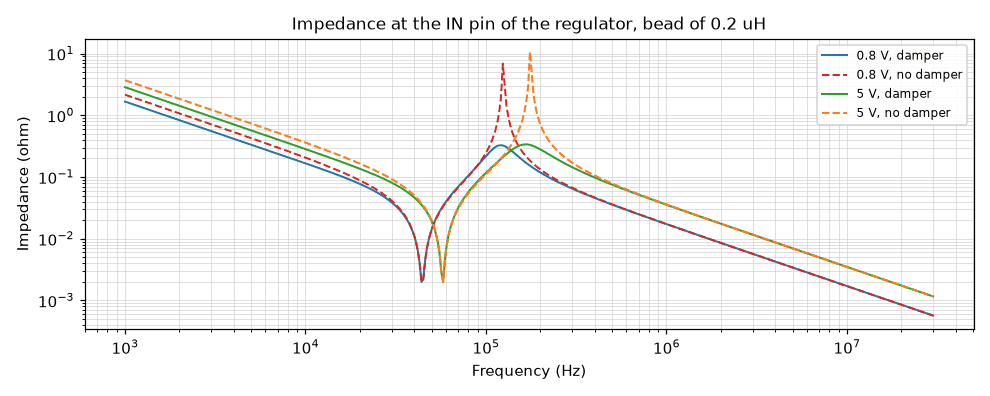
simulation/results/source_meter/filter.impedance.png
