Guiimartinho/esp32-s3-power-profiler/simulation/results/source_meter/loop.amplifier.png

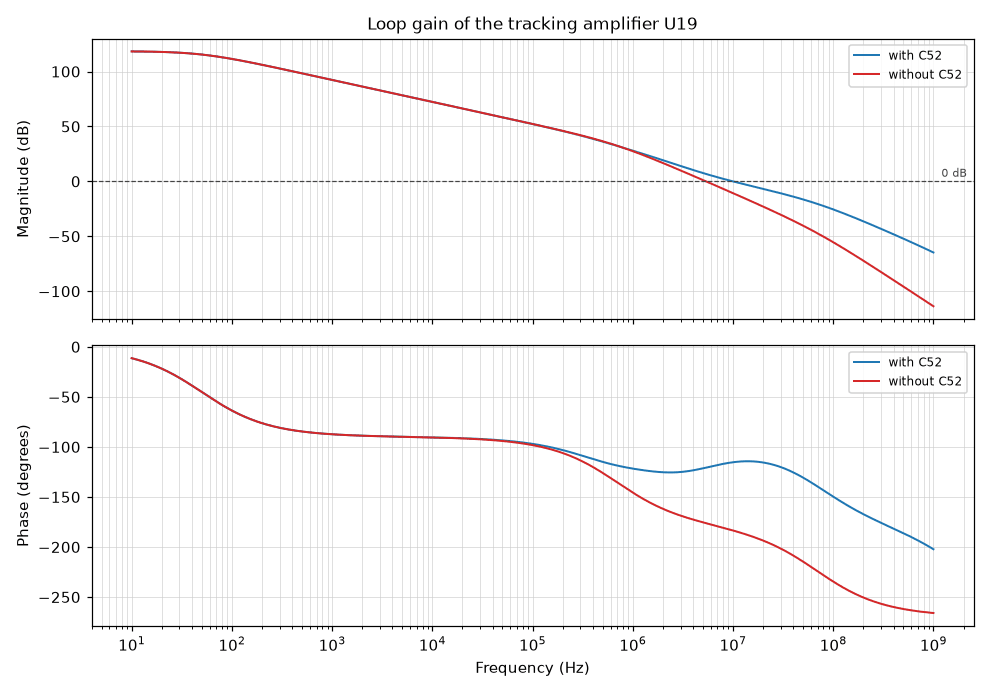
simulation/results/source_meter/loop.amplifier.png
