Guiimartinho/esp32-s3-power-profiler/simulation/results/source_meter/loop.converter.png

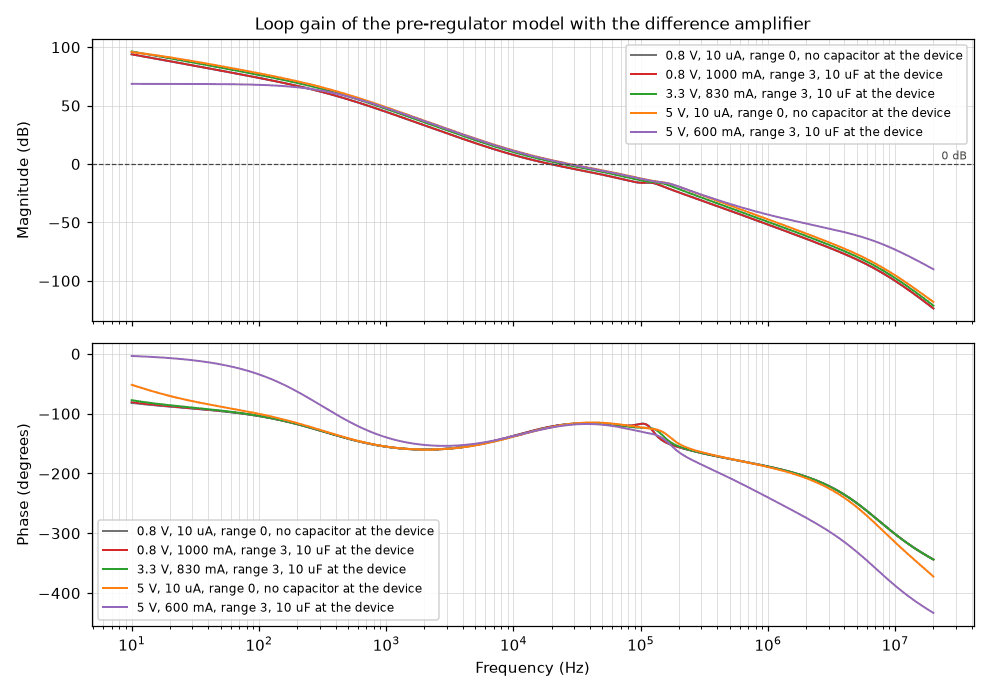
simulation/results/source_meter/loop.converter.png
