Guiimartinho/esp32-s3-power-profiler/simulation/results/source_meter/loop.regulator.png

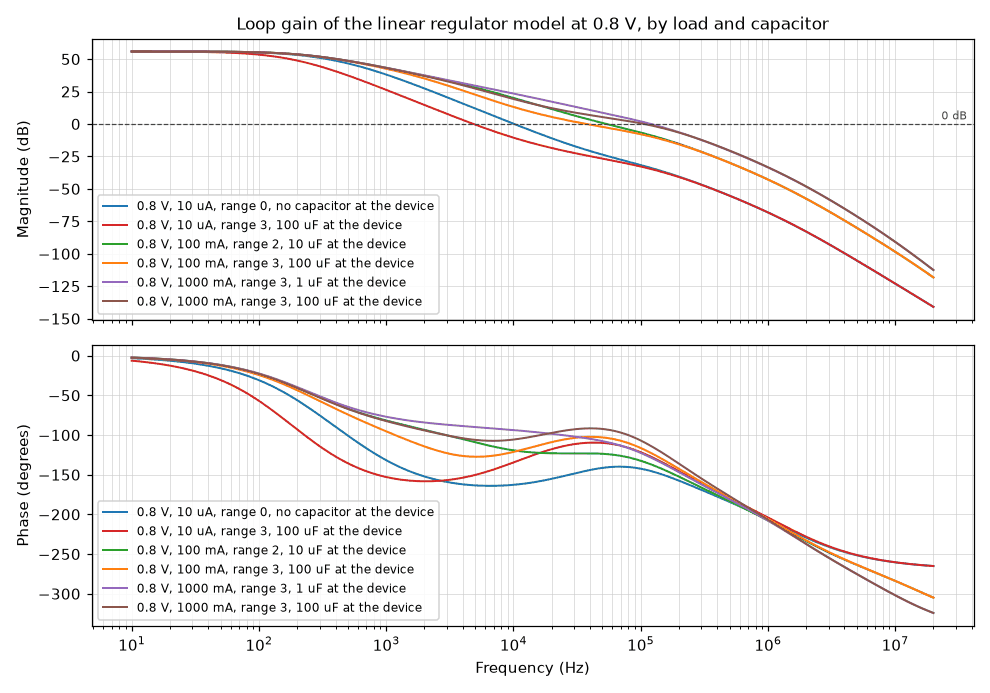
simulation/results/source_meter/loop.regulator.png
