Guiimartinho/esp32-s3-power-profiler/simulation/results/source_meter/noise.density.png

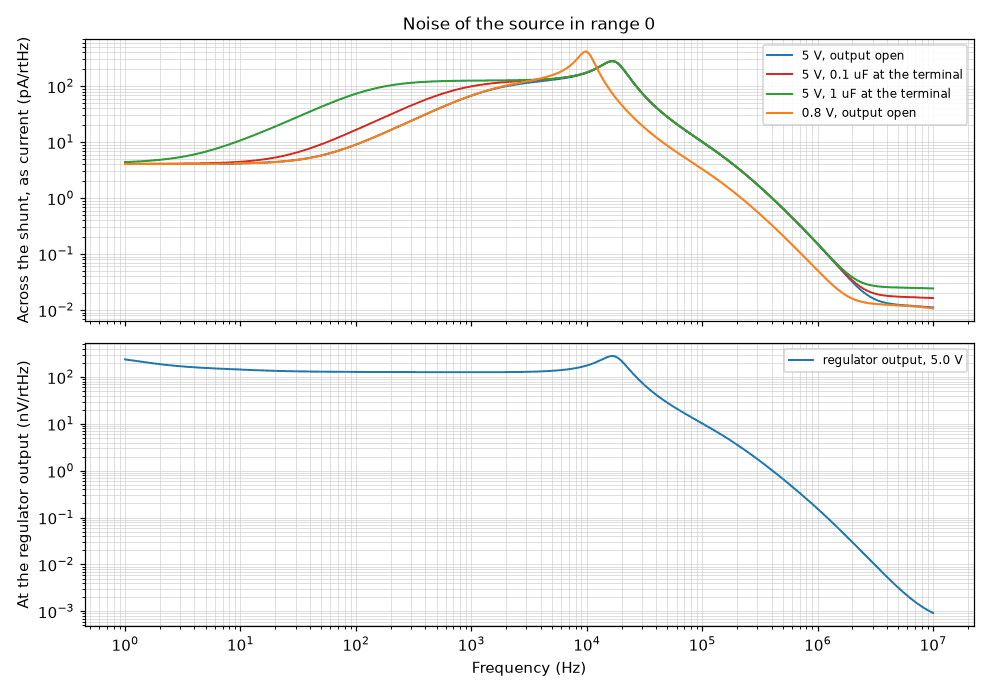
simulation/results/source_meter/noise.density.png
