Guiimartinho/esp32-s3-power-profiler/simulation/results/source_meter/pre-regulator.run-3p3v.png

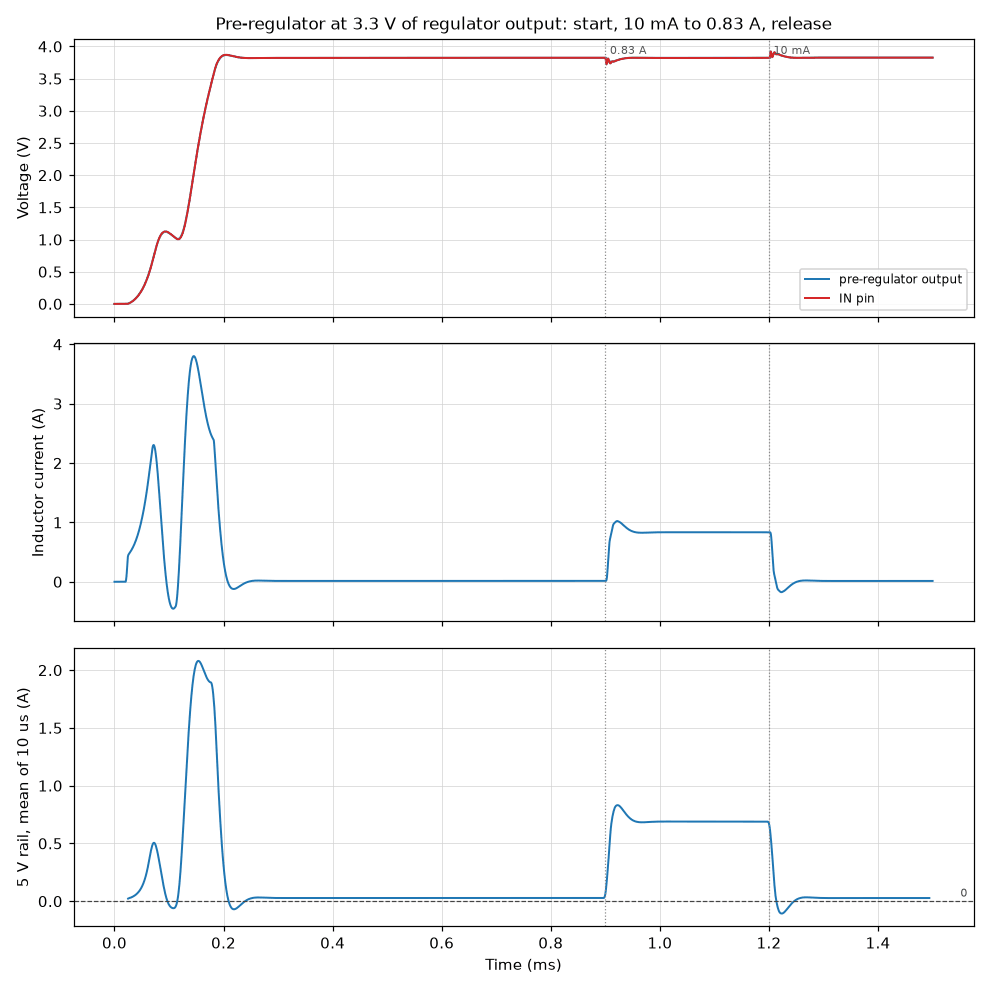
simulation/results/source_meter/pre-regulator.run-3p3v.png
