Guiimartinho/esp32-s3-power-profiler/simulation/results/source_meter/rails.hold-off.png

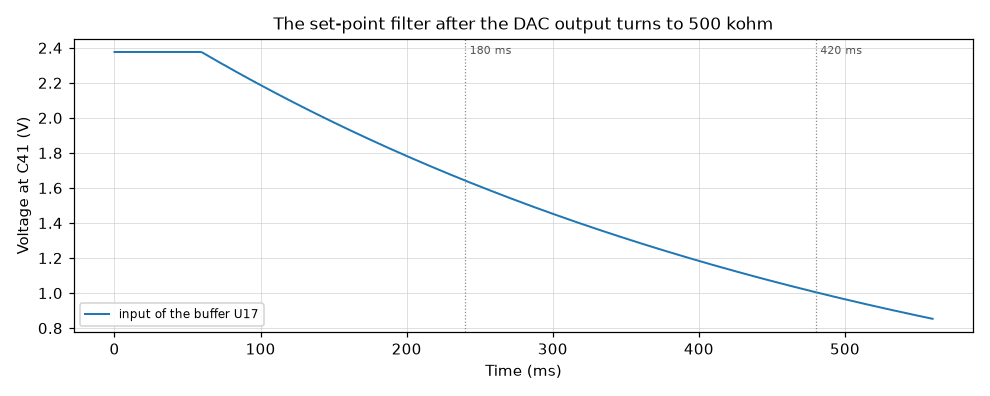
simulation/results/source_meter/rails.hold-off.png
