Guiimartinho/esp32-s3-power-profiler/simulation/results/source_meter/rails.power-off-1ms.png

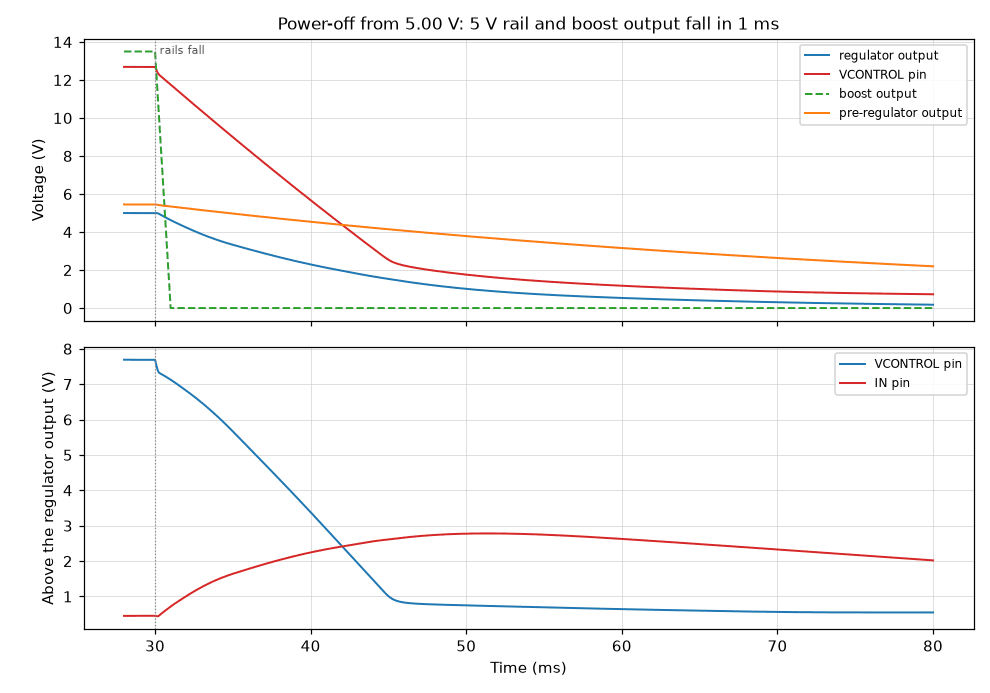
simulation/results/source_meter/rails.power-off-1ms.png
