Guiimartinho/esp32-s3-power-profiler/simulation/results/source_meter/sequence.enable.png

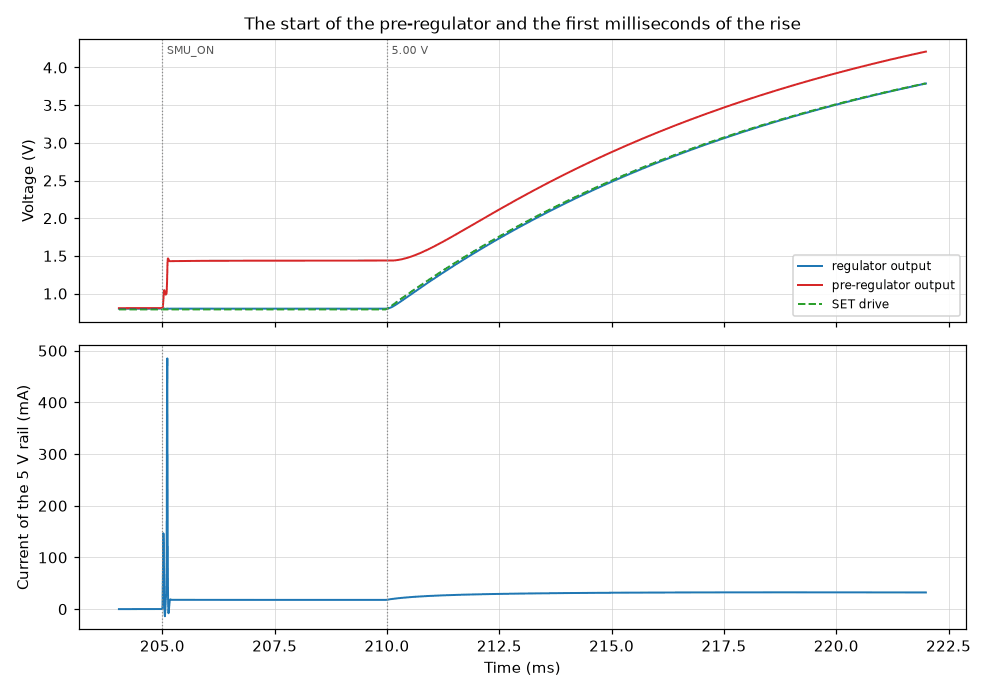
simulation/results/source_meter/sequence.enable.png
