Guiimartinho/esp32-s3-power-profiler/simulation/results/source_meter/sequence.released.png

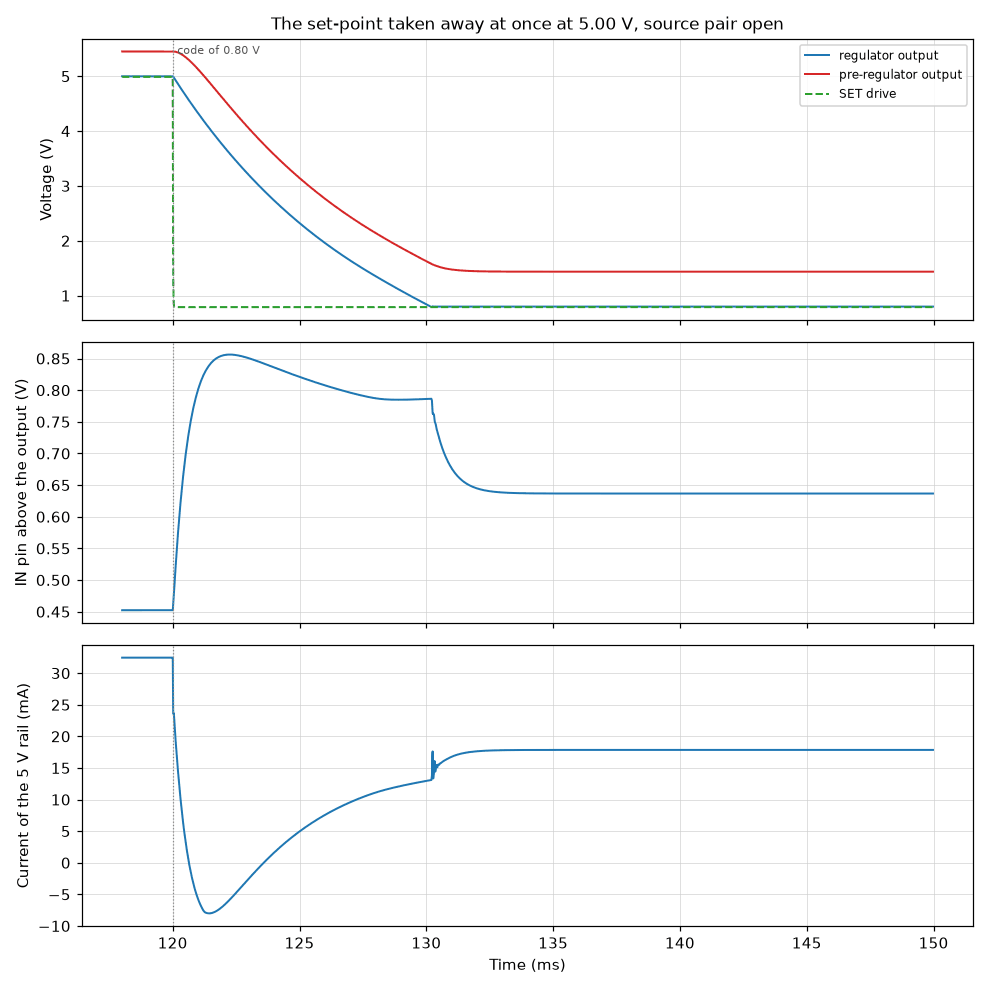
simulation/results/source_meter/sequence.released.png
