Guiimartinho/esp32-s3-power-profiler/simulation/results/source_meter/setpoint.transfer.png

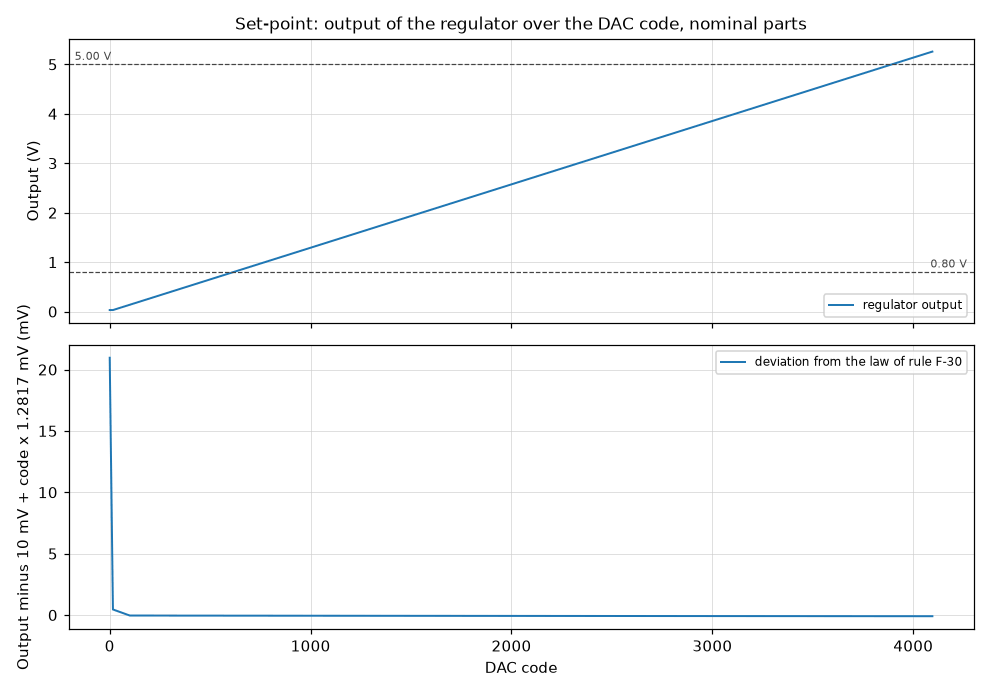
simulation/results/source_meter/setpoint.transfer.png
