Guiimartinho/esp32-s3-power-profiler/simulation/results/source_meter/short.output-0v8.png

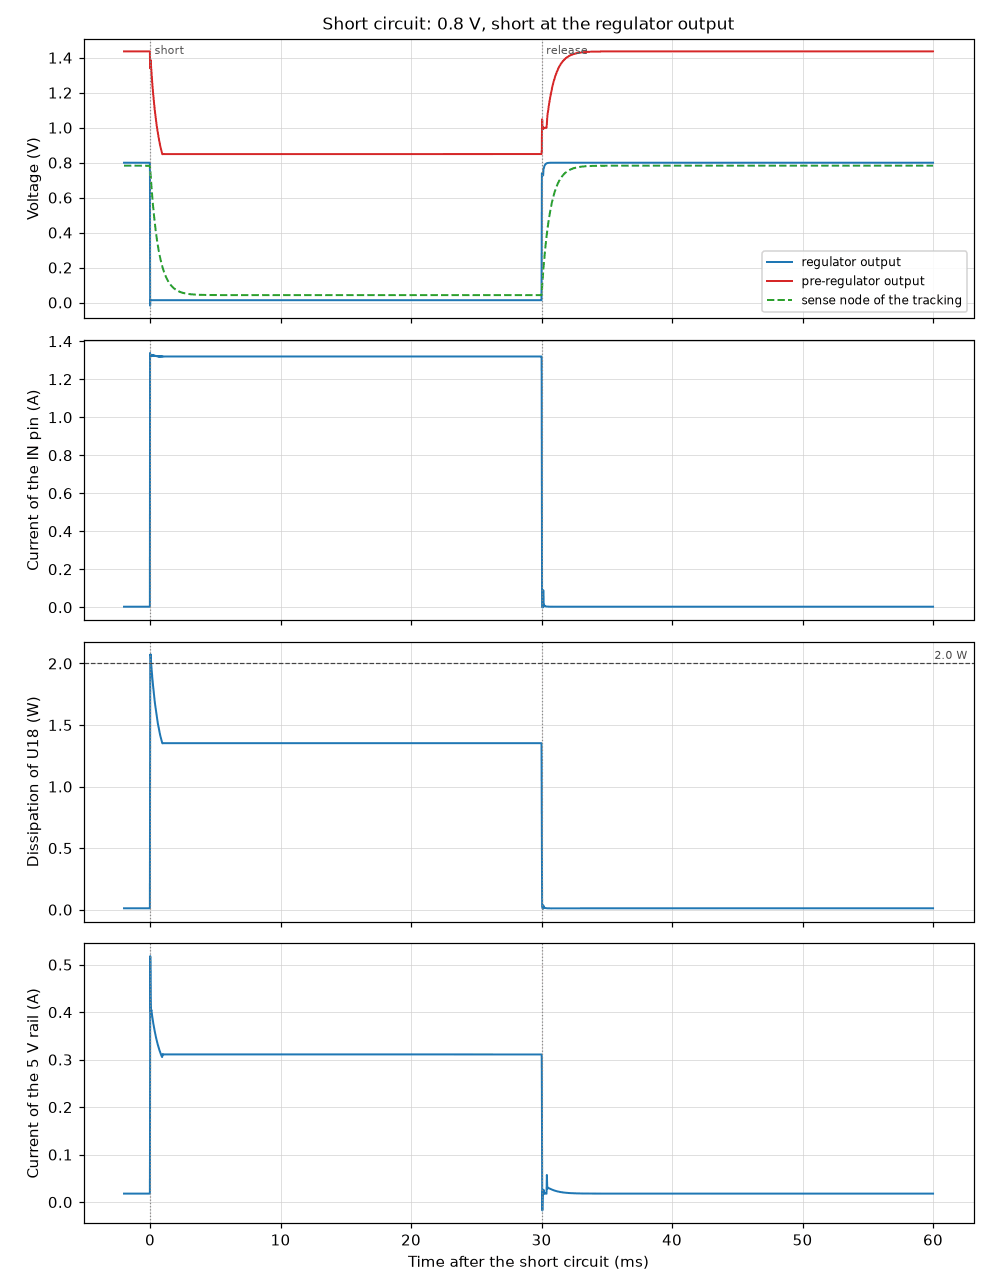
simulation/results/source_meter/short.output-0v8.png
