Guiimartinho/esp32-s3-power-profiler/simulation/results/source_meter/short.output-5v.png

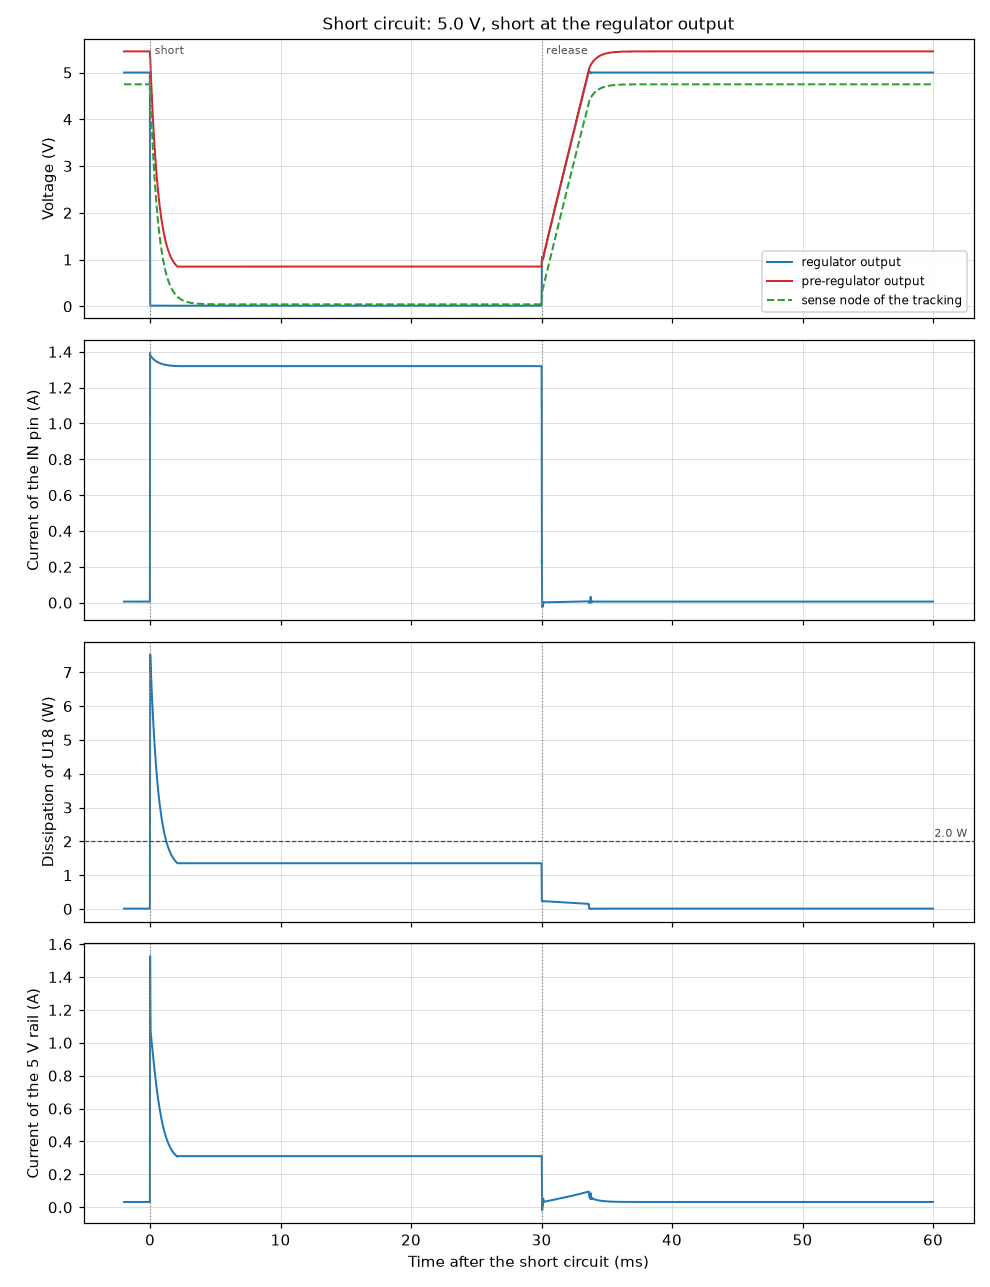
simulation/results/source_meter/short.output-5v.png
