Guiimartinho/esp32-s3-power-profiler/simulation/results/source_meter/tracking.law.png

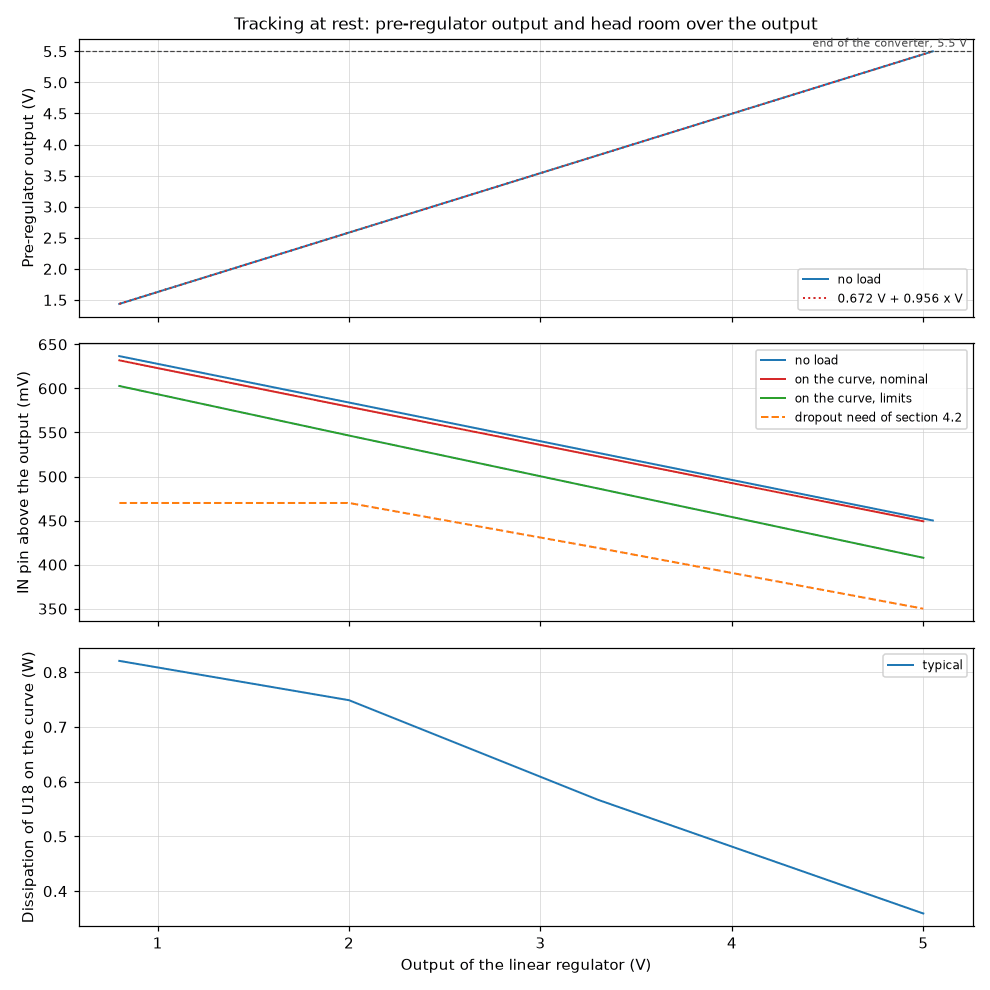
simulation/results/source_meter/tracking.law.png
