Guiimartinho/esp32-s3-power-profiler/simulation/results/system/profile.profile.png

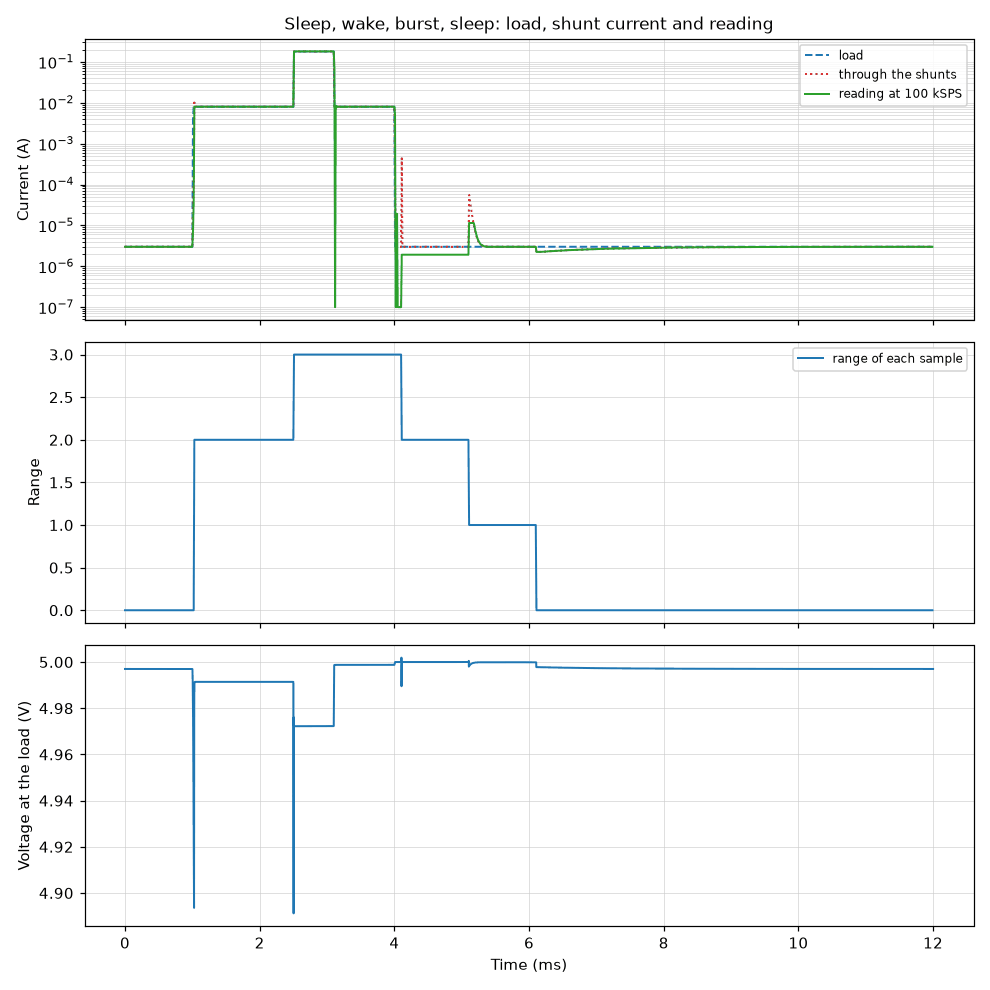
simulation/results/system/profile.profile.png
