Guiimartinho/esp32-s3-power-profiler/simulation/results/system/profile.wake.png

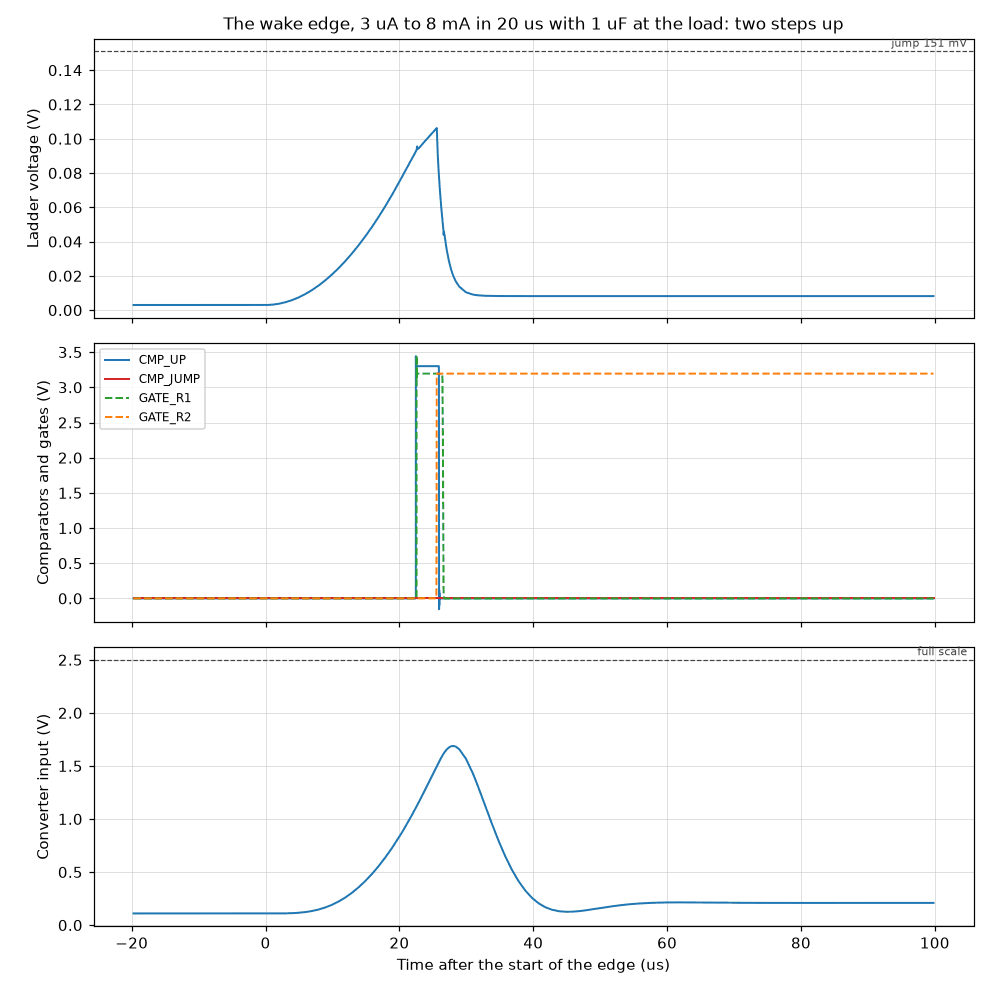
simulation/results/system/profile.wake.png
