Guiimartinho/esp32-s3-power-profiler/simulation/results/digital/monitor-sampling.alone-1000sps.cir

* Channel 0 alone at 1000 SPS, sampling capacitor from 0 V each time
.include "../../models/digital.lib"
RRN1_1 gp12 c_miso 2200
RRN1_2 gp13 c_mon_cs 2200
RRN1_3 gp14 c_sck 2200
RRN1_4 gp15 c_mosi 2200
RRN2_1 c_miso 0 4700
RRN2_2 gp13 v3a 4700
RRN2_3 gp14 0 4700
RRN2_4 gp15 0 4700
XU15_1 c_dac_cs v3a 0 DIGITAL_INPUT_PIN
XU15_2 c_sck v3a 0 DIGITAL_INPUT_PIN
XU15_3 c_mosi v3a 0 DIGITAL_INPUT_PIN
XU39 v3a temp_out 0 DIGITAL_MCP9700A
XU40 ch0 ch1 ch2 ch3 ch4 ch5 ch6 ch7 0 c_mon_cs c_mosi c_miso c_sck 0 vref v3a DIGITAL_MCP3208 reset=1 vres=0
C102 v3a 0 1e-07
C103 ch0 0 1e-07
C104 ch1 0 1e-07
C105 ch2 0 1e-07
C106 ch3 0 1e-07
C107 ch4 0 1e-07
C108 ch5 0 1e-07
C109 ch6 0 1e-07
C110 ch7 0 1e-07
C111 v3a 0 1e-07
C112 v3a 0 1e-06
C113 vref 0 1e-07
R140 vout_buf ch0 120000
R141 vin_p ch1 430000
R142 v5 ch2 120000
R143 ch2 src_st 68100
R144 cc1 ch3 10000
R145 cc2 ch4 10000
R146 temp_out ch5 1000
R147 v12 ch6 47000
R148 vref ch7 100000
R149 ch0 0 100000
R150 ch1 0 10000
R151 ch2 0 100000
R152 ch6 0 10000
R153 ch7 vm4 200000
* what the channels read, as ideal sources
Vout vout_buf 0 5.5
Vin vin_p 0 5
Vrail v5 0 5
Vcc1 cc1 0 0.92
Vcc2 cc2 0 0
Vp12 v12 0 12
Vm4 vm4 0 -4
Vref vref 0 2.5
Vanalog v3a 0 3.3
* the select of the DAC rests high; its pad and resistors are not here
Vdac c_dac_cs 0 3.3
* the 3.3 V rail of the module, an ideal source
Viovdd iovdd 0 3.3
* three pads of the controller drive the bus, one reads
Xgp13 gp13 gp13_ctl gp13_oe iovdd 0 DIGITAL_RP2350_PAD roh=170 rol=125 cpad=5e-12 e9=0
Xgp14 gp14 gp14_ctl gp14_oe iovdd 0 DIGITAL_RP2350_PAD roh=170 rol=125 cpad=5e-12 e9=0
Xgp15 gp15 gp15_ctl gp15_oe iovdd 0 DIGITAL_RP2350_PAD roh=170 rol=125 cpad=5e-12 e9=0
Xgp12 gp12 gp12_ctl gp12_oe iovdd 0 DIGITAL_RP2350_PAD roh=170 rol=125 cpad=5e-12 e9=0
Vgp13_ctl gp13_ctl 0 PWL(0 1 0.0002 1 0.000200005 0 0.000239 0 0.000239005 1 0.0012 1 0.001200005 0 0.001239 0 0.001239005 1 0.0022 1 0.002200005 0 0.002239 0 0.002239005 1 0.0032 1 0.003200005 0 0.003239 0 0.003239005 1 0.0042 1 0.004200005 0 0.004239 0 0.004239005 1 0.0052 1 0.005200005 0 0.005239 0 0.005239005 1 0.0062 1 0.006200005 0 0.006239 0 0.006239005 1 0.0072 1 0.007200005 0 0.007239 0 0.007239005 1 0.0082 1 0.008200005 0 0.008239 0 0.008239005 1 0.0092 1 0.009200005 0 0.009239 0 0.009239005 1 0.0102 1 0.010200005 0 0.010239 0 0.010239005 1 0.0112 1 0.011200005 0 0.011239 0 0.011239005 1 0.0122 1 0.012200005 0 0.012239 0 0.012239005 1 0.0132 1 0.013200005 0 0.013239 0 0.013239005 1 0.0142 1 0.014200005 0 0.014239 0 0.014239005 1 0.0152 1 0.015200005 0 0.015239 0 0.015239005 1 0.0162 1 0.016200005 0 0.016239 0 0.016239005 1 0.0172 1 0.017200005 0 0.017239 0 0.017239005 1 0.0182 1 0.018200005 0 0.018239 0 0.018239005 1 0.0192 1 0.019200005 0 0.019239 0 0.019239005 1 0.0202 1 0.020200005 0 0.020239 0 0.020239005 1 0.0212 1 0.021200005 0 0.021239 0 0.021239005 1 0.0222 1 0.022200005 0 0.022239 0 0.022239005 1 0.0232 1 0.023200005 0 0.023239 0 0.023239005 1 0.0242 1 0.024200005 0 0.024239 0 0.024239005 1 0.0252 1 0.025200005 0 0.025239 0 0.025239005 1 0.0262 1 0.026200005 0 0.026239 0 0.026239005 1 0.0272 1 0.027200005 0 0.027239 0 0.027239005 1 0.0282 1 0.028200005 0 0.028239 0 0.028239005 1 0.0292 1 0.029200005 0 0.029239 0 0.029239005 1 0.0302 1 0.030200005 0 0.030239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
